Fitzer34/bor-systems/marketing/SALES_ONEPAGER.md

# HazardLink — Sales One-Pager

For warm intros, prospect handouts, and follow-up emails.

---

```
┌─────────────────────────────────────────────────────────────┐
│   HazardLink ⚠️                                              │
│   Smart wet-floor monitoring for commercial facilities       │
└─────────────────────────────────────────────────────────────┘
```

## The problem

Slip-and-fall is the **#1 cause of serious accidents** in commercial
premises — and a single incident can run to **tens of thousands** in
downtime, legal, and medical costs. Yet most facilities still rely on a
cleaner manually placing a yellow plastic sign and **hoping someone
moves it back**.

When the sign disappears, three things happen:

1. The cleaner has no idea
2. The supervisor has no proof of response time
3. There's no record it was ever dealt with

## The HazardLink fix

A sub-€1 magnetic sensor inside every wet-floor sign mount. The moment
a sign is lifted off the wall, the cloud knows. The cleaning team gets
a push notification within 3 seconds. Every event is timestamped and
photo-verified. The whole audit chain is cryptographically signed —
tamper-evident, so the record holds up.

## What the customer gets

| Feature | Outcome |
|---|---|
| Real-time push alerts | Average response time drops from 8 min → under 2 min |
| AirTag-style precision finding (UWB) | Cleaners locate the sign in any building in seconds |
| Auto-generated reports & records | A complete, exportable safety record — prove the job was done |
| Photo verification on close | Disputes resolved with evidence, not arguments |
| Multi-language alerts (6 languages) | Polish/Portuguese cleaners react faster |
| Anti-theft detection | Saves €300-600/yr in sign replacement |
| Heat-map analytics | Identifies repeat-offender zones (leaky vending machines, wet entrances) |
| Slack + Teams integration | Alerts post in the channel cleaning teams already use |

## How it installs

```
1. Wall-mount a hanger where each sign normally lives    (5 min each)
2. Plug a gateway box into power + Wi-Fi                 (10 min, once per building)
3. Hang your existing wet-floor signs on the hangers     (instant)
4. Cleaners install the iPhone / Android app             (5 min each)
5. Done — alerts start immediately
```

## Pricing

| Tier | Site size | Setup | Monthly |
|---|---|---|---|
| **Small** | Up to 10 hangers | €1,500 hardware | €30 / month |
| **Multi-site** | Up to 50 hangers | €6,500 hardware | €100 / month |
| **Enterprise** | 200+ hangers | €25,000+ hardware | €350 / month |

Hardware is a one-time purchase. Software subscription is month-to-month
— cancel any time with 30 days' notice.

## ROI for a 50-hanger site

The biggest return is preventing the incident in the first place — **one
avoided slip-and-fall pays for HazardLink for years.** On top of that, the
day-to-day savings:

| Item | Annual value |
|---|---|
| Anti-theft sign-replacement savings | €400 |
| Cleaner labour saved (faster response = less downstream cleanup) | €1,200 |
| Faster, evidenced incident handling | €3,000+ |
| **Ongoing savings** | **€4,600+ / year** |
| **Cost (hardware amortised over 5 years + €1,200 SaaS)** | **€2,500 / year** |

## Who's using it

(Pilot phase — willing to share names of design-partner sites once they
agree)

## Why us, why now

- **Built in Ireland**, hosted in EU — your data stays in your jurisdiction
- **No long contracts** — month-to-month, cancel any time
- **GDPR-native** — designed compliance-first, not bolted on
- **No replacement of your existing signs** — we make YOUR signs smart
- **Multi-language** — supports the actual labour pool in UK/IE cleaning

## Next step

15-minute demo on a live device — we show the alert flow on your own
phone within the first 90 seconds.

**Book**: hello@hazardlink.ie
**More**: https://hazardlink.ie
