Fitzer34/bor-systems/marketing/STORE_LISTINGS.md

# HazardLink — App Store + Play Store listings

Copy-paste-ready text for Apple App Store and Google Play Store
submissions. Both stores have character limits — these stay under them.

---

## App name
**HazardLink** (10 chars — well within Apple's 30 / Google's 50)

## Subtitle / Short description (Apple 30 / Google 80 chars)

**Apple**: `Smart wet-floor sign alerts`
**Google**: `Real-time alerts the moment a wet-floor sign is moved. Built-in safety records.`

---

## Promotional text (Apple, 170 chars, can be updated without re-review)

```
The moment a wet-floor sign is lifted, your cleaning team gets an alert — and every response is logged automatically. Built for facility safety teams.
```

---

## Full description (Apple 4000 chars / Google 4000 chars)

```
HazardLink turns ordinary wet-floor signs into connected safety sensors.
The moment one is lifted off its mount, your cleaning team gets a push
notification, the dashboard goes red, and the response is logged — every
step, with timestamps and photo evidence, so nothing slips through the cracks.

—— Why HazardLink ——

• REAL-TIME ALERTS — Phone, Apple Watch / Wear OS, Slack and Teams. You
  always know when a spill happens.

• AIRTAG-STYLE FIND — Ultra-Wideband precision finding (UWB) walks your
  cleaners straight to the lifted sign in any building. cm-level
  accuracy on iPhone 11+, Pixel 6 Pro+, Galaxy S21 Ultra+.

• REPORTS & RECORDS — Auto-generated reports document every spill,
  response time, and resolution. A complete, exportable safety record
  for your own health-and-safety reviews and accountability.

• PHOTO PROOF — Cleaners snap a quick photo of the cleaned area before
  closing each alert. Tamper-resistant audit trail.

• MULTI-LANGUAGE — Notifications in English, Polish, Portuguese,
  Spanish, Romanian and Lithuanian. Your cleaning team understands
  alerts in their native language.

• ANTI-THEFT — Signs that go missing for 24h auto-alert your admin
  team. Save €300–600 per year in replacement costs.

• HEAT-MAP ANALYTICS — Discover which zones are repeat offenders.
  Fix the root cause, not just the symptom.

• AFTER-HOURS MODE — Different escalation policy at night. Alerts
  route to your security guard rather than waking the cleaning team.

• SLACK + TEAMS — Post alerts straight into your existing channel.

—— How it works ——

1. We supply small hangers that mount on the wall (one per sign).
2. You hang your own existing wet-floor signs on them.
3. A magnet inside each sign keeps the hanger "armed".
4. The moment a cleaner lifts the sign, the magnetic field changes
   and a sub-€1 Hall sensor fires the alert.
5. The alert reaches phones, watches, and the web dashboard in
   under 5 seconds.

—— Who it's for ——

• Commercial cleaning companies managing multiple client sites
• Facility managers in offices, retail, hospitality, healthcare
• Health &amp; safety officers responsible for slip/trip prevention
• Any business where a sudden spill needs a cleaning response

—— Hardware ——

Hangers run on a single rechargeable 21700 lithium cell — one charge
per year. Sign tags use replaceable CR2032 cells (2-year life). Gateway
is a small Wi-Fi puck (one per building, USB-C powered).

—— Open standards ——

LoRa for sign-to-gateway communication. BLE for first-time Wi-Fi setup.
UWB for precision finding. Multi-tenant cloud with end-to-end HMAC.
Sentry monitoring. Public status page.

Questions? hello@hazardlink.ie
```

---

## Keywords (Apple, 100 chars comma-separated)

```
spill,floor,safety,sign,cleaning,alert,compliance,facility,janitor,hazard,IoT,monitoring,wet,slip
```

---

## Categories

**Apple**:
- Primary: **Business**
- Secondary: **Productivity**

**Google**:
- Category: **Business**
- Tags: business management, safety, IoT

---

## Content rating

**Apple**: 4+ (no objectionable content)
**Google**: Everyone

---

## Privacy nutrition (Apple — what your app collects)

Data linked to user identity:
- Contact Info: email address (for account)
- Identifiers: device ID (for push notifications)
- Diagnostics: crash data (Sentry, no PII)

Data NOT linked to user identity:
- Usage data: alert response times (aggregated for analytics)

Data NOT collected:
- Location, photos (other than user-uploaded resolution photos), audio,
  contacts, browsing history, advertising data.

---

## Data safety (Google Play — same info, different form)

Data collected: email, device push token, photos uploaded by user
Data shared: NO (we don't share data with third parties beyond service providers)
Encryption in transit: YES (TLS 1.2+)
Data deletion request: support@hazardlink.ie

---

## Screenshots needed (both stores)

Suggested 5 screenshots per device size:

1. **Live alerts feed** — Active alert with red pin on floor plan
2. **AirTag-style Find Sign view** — arrow + distance
3. **Reports preview** — page with summary + response times
4. **Multi-site dashboard** — grid of buildings sorted by open alerts
5. **Heat-map analytics** — zones colour-coded by spill frequency

Device sizes Apple requires:
- 6.7" iPhone (1290×2796)
- 6.5" iPhone (1242×2688)
- iPad Pro 13" (2064×2752) — only if you ship iPad-compatible (we don't)

Device sizes Google requires:
- Phone: 1080×1920 minimum
- 7" tablet: 1200×1920
- 10" tablet: 1920×2560

Use Figma or Sketch to mockup; or take real screenshots from your dev
device and add a phone frame in a tool like https://mockuphone.com.

---

## What's new (release notes) — first version

```
Welcome to HazardLink.

This is our first public release. Wet-floor sign monitoring with
real-time push alerts, multi-language notifications, Apple Watch
and Wear OS support, and built-in safety reports.

Pair your first hanger via Bluetooth in 60 seconds.
```

---

## Support URL
https://hazardlink.ie/support

## Marketing URL
https://hazardlink.ie

## Privacy policy URL (REQUIRED both stores)
https://hazardlink.ie/privacy

---

## Beta testing setup

**Apple TestFlight**: invite up to 100 testers via email or public link.
No review for internal builds; ~24h review for external builds.

**Google Play Internal Testing**: invite up to 100 testers via email.
No review. Closed Testing (12+ testers for 14 days) needed before
Production access for new Personal-tier developer accounts.
