Fitzer34/bor-systems/hardware/enclosures/v8/A/README.txt

HazardLink v8 enclosures, Designer A (robust and serviceable)
Generated by hazardlink_enclosures.py. Frame: X right, Z up, Y from the front face into the wall.

FILES
  <part>.step / .stl / .png / _drawing.dxf   printable parts: hanger_body, hanger_lid, hanger_hook, hanger_backplate, gateway_body, gateway_lid
  hanger_assembly.step, gateway_assembly.step  named and coloured assemblies including the reference solids
  hanger_section.dxf, gateway_section.dxf      assembly stack-up sections
  *_exploded.png, *_assembled*.png             previews
  ref/                                          reference solids (board, cell, holder, Hall carrier, magnet, antenna, plug), not printed
  autocad/                                      .sat + 3DSOLID .dxf for AutoCAD for Mac (from to_autocad.py)
  manifest.txt                                  bounding boxes and derived positions

HANGER SERVICE SEQUENCE (unit stays on the wall)
  1. Remove the two M3 pin-Torx button-head screws in the hook base (driver enters between the side gussets, under the arm).
     Lift the hook off its locating pocket, slide the Hall carrier out of the hook slot; it passes through the lid slot.
  2. Remove the four M3 pin-Torx countersunk lid screws. Lift the lid straight off (the lip is 4 mm deep).
  3. The 21700 cell sits in its holder facing you: push it against the spring end and lift it out. Fit the new cell, same polarity.
  4. To swap the board: unplug the JST 1.25 battery lead (under the board, plug enters from the right), unplug the U.FL antenna,
     unsolder or cut the three Hall wires at the board underside pads (J3 pin 1 GND, pin 2 3V3, pin 17 GPIO6), lift the board
     off its rails. No screws hold the board: it rests on the rails and is clamped by the two lid ribs.
  5. Refit in reverse. Insert the cell last, close the lid within the 60 s commissioning window, or press RST (2 mm pinhole) later.
  To take the unit off the wall: with the lid off, remove the internal M3 screw at (50, 62) through the back wall, then lift the body
  14 mm and pull it off the four backplate pegs.

GATEWAY SERVICE SEQUENCE
  1. Remove the six M3 countersunk lid screws, lift the lid.
  2. Unplug the USB-C plug (cable stays tied to the saddle), unplug the U.FL pigtail, lift the board off its rails.

MAGNET DATUM (publish to the sign tag)
  Magnet on the hook centreline (x=50), 8 mm out from the hook base front face (Y=-16), pole face parallel to the arm top surface,
  facing down, with 1.0 mm running clearance and a 1.2 mm tag wall (assumed). Air gap magnet face to Hall package top = 3.98 mm.
  The arm top slopes up 3 mm over its length so the handle slides to the root and rests there.

PRINTING (PETG, 0.4 nozzle, 3 perimeters, 0.2 layers)
  hanger_body: back face down, open front up. Peg pocket roofs bridge 11.5 mm; lead notch bridges 8 mm.
  hanger_lid: outer face down. PRG tab and LED window are thin skins on the bed. Fit the 36 x 19.5 x 1 mm clear insert from inside
  under the two cleats.
  hanger_hook: lying on a side (X) face so layers run along the arm. Counterbores print horizontal.
  hanger_backplate: back face down, pegs print vertical.
  gateway_body: back face down. gateway_lid: outer face down.
  Heat-set inserts: ruthex M3 x 5.7 (4.0 mm holes): 4 lid + 2 hook in the hanger body, 1 security in the backplate, 6 in the gateway body.
  Screws (assumed, not on SHOPPING.md): M3 x 8 countersunk pin-Torx x 4 (hanger lid), M3 x 12 button-head pin-Torx x 2 (hook),
  M3 x 8 countersunk x 6 (gateway lid), M3 x 8 pan head x 1 (internal security screw), 4 + 3 No.8 pan/csk wall screws with plugs.
  Use A2 stainless or brass for the two hook screws (they sit 16 mm from the Hall sensor).

MEASURE BEFORE FREEZING (assumed values in PARAMS)
  The TinyTronics 21700 holder outline (assumed 80 x 25 x 21 mm) and where its leads exit.
  The sign hand-hole and handle bar: hook width 26, arm 45, lip 22 are assumed; the magnet position in the handle must match the datum.
  How far the sign top rises above the handle bar: the OLED window bottom is 42 mm above the arm top at the root.
  The stub antenna diameter and length (clips are for a 6 mm rod, 60 mm long).
  The OLED active area offset (window is 30 x 16 to cover it with margin).
