Fitzer34/bor-systems/hardware/enclosures/ref/heltec-wifi-lora-32-v3/datasheet_p14_physical_dimensions.png

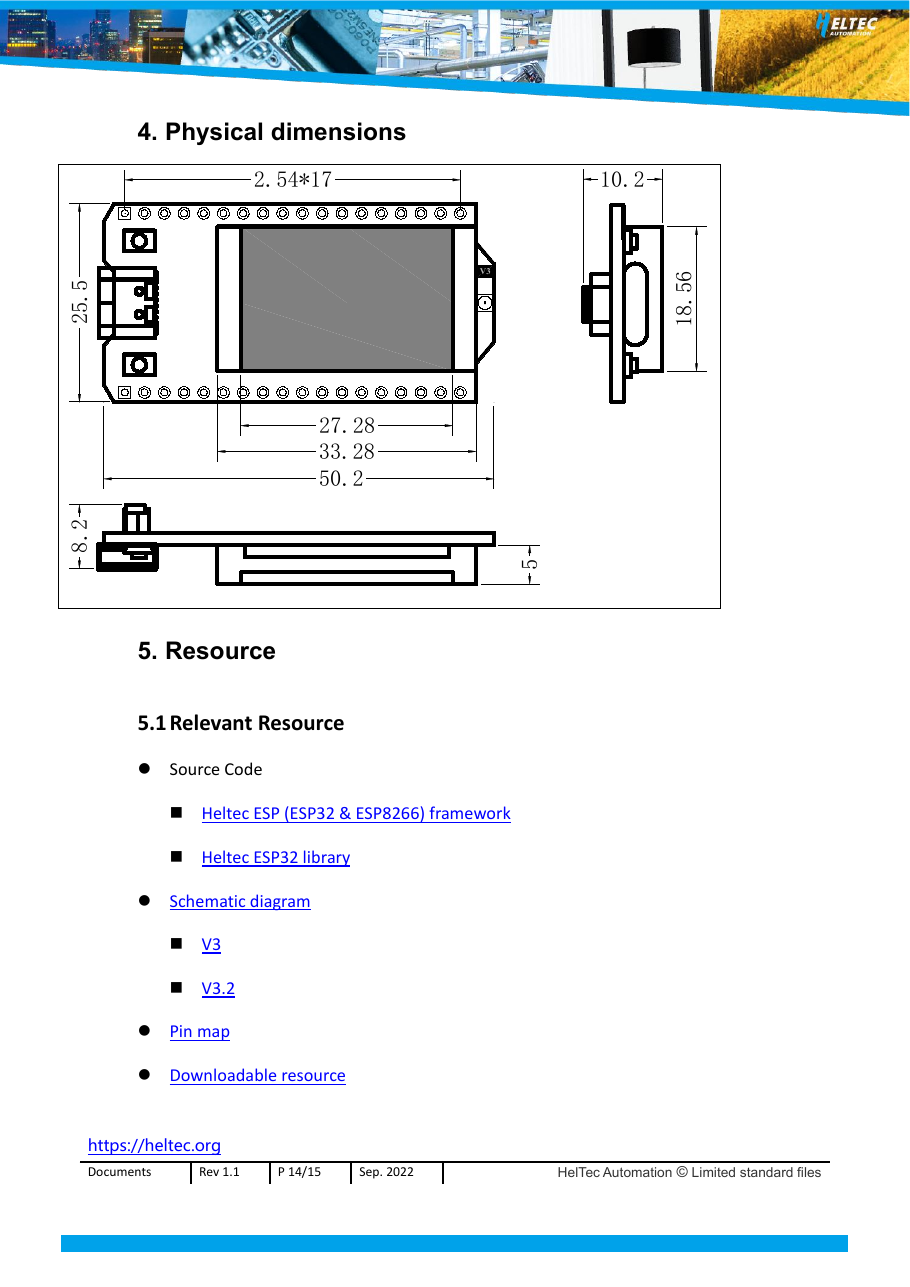
hardware/enclosures/ref/heltec-wifi-lora-32-v3/datasheet_p14_physical_dimensions.png
