Fitzer34/bor-systems/hardware/enclosures/ref/heltec-wifi-lora-32-v3/photo_underside_V3.png

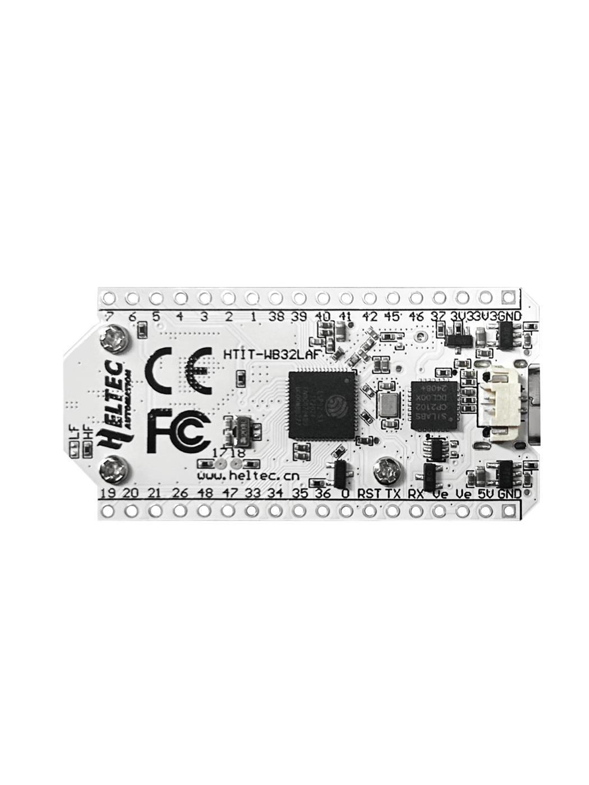
hardware/enclosures/ref/heltec-wifi-lora-32-v3/photo_underside_V3.png
