Fitzer34/bor-systems/hardware/enclosures/ref/heltec-wifi-lora-32-v3/pinmap_V3.2.png

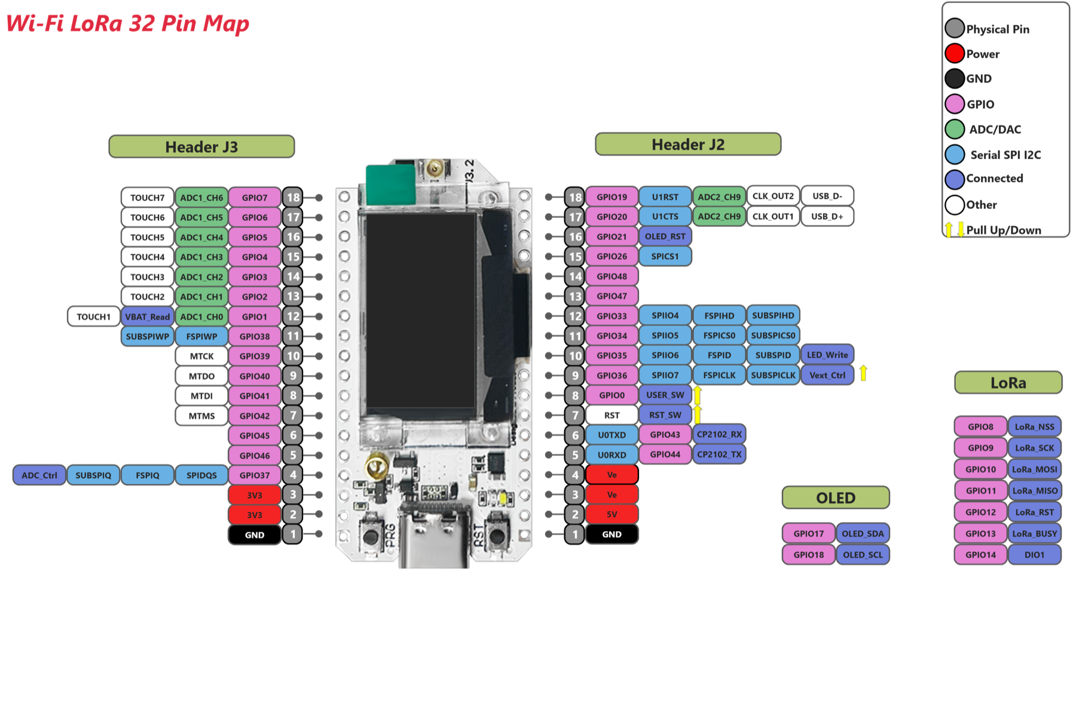
hardware/enclosures/ref/heltec-wifi-lora-32-v3/pinmap_V3.2.png
