Fitzer34/bor-systems/hardware/enclosures/v9/closeups/backplate_front.png

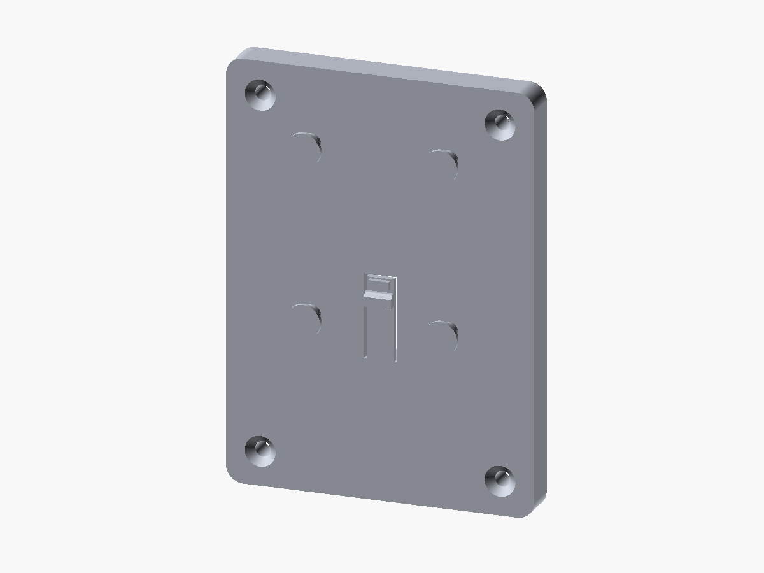
hardware/enclosures/v9/closeups/backplate_front.png
