Fitzer34/bor-systems/hardware/enclosures/v9/closeups/bar_plate.png

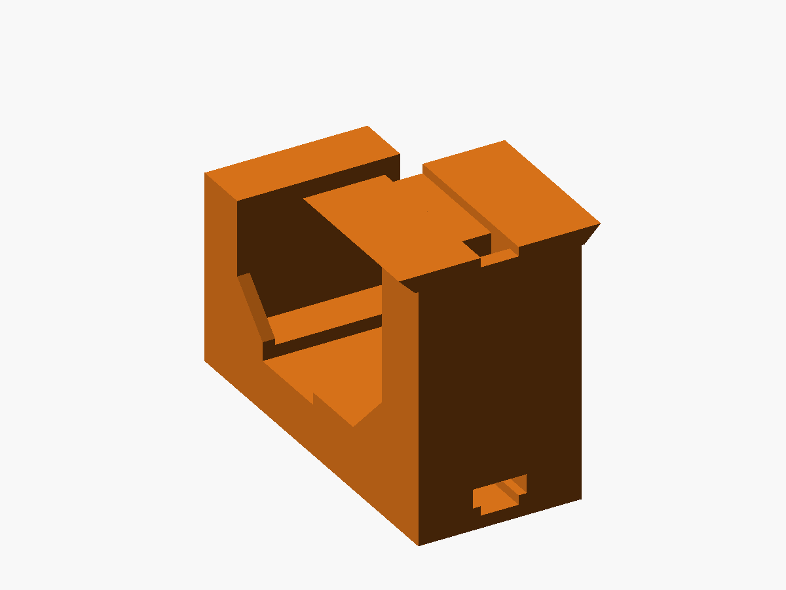
hardware/enclosures/v9/closeups/bar_plate.png
