Fitzer34/bor-systems/hardware/enclosures/v9/closeups/body_bottom.png

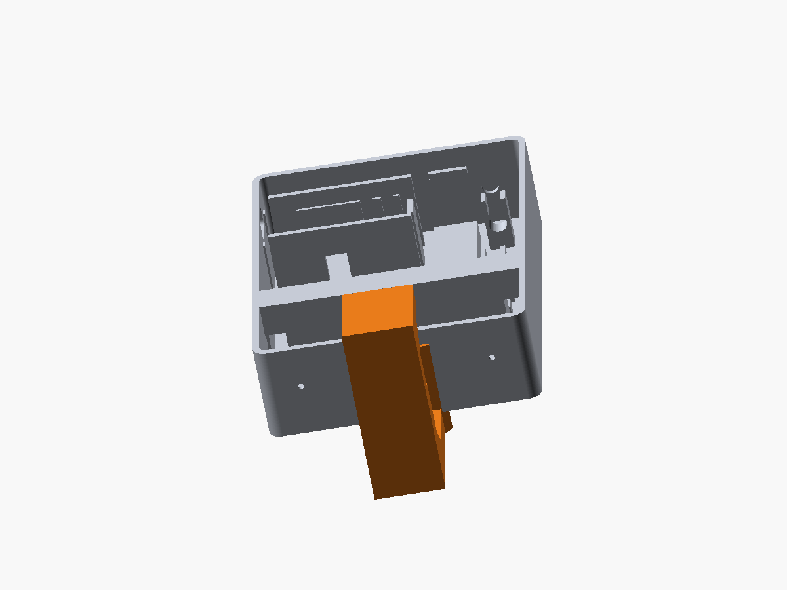
hardware/enclosures/v9/closeups/body_bottom.png
