Fitzer34/bor-systems/hardware/enclosures/v9/closeups/body_top.png

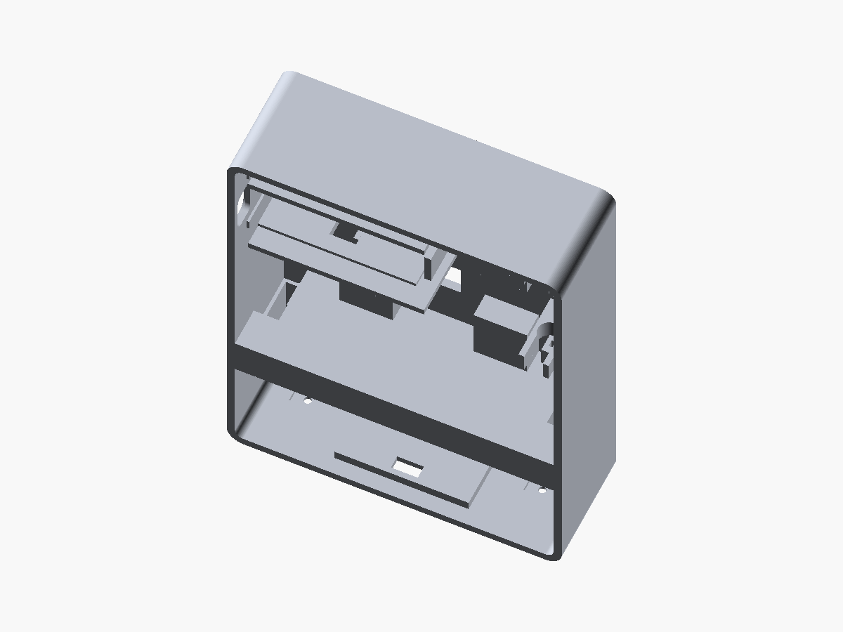
hardware/enclosures/v9/closeups/body_top.png
