Fitzer34/bor-systems/hardware/enclosures/v9/closeups/body_underside.png

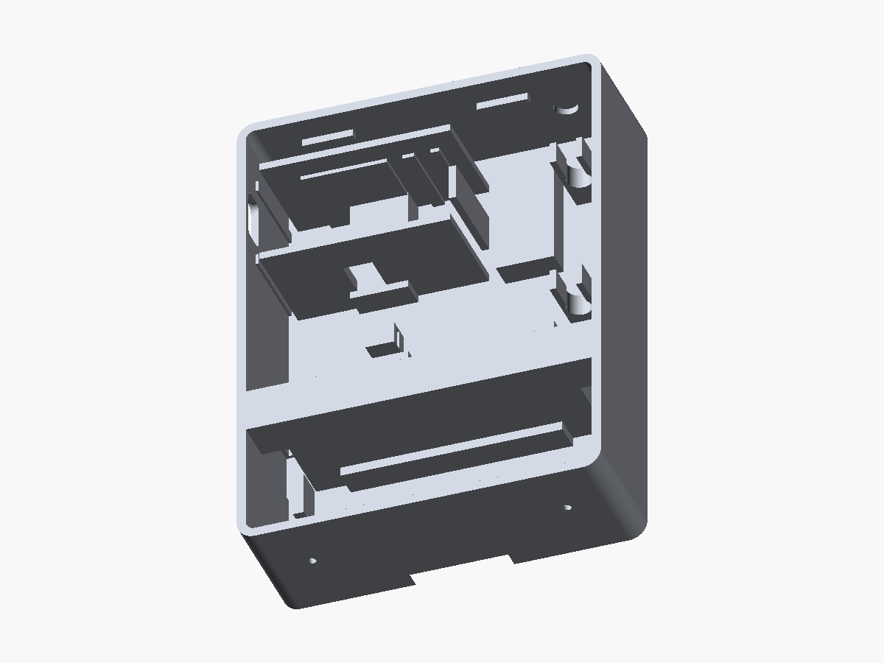
hardware/enclosures/v9/closeups/body_underside.png
