Fitzer34/bor-systems/hardware/enclosures/v9/closeups/coupon.png

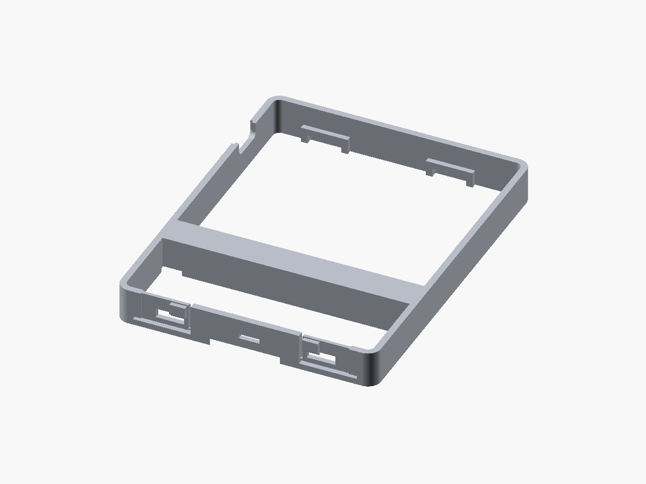
hardware/enclosures/v9/closeups/coupon.png
