Fitzer34/bor-systems/hardware/enclosures/v9/closeups/face_flush.png

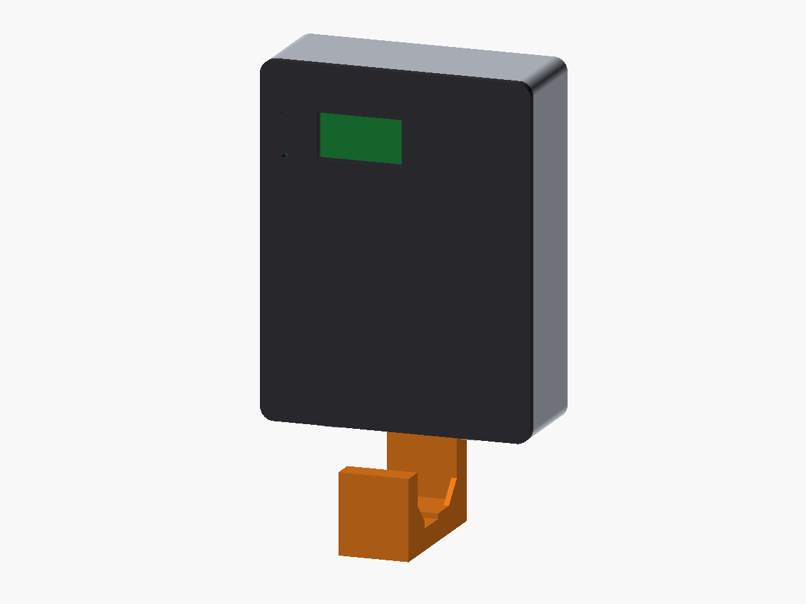
hardware/enclosures/v9/closeups/face_flush.png
