Fitzer34/bor-systems/hardware/enclosures/v9/closeups/finished_gateway.png

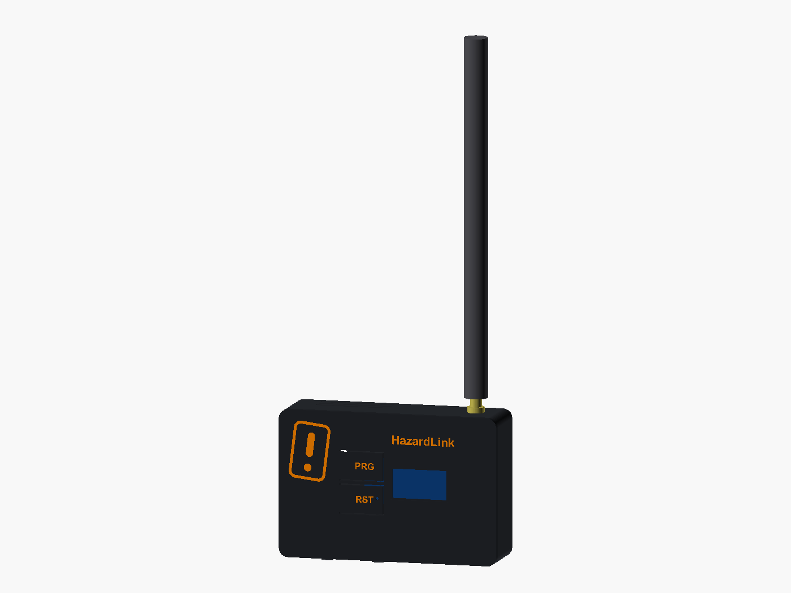
hardware/enclosures/v9/closeups/finished_gateway.png
