Fitzer34/bor-systems/hardware/enclosures/v9/closeups/finished_usb_side.png

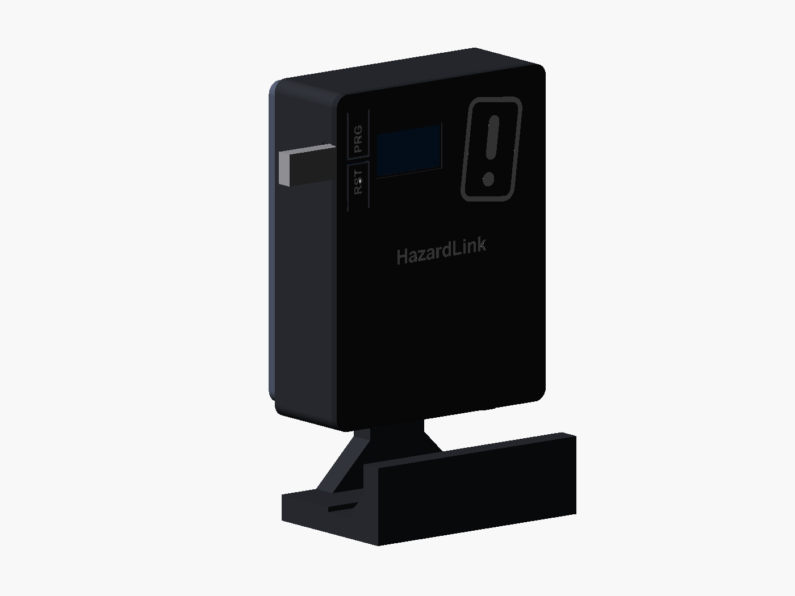
hardware/enclosures/v9/closeups/finished_usb_side.png
