Fitzer34/bor-systems/hardware/enclosures/v9/closeups/finished_with_sign.png

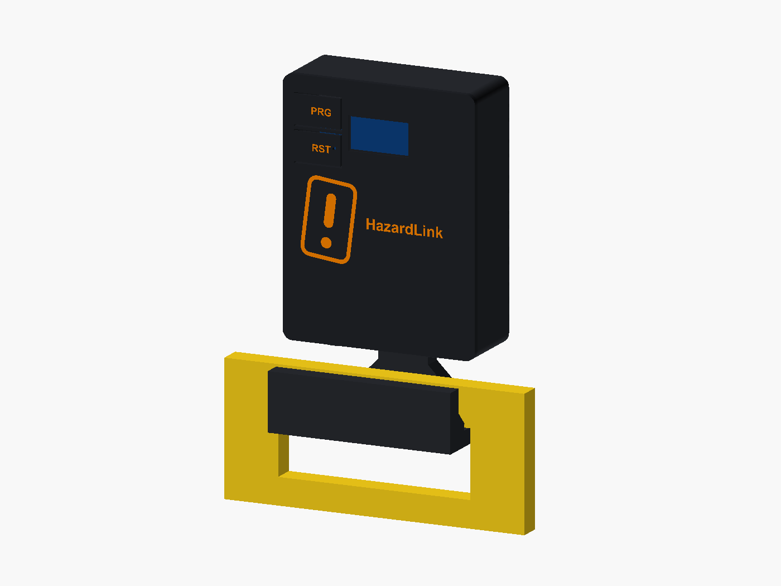
hardware/enclosures/v9/closeups/finished_with_sign.png
