Fitzer34/bor-systems/hardware/enclosures/v9/closeups/gateway_lid_inside.png

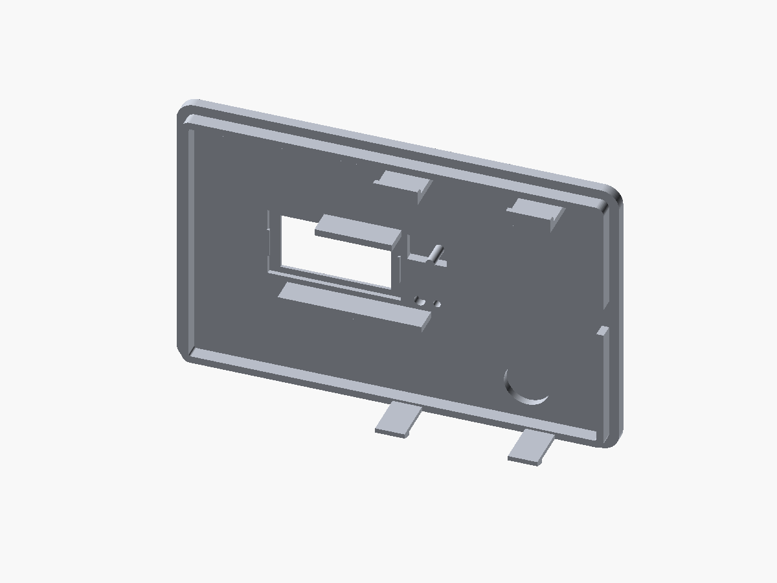
hardware/enclosures/v9/closeups/gateway_lid_inside.png
