Fitzer34/bor-systems/hardware/enclosures/v9/closeups/lid_edge.png

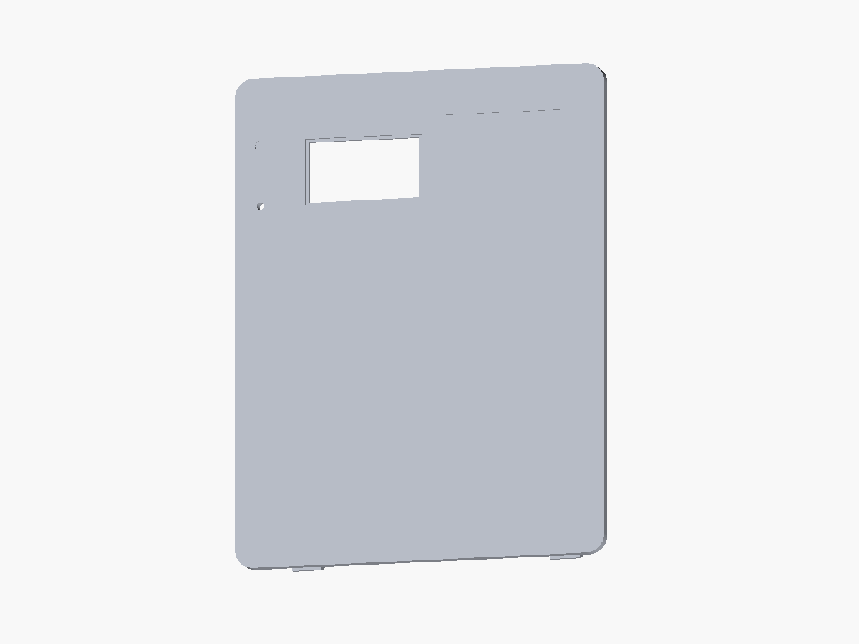
hardware/enclosures/v9/closeups/lid_edge.png
