Fitzer34/bor-systems/hardware/enclosures/v9/closeups/lid_off_clips.png

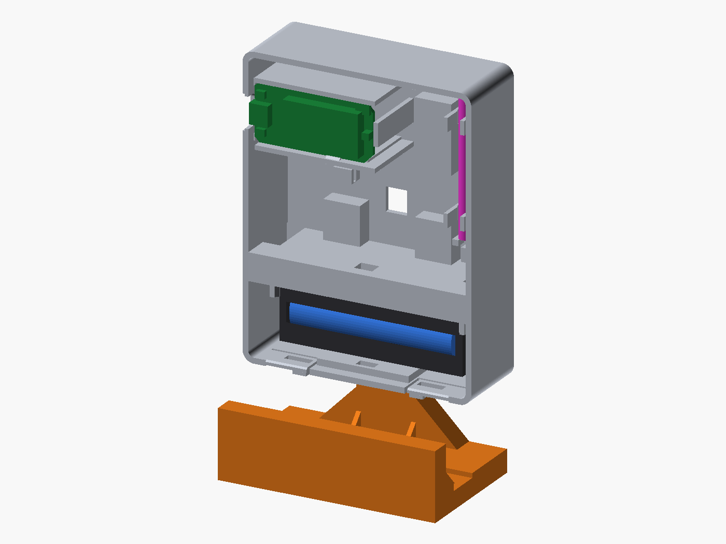
hardware/enclosures/v9/closeups/lid_off_clips.png
