Fitzer34/bor-systems/hardware/enclosures/v9/gateway_body.png

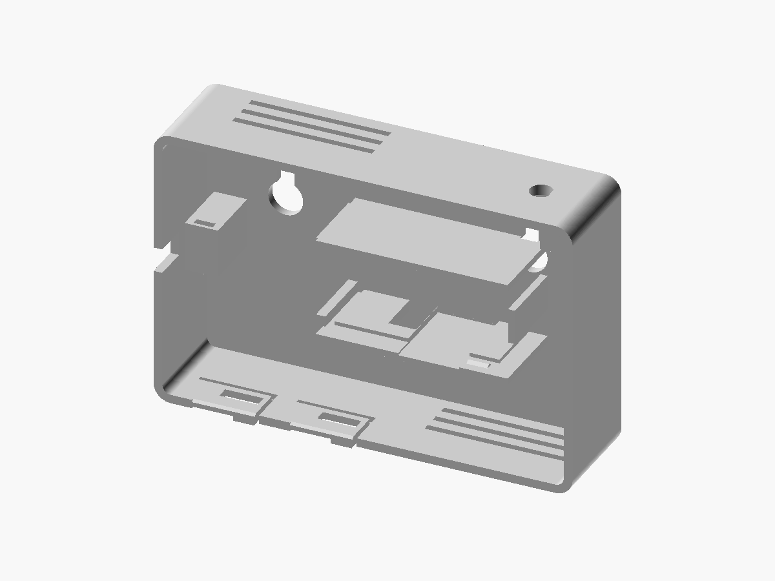
hardware/enclosures/v9/gateway_body.png
