Fitzer34/bor-systems/hardware/enclosures/v9/gateway_exploded.png

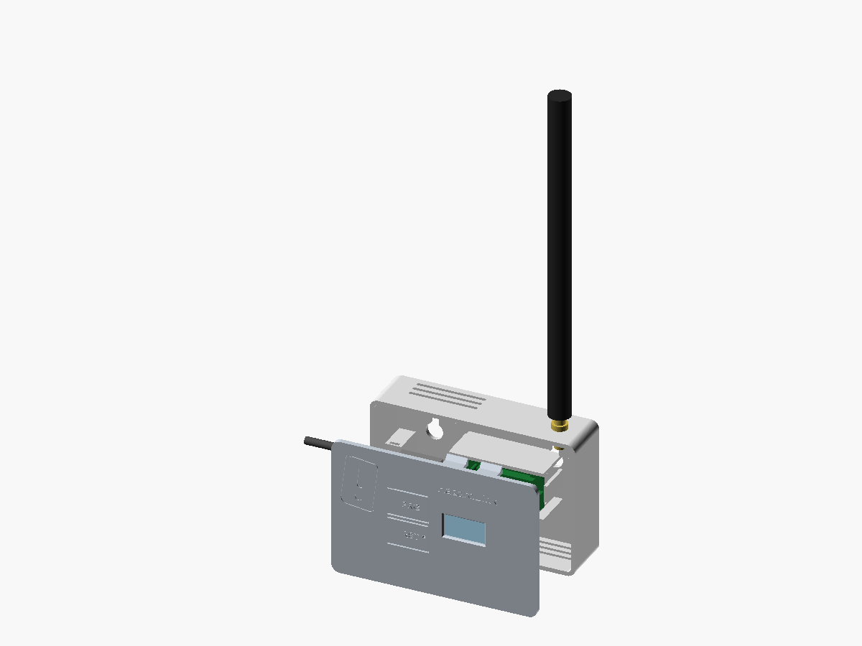
hardware/enclosures/v9/gateway_exploded.png
