Fitzer34/bor-systems/hardware/enclosures/v9/gateway_lid.png

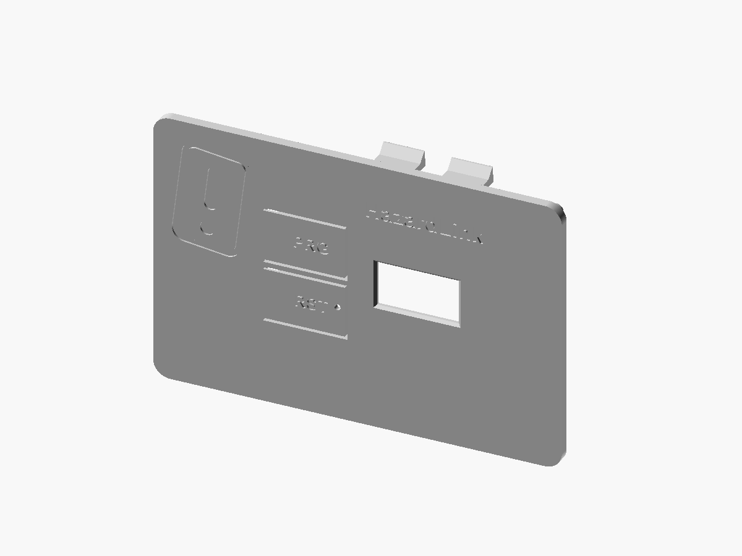
hardware/enclosures/v9/gateway_lid.png
