Fitzer34/bor-systems/hardware/enclosures/v9/hanger_backplate.png

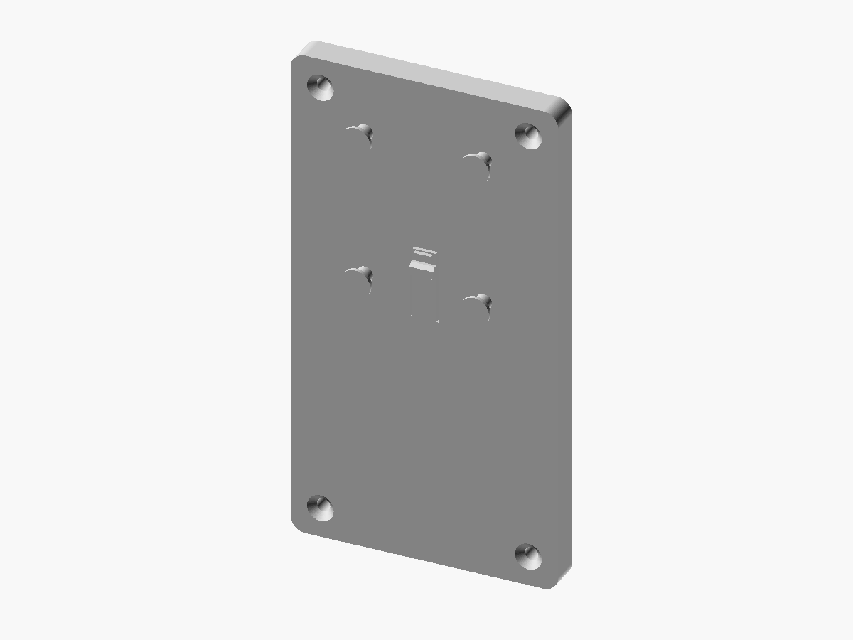
hardware/enclosures/v9/hanger_backplate.png
