Fitzer34/bor-systems/hardware/enclosures/v9/hanger_bar.png

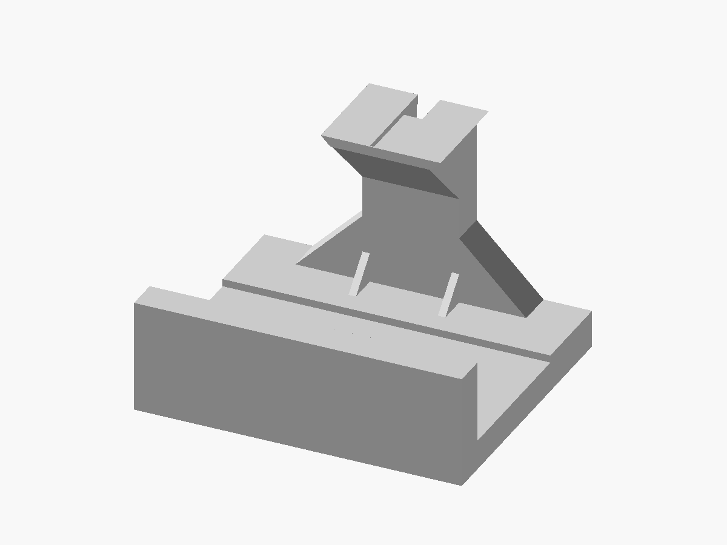
hardware/enclosures/v9/hanger_bar.png
