Fitzer34/bor-systems/hardware/enclosures/v9/hanger_bar_underside.png

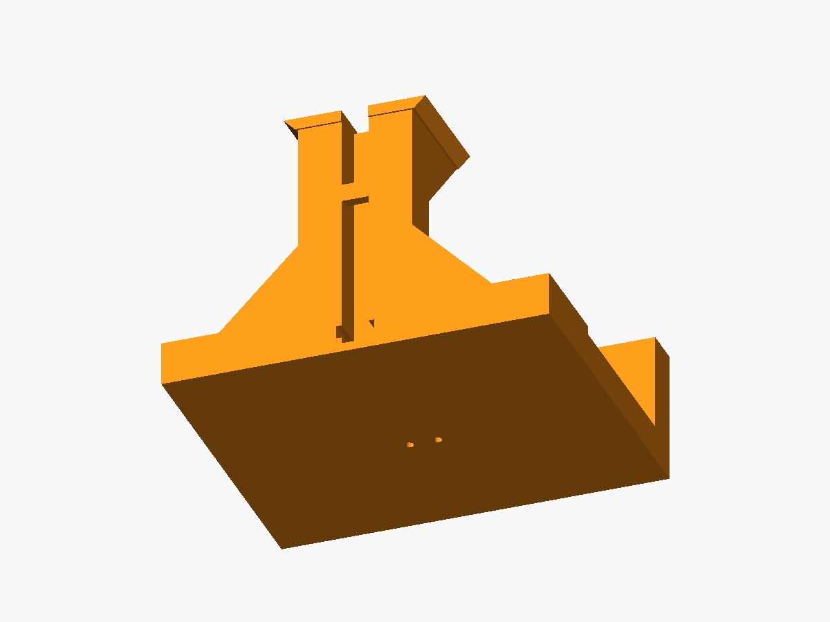
hardware/enclosures/v9/hanger_bar_underside.png
