Fitzer34/bor-systems/hardware/enclosures/v9/hanger_lid.png

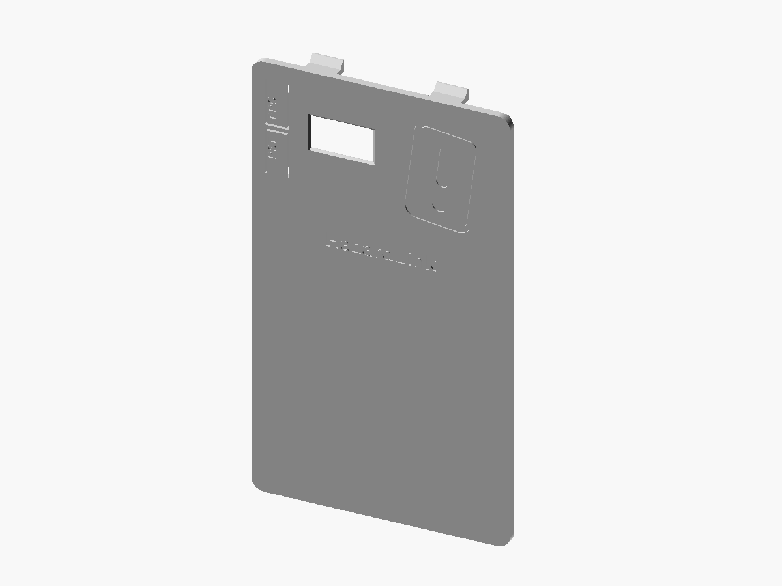
hardware/enclosures/v9/hanger_lid.png
