Fitzer34/bor-systems/hardware/enclosures/v9/hanger_lid_inside.png

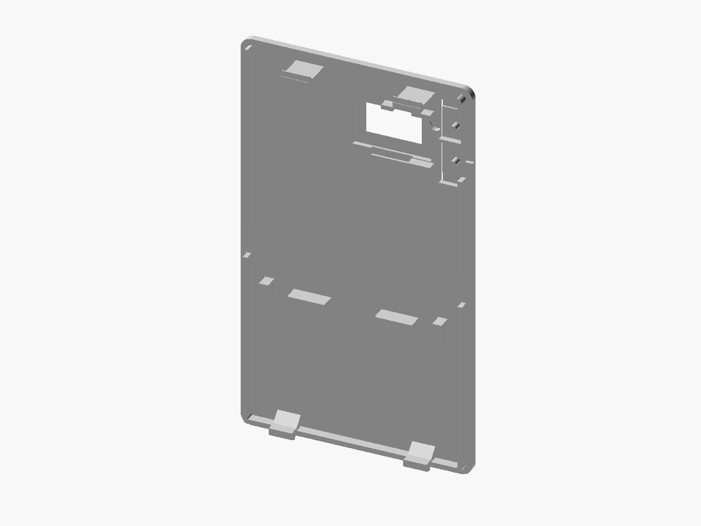
hardware/enclosures/v9/hanger_lid_inside.png
