Fitzer34/bor-systems/hardware/enclosures/v9/ref/hanger_stub_antenna.step

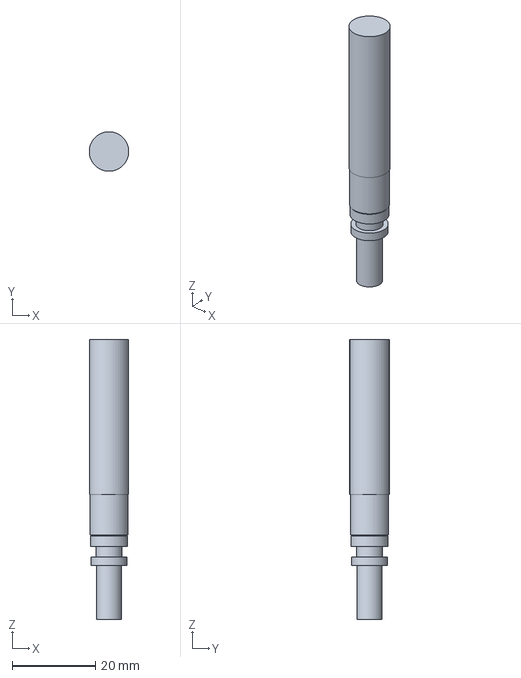
[picture p46: CAD file, 2026-09-26]
hardware/enclosures/v9/ref/hanger_stub_antenna.step
9.49 x 9.50 x 67.3 mm
