Fitzer34/bor-systems/hardware/enclosures/v9/stages/S5_bar.step

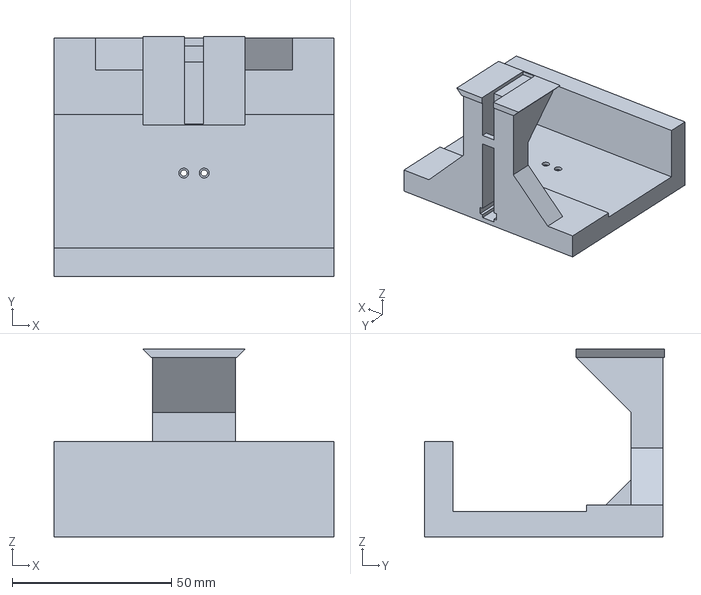
[picture p47: CAD file, 2026-09-20]
hardware/enclosures/v9/stages/S5_bar.step
88.0 x 75.5 x 59.0 mm
