Fitzer34/bor-systems/hardware/enclosures/v9/gateway_body.step

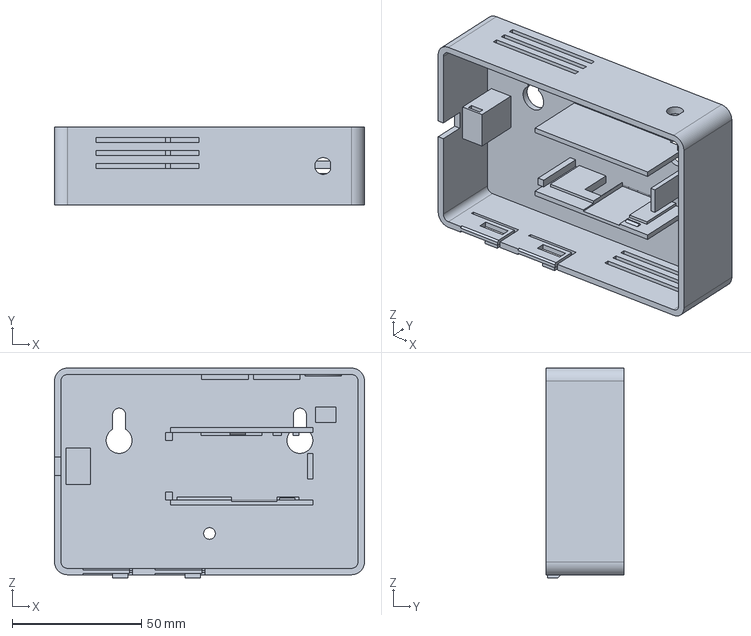
[picture p48: CAD file, 2026-09-26]
hardware/enclosures/v9/gateway_body.step
120.0 x 30.0 x 81.2 mm
