Fitzer34/bor-systems/hardware/enclosures/v9/hanger_section.dxf

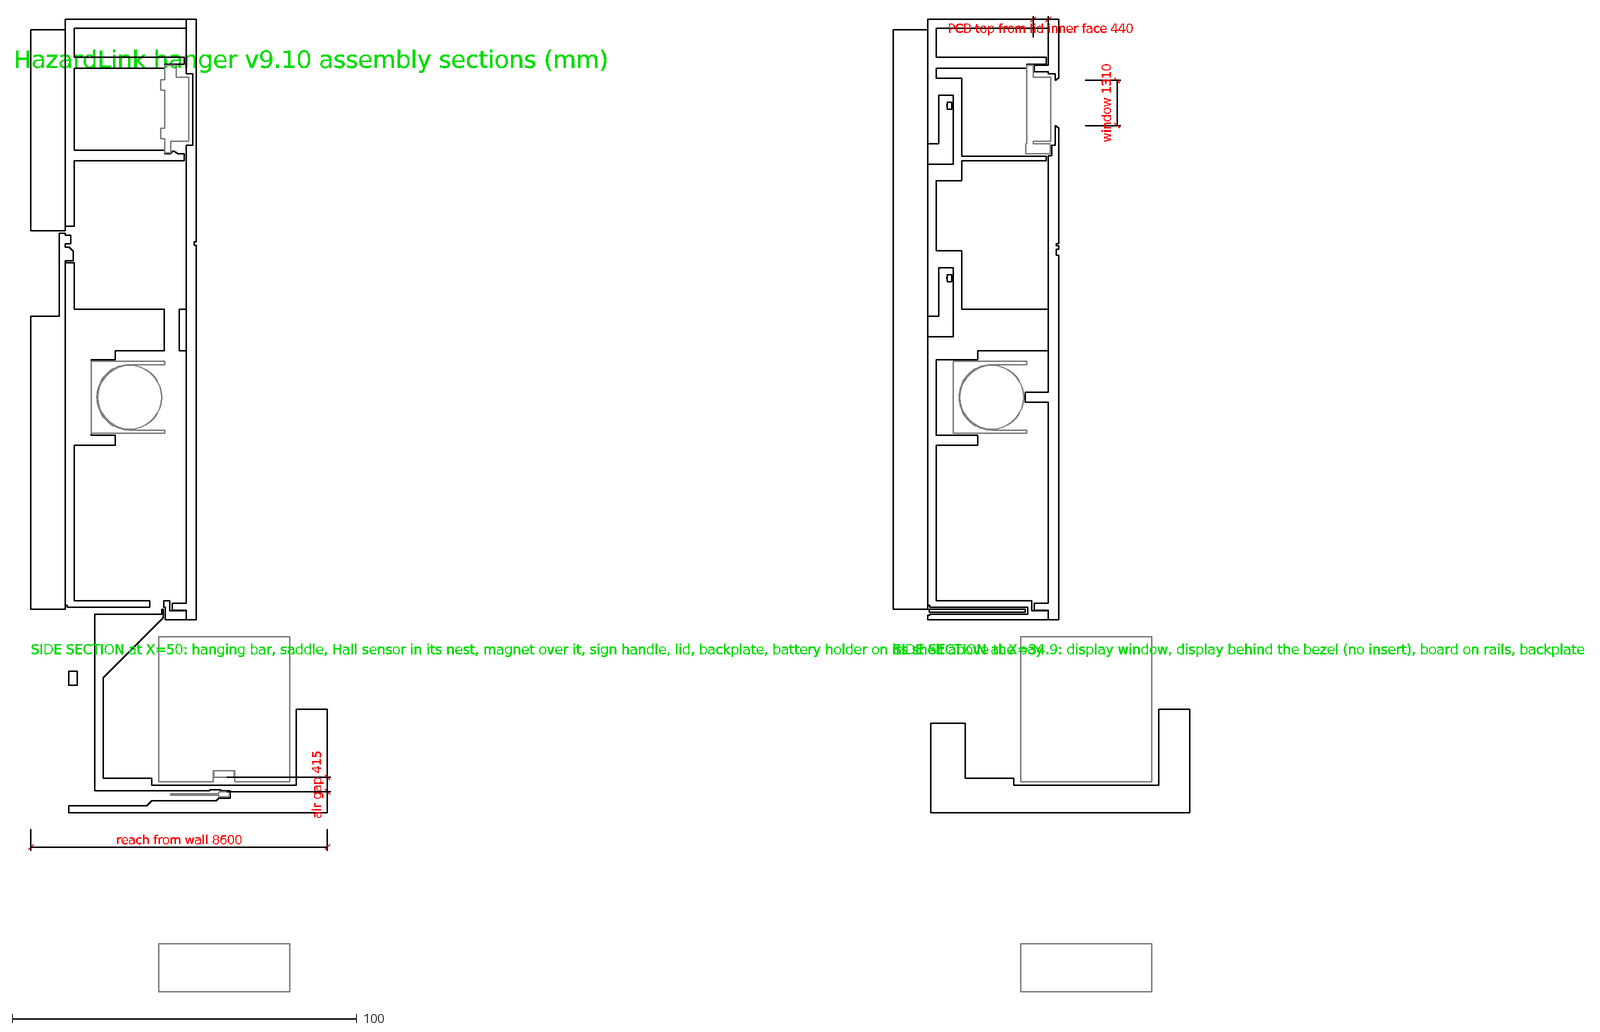
[picture p49: CAD file, 2026-09-26]
hardware/enclosures/v9/hanger_section.dxf
HazardLink hanger v9.10 assembly sections (mm)
SIDE SECTION at X=50: hanging bar, saddle, Hall sensor in its nest, magnet over it, sign handle, lid, backplate, battery holder on its shelf above the bay
SIDE SECTION at X=34.9: display window, display behind the bezel (no insert), board on rails, backplate
air gap 415
reach from wall 8600
window 1310
PCB top from lid inner face 440
