Fitzer34/bor-systems/hardware/enclosures/v9/ref/hanger_hall_pin.step

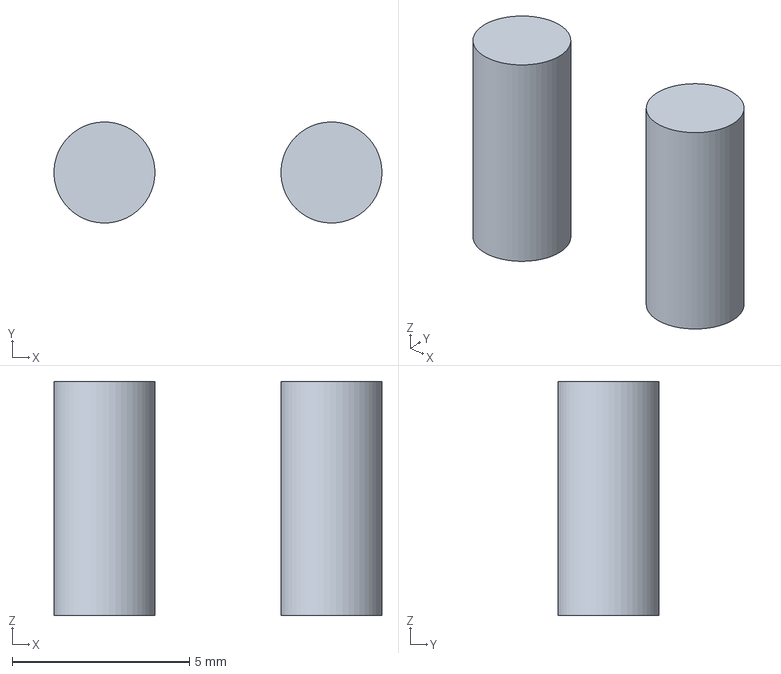
[picture p50: CAD file, 2026-09-26]
hardware/enclosures/v9/ref/hanger_hall_pin.step
9.25 x 2.85 x 6.60 mm
