Fitzer34/bor-systems/hardware/enclosures/v9/hanger_backplate_drawing.dxf

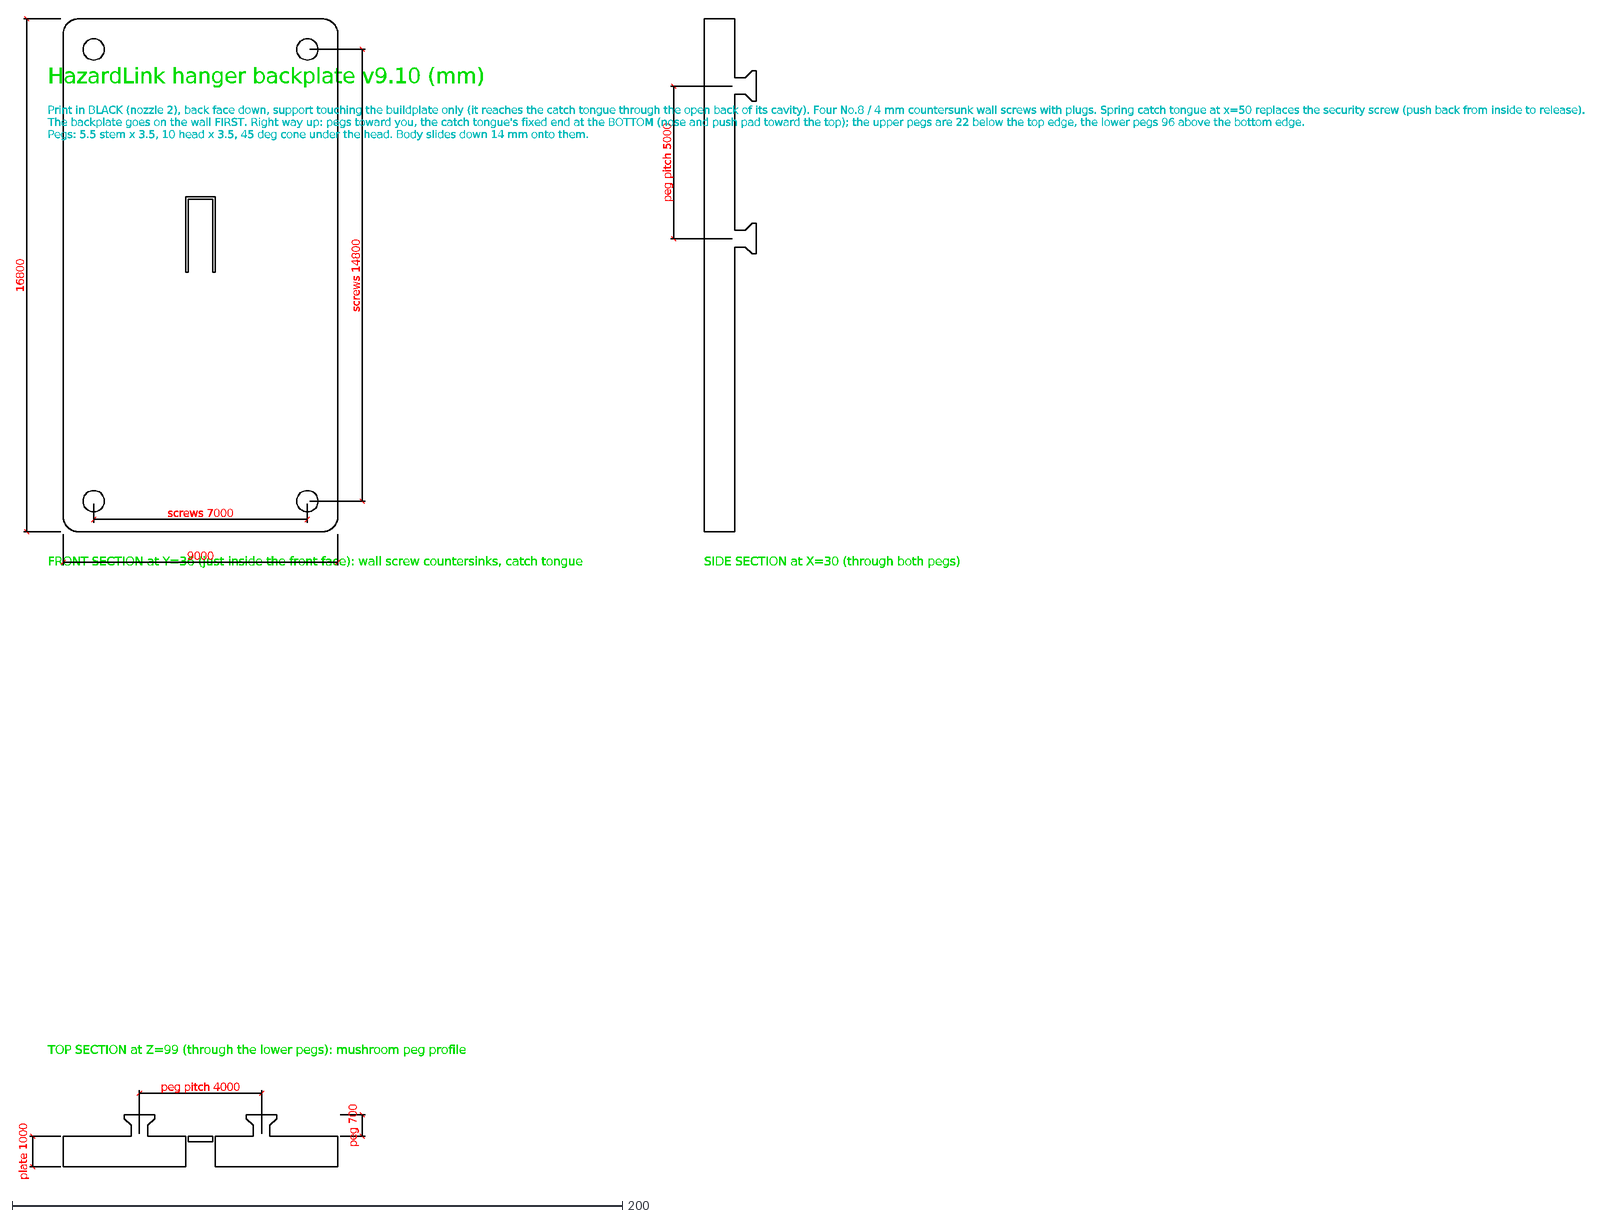
[picture p51: CAD file, 2026-09-26]
hardware/enclosures/v9/hanger_backplate_drawing.dxf
HazardLink hanger backplate v9.10 (mm)
FRONT SECTION at Y=36 (just inside the front face): wall screw countersinks, catch tongue
9000
16800
screws 7000
screws 14800
TOP SECTION at Z=99 (through the lower pegs): mushroom peg profile
plate 1000
peg 700
peg pitch 4000
SIDE SECTION at X=30 (through both pegs)
peg pitch 5000
Print in BLACK (nozzle 2), back face down, support touching the buildplate only (it reaches the catch tongue through the open back of its cavity). Four No.8 / 4
The backplate goes on the wall FIRST. Right way up: pegs toward you, the catch tongue's fixed end at the BOTTOM (nose and push pad toward the top); the upper pe
Pegs: 5.5 stem x 3.5, 10 head x 3.5, 45 deg cone under the head. Body slides down 14 mm onto them.
