Fitzer34/bor-systems/hardware/enclosures/v9/ref/hanger_sign_handle.step

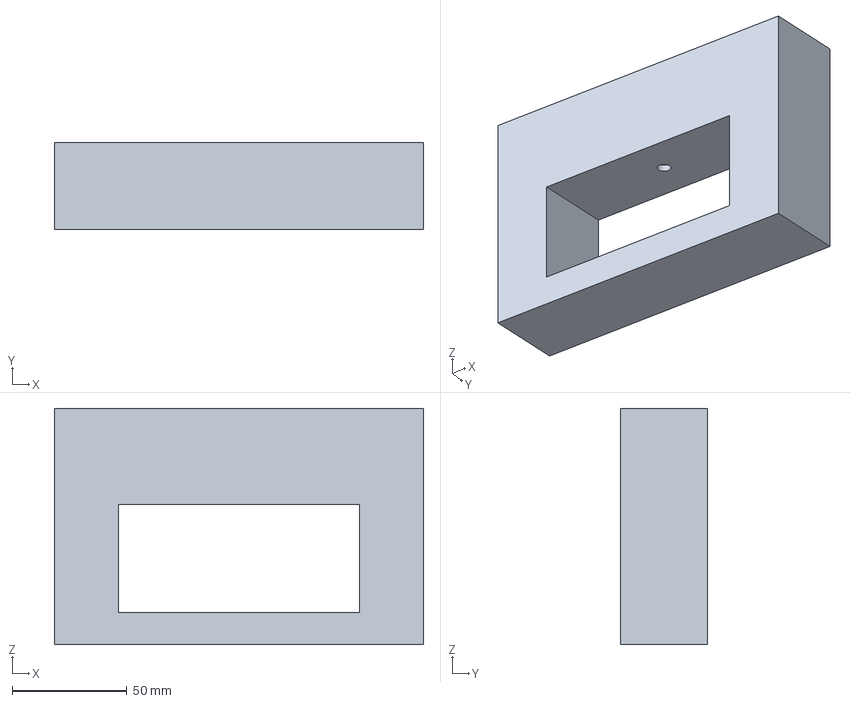
[picture p52: CAD file, 2026-09-26]
hardware/enclosures/v9/ref/hanger_sign_handle.step
161.0 x 38.0 x 103.0 mm
