Fitzer34/bor-systems/hardware/enclosures/v9/gateway_body_drawing.dxf

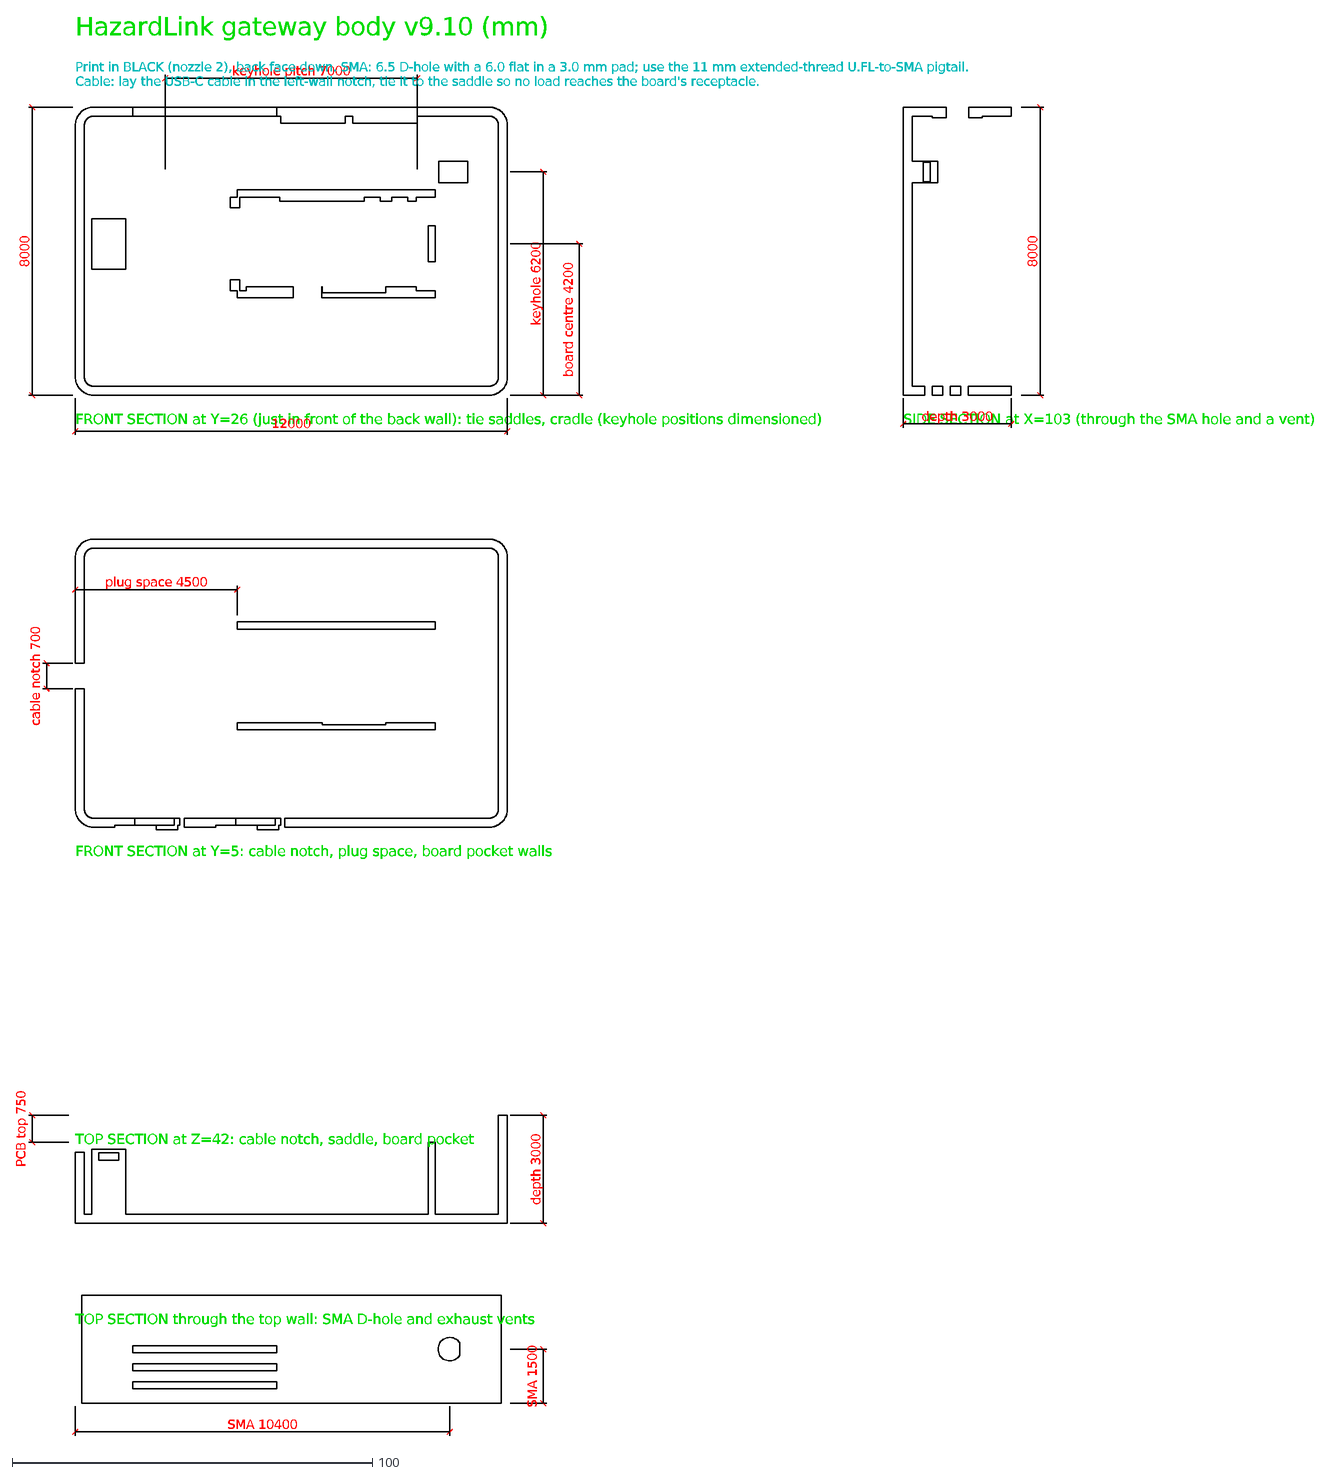
[picture p53: CAD file, 2026-09-26]
hardware/enclosures/v9/gateway_body_drawing.dxf
HazardLink gateway body v9.10 (mm)
FRONT SECTION at Y=26 (just in front of the back wall): tie saddles, cradle (keyhole positions dimensioned)
12000
8000
keyhole pitch 7000
keyhole 6200
board centre 4200
FRONT SECTION at Y=5: cable notch, plug space, board pocket walls
cable notch 700
plug space 4500
TOP SECTION at Z=42: cable notch, saddle, board pocket
depth 3000
PCB top 750
TOP SECTION through the top wall: SMA D-hole and exhaust vents
SMA 10400
SMA 1500
SIDE SECTION at X=103 (through the SMA hole and a vent)
Print in BLACK (nozzle 2), back face down. SMA: 6.5 D-hole with a 6.0 flat in a 3.0 mm pad; use the 11 mm extended-thread U.FL-to-SMA pigtail.
Cable: lay the USB-C cable in the left-wall notch, tie it to the saddle so no load reaches the board's receptacle.
