Fitzer34/bor-systems/hardware/enclosures/v9/ref/hanger_clean_button.step

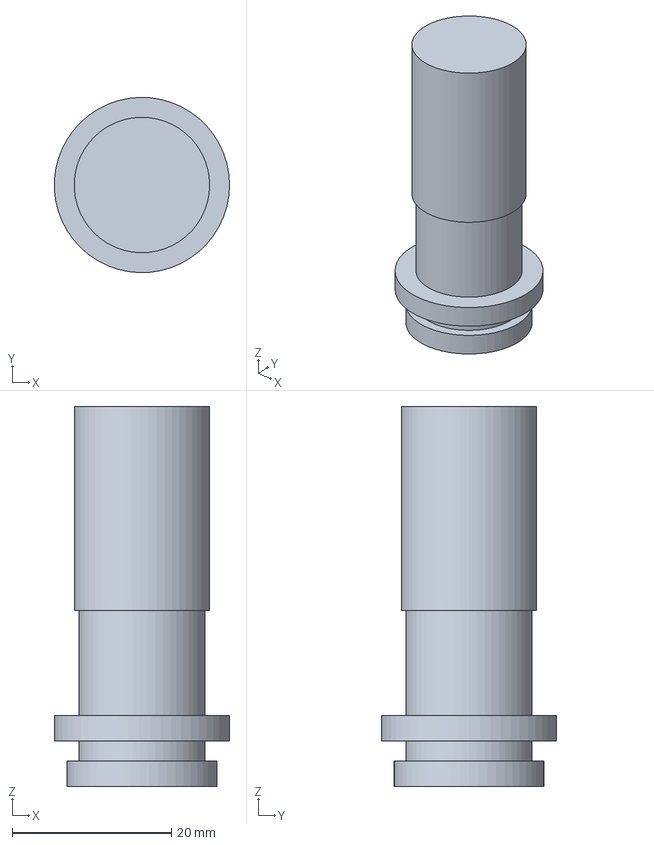
[picture p54: CAD file, 2026-09-26]
hardware/enclosures/v9/ref/hanger_clean_button.step
22.0 x 22.0 x 47.7 mm
