Fitzer34/bor-systems/hardware/enclosures/v9/stages/S1_body.step

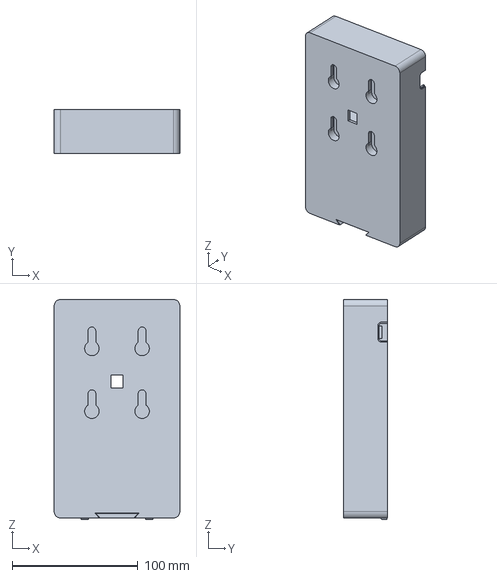
[picture p55: CAD file, 2026-09-20]
hardware/enclosures/v9/stages/S1_body.step
100.0 x 35.0 x 175.2 mm
