Fitzer34/bor-systems/hardware/enclosures/v9/ref/gateway_sma_jack.step

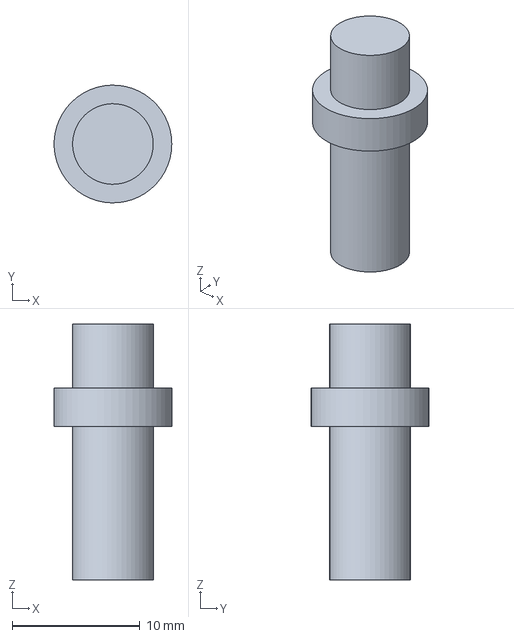
[picture p56: CAD file, 2026-09-26]
hardware/enclosures/v9/ref/gateway_sma_jack.step
9.19 x 9.20 x 20.0 mm
