Fitzer34/bor-systems/hardware/enclosures/v9/hanger_lid_drawing.dxf

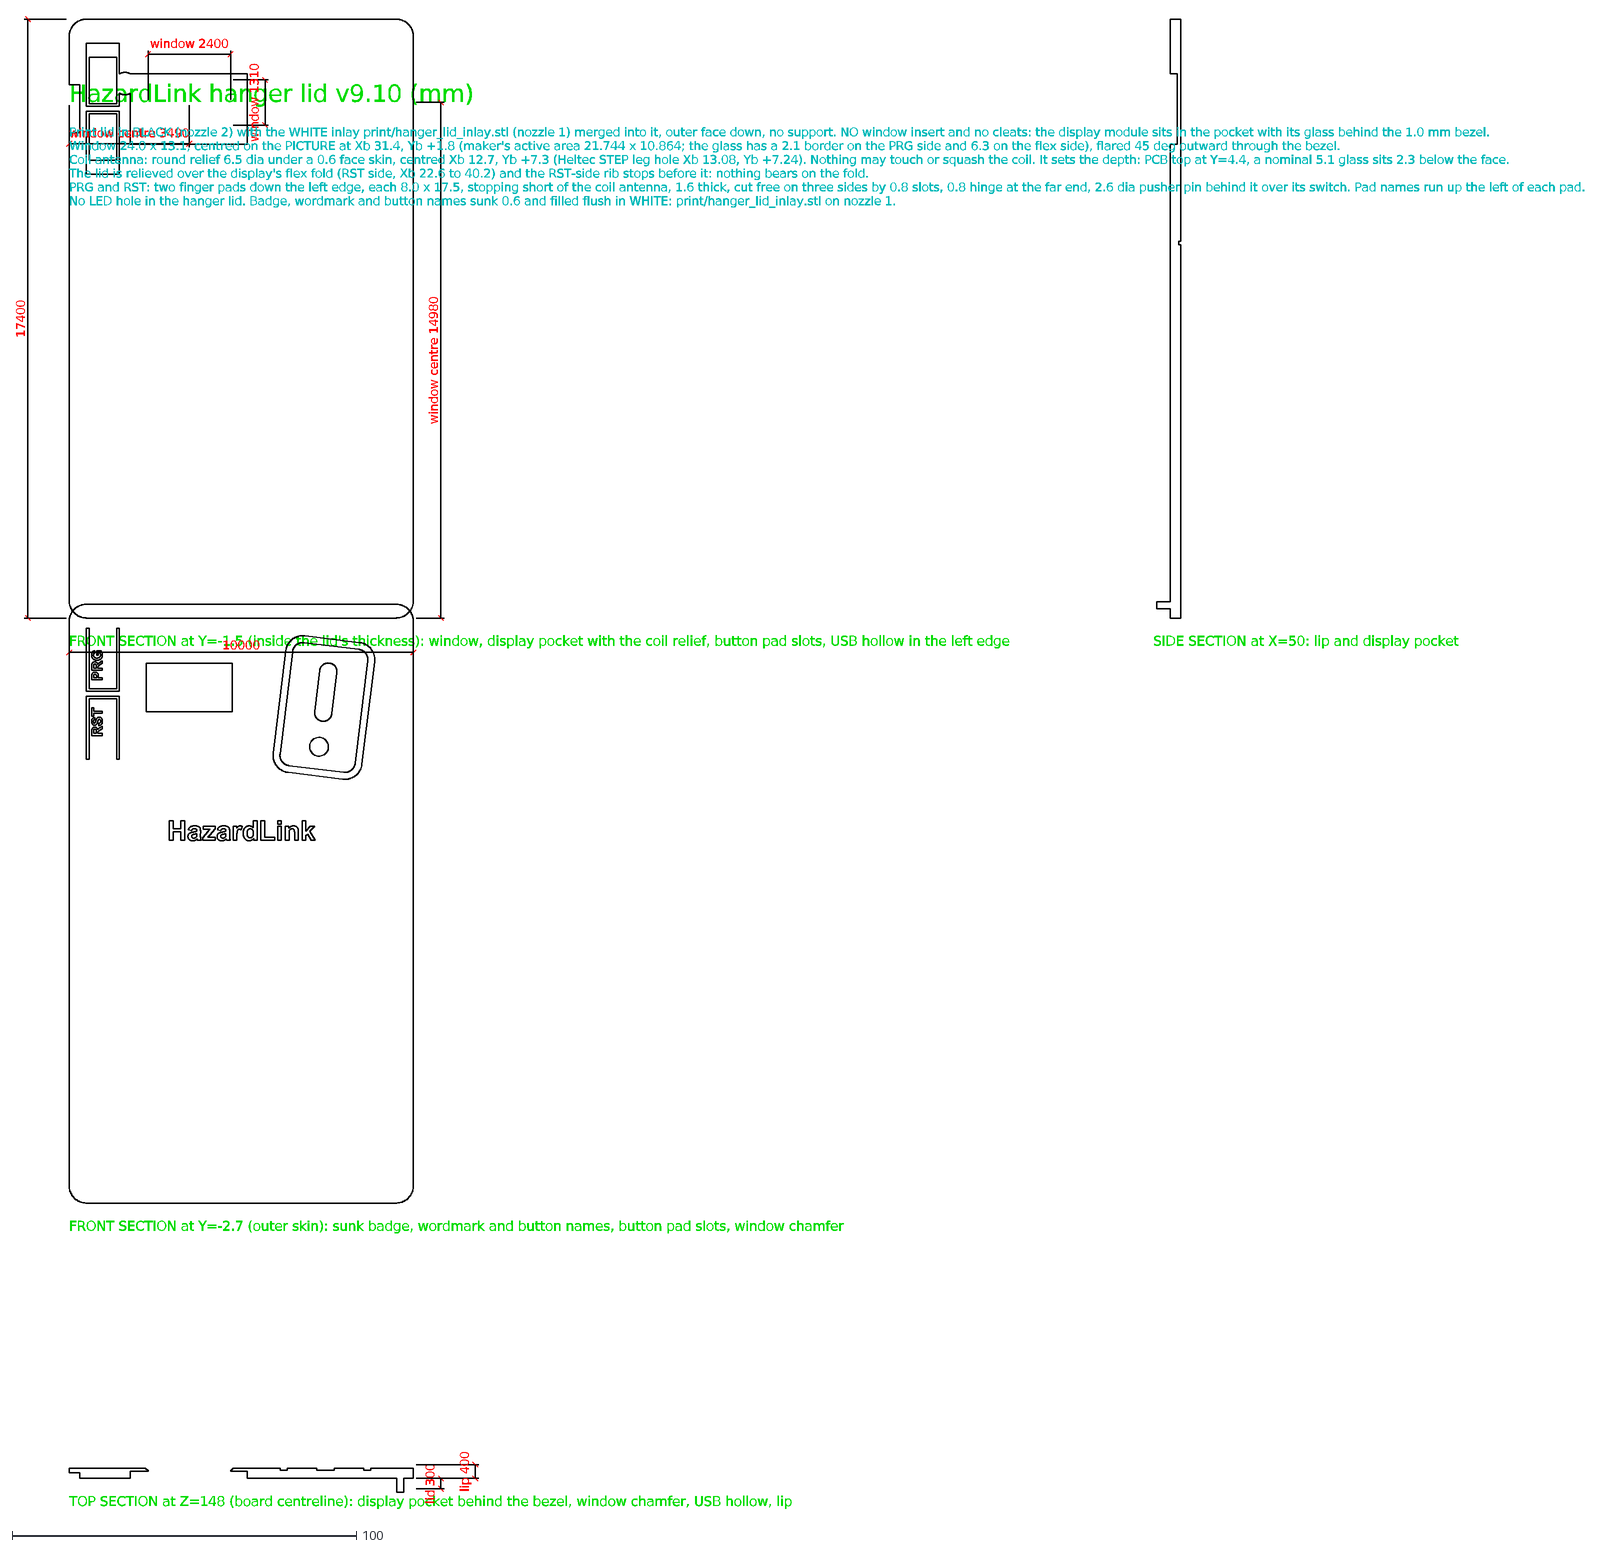
[picture p57: CAD file, 2026-09-26]
hardware/enclosures/v9/hanger_lid_drawing.dxf
HazardLink hanger lid v9.10 (mm)
FRONT SECTION at Y=-1.5 (inside the lid's thickness): window, display pocket with the coil relief, button pad slots, USB hollow in the left edge
10000
17400
window 2400
window 1310
window centre 3490
window centre 14980
FRONT SECTION at Y=-2.7 (outer skin): sunk badge, wordmark and button names, button pad slots, window chamfer
TOP SECTION at Z=148 (board centreline): display pocket behind the bezel, window chamfer, USB hollow, lip
lid 300
lip 400
SIDE SECTION at X=50: lip and display pocket
Print lid in BLACK (nozzle 2) with the WHITE inlay print/hanger_lid_inlay.stl (nozzle 1) merged into it, outer face down, no support. NO window insert and no cl
Window 24.0 x 13.1, centred on the PICTURE at Xb 31.4, Yb +1.8 (maker's active area 21.744 x 10.864; the glass has a 2.1 border on the PRG side and 6.3 on the f
Coil antenna: round relief 6.5 dia under a 0.6 face skin, centred Xb 12.7, Yb +7.3 (Heltec STEP leg hole Xb 13.08, Yb +7.24). Nothing may touch or squash the co
The lid is relieved over the display's flex fold (RST side, Xb 22.6 to 40.2) and the RST-side rib stops before it: nothing bears on the fold.
PRG and RST: two finger pads down the left edge, each 8.0 x 17.5, stopping short of the coil antenna, 1.6 thick, cut free on three sides by 0.8 slots, 0.8 hinge
No LED hole in the hanger lid. Badge, wordmark and button names sunk 0.6 and filled flush in WHITE: print/hanger_lid_inlay.stl on nozzle 1.
