Fitzer34/bor-systems/hardware/enclosures/v9/stages/S5_magnet.step

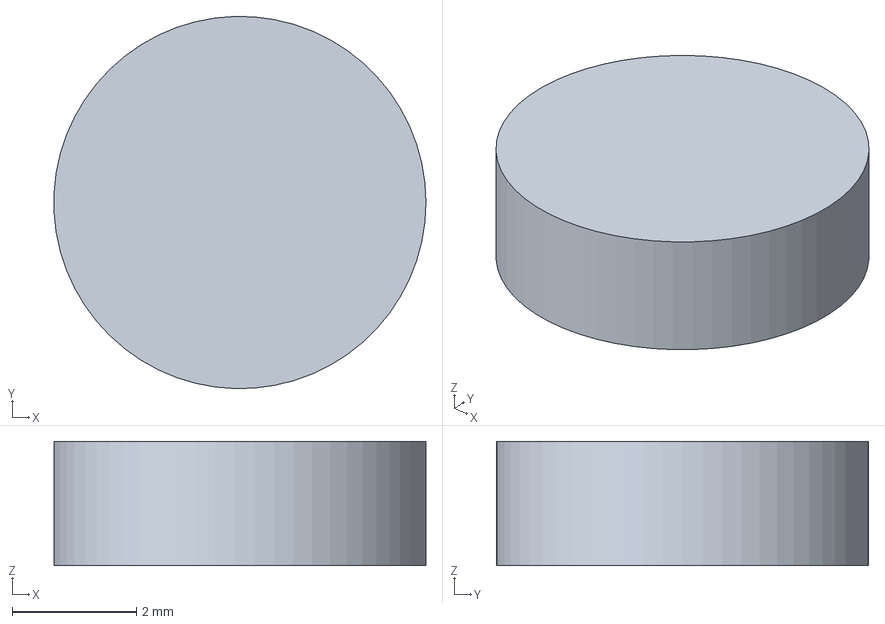
[picture p58: CAD file, 2026-09-20]
hardware/enclosures/v9/stages/S5_magnet.step
6.00 x 6.00 x 2.00 mm
