Fitzer34/bor-systems/hardware/enclosures/v9/ref/hanger_usb_plug.step

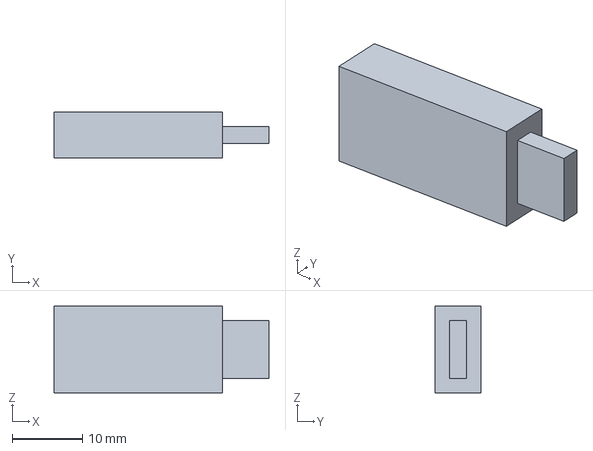
[picture p59: CAD file, 2026-09-26]
hardware/enclosures/v9/ref/hanger_usb_plug.step
30.7 x 6.50 x 12.4 mm
