Fitzer34/bor-systems/hardware/enclosures/v9/stages/S7_body.step

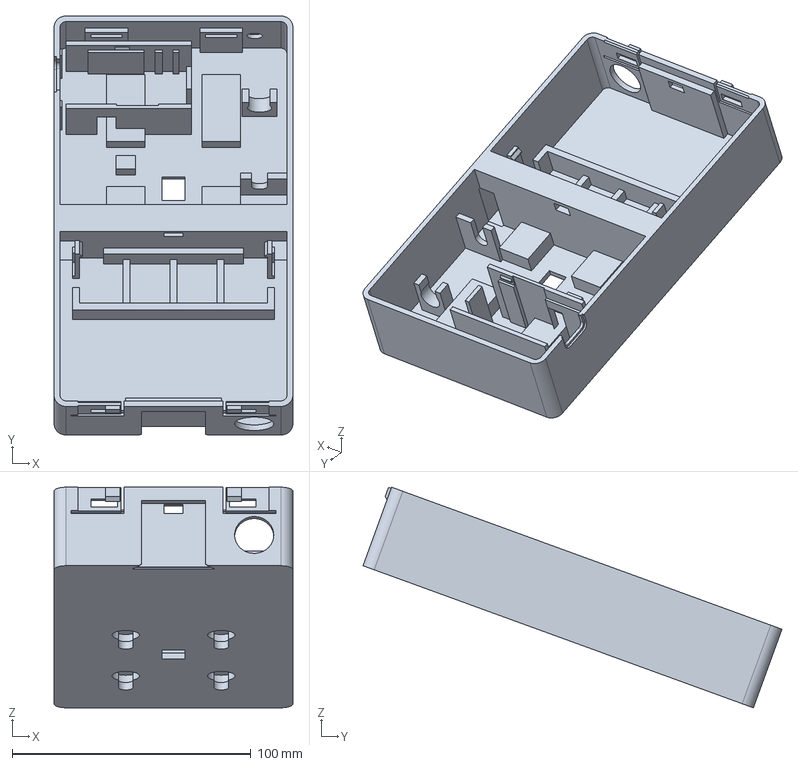
[picture p60: CAD file, 2026-09-20]
hardware/enclosures/v9/stages/S7_body.step
100.0 x 175.5 x 92.4 mm
