Fitzer34/bor-systems/hardware/enclosures/v9/ref/hanger_hall_carrier.step

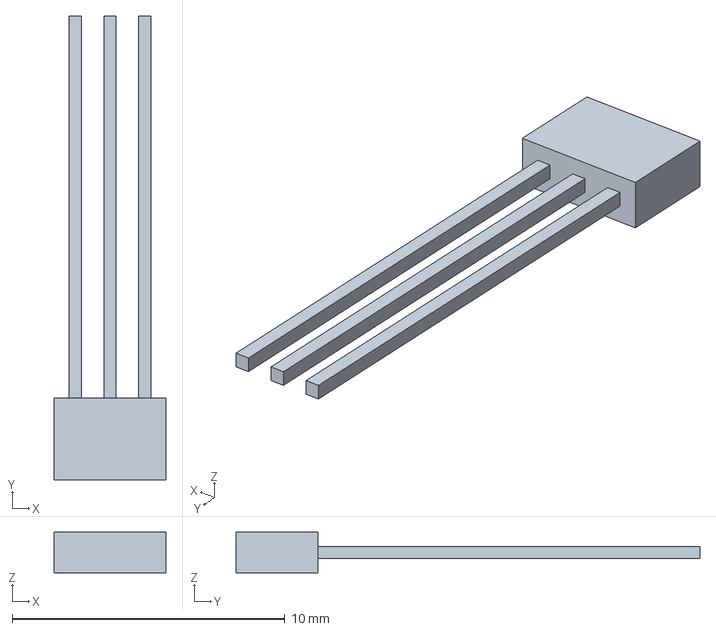
[picture p61: CAD file, 2026-09-26]
hardware/enclosures/v9/ref/hanger_hall_carrier.step
4.10 x 17.0 x 1.50 mm
