Fitzer34/bor-systems/hardware/enclosures/v9/gateway_section.dxf

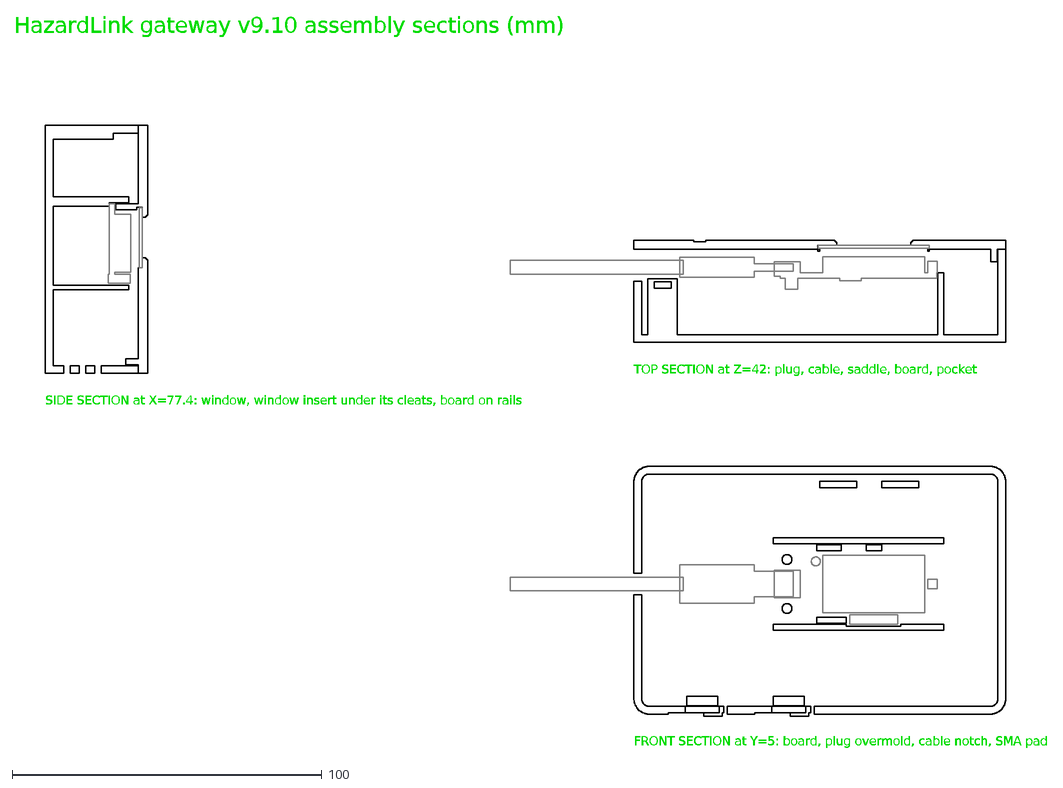
[picture p62: CAD file, 2026-09-26]
hardware/enclosures/v9/gateway_section.dxf
HazardLink gateway v9.10 assembly sections (mm)
SIDE SECTION at X=77.4: window, window insert under its cleats, board on rails
TOP SECTION at Z=42: plug, cable, saddle, board, pocket
FRONT SECTION at Y=5: board, plug overmold, cable notch, SMA pad
