Fitzer34/bor-systems/hardware/enclosures/v9/ref/gateway_window_insert.step

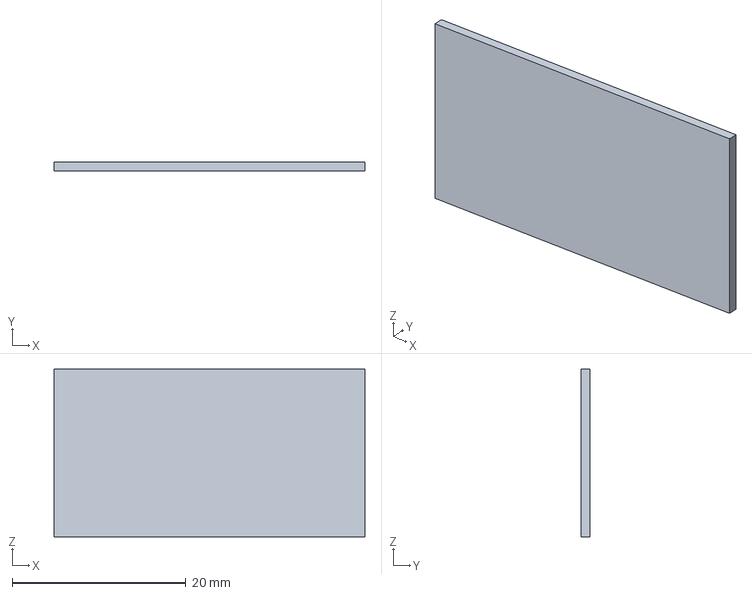
[picture p63: CAD file, 2026-09-26]
hardware/enclosures/v9/ref/gateway_window_insert.step
35.8 x 1.00 x 19.3 mm
