Fitzer34/bor-systems/hardware/enclosures/v9/stages/S7_logo.step

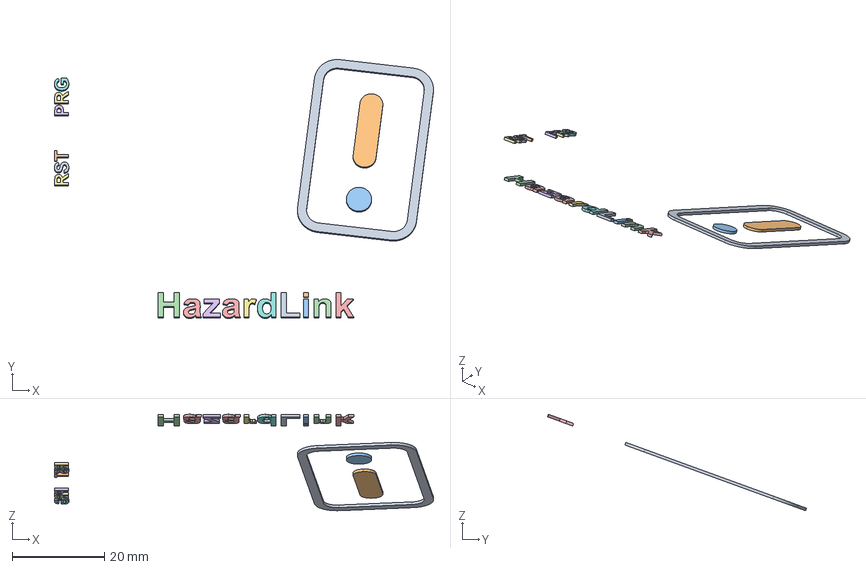
[picture p64: CAD file, 2026-09-20]
hardware/enclosures/v9/stages/S7_logo.step
82.2 x 56.2 x 20.9 mm
