Fitzer34/bor-systems/hardware/enclosures/v9/stages/S6_logo.step

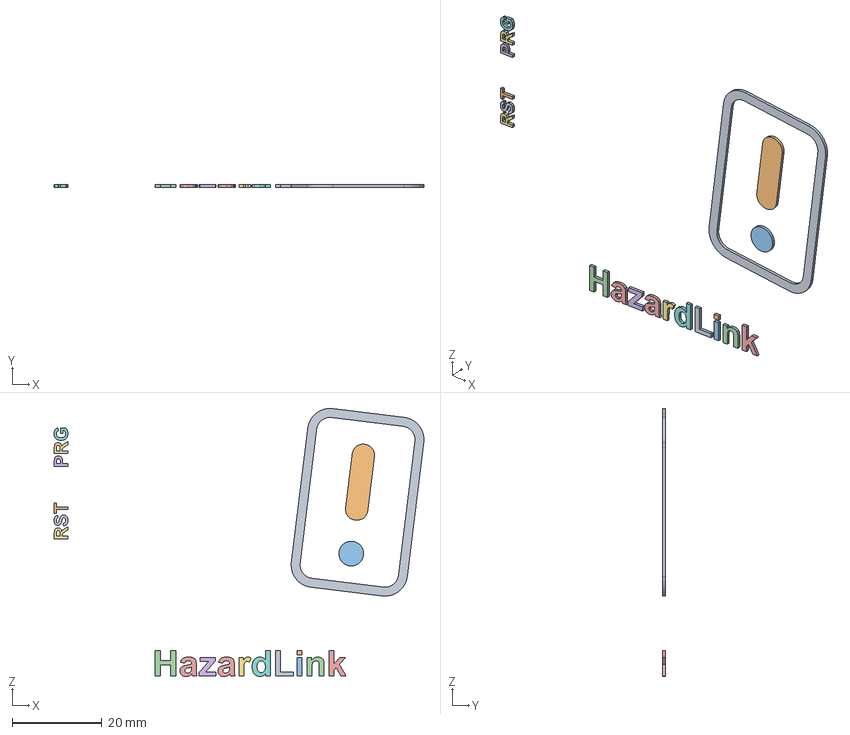
[picture p65: CAD file, 2026-09-20]
hardware/enclosures/v9/stages/S6_logo.step
82.2 x 0.6 x 59.6 mm
