Fitzer34/bor-systems/hardware/enclosures/v9/stages/S7_lid.step

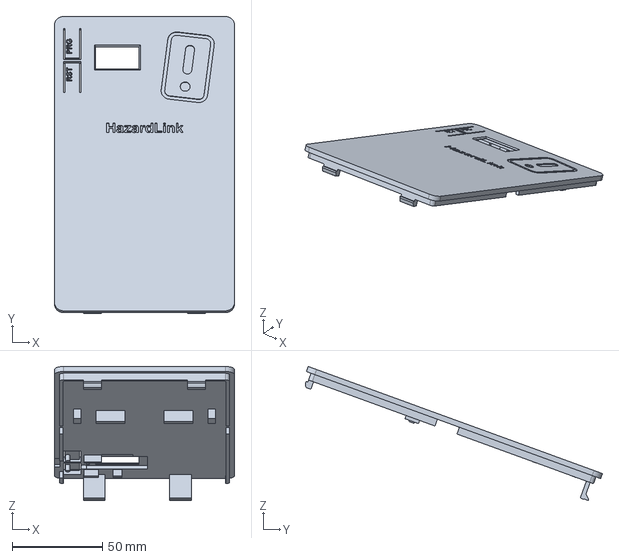
[picture p66: CAD file, 2026-09-20]
hardware/enclosures/v9/stages/S7_lid.step
100.0 x 165.0 x 74.5 mm
