Fitzer34/bor-systems/hardware/enclosures/v9/stages/S7_button.step

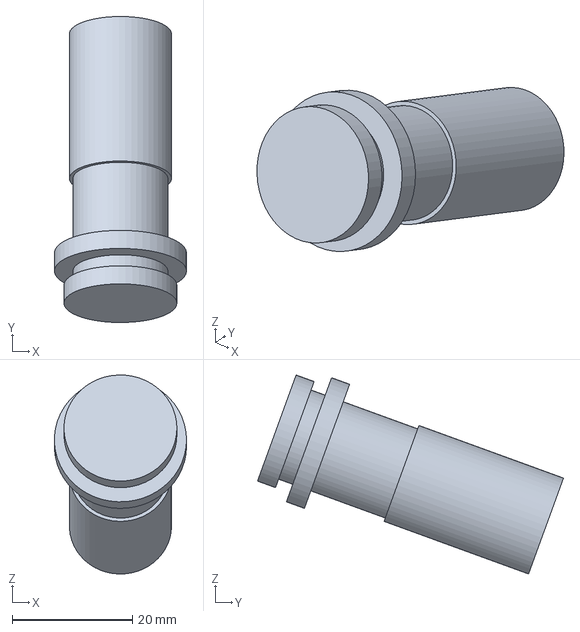
[picture p67: CAD file, 2026-09-20]
hardware/enclosures/v9/stages/S7_button.step
22.0 x 50.9 x 33.1 mm
