Fitzer34/bor-systems/hardware/enclosures/v9/stages/S0_sensor.step

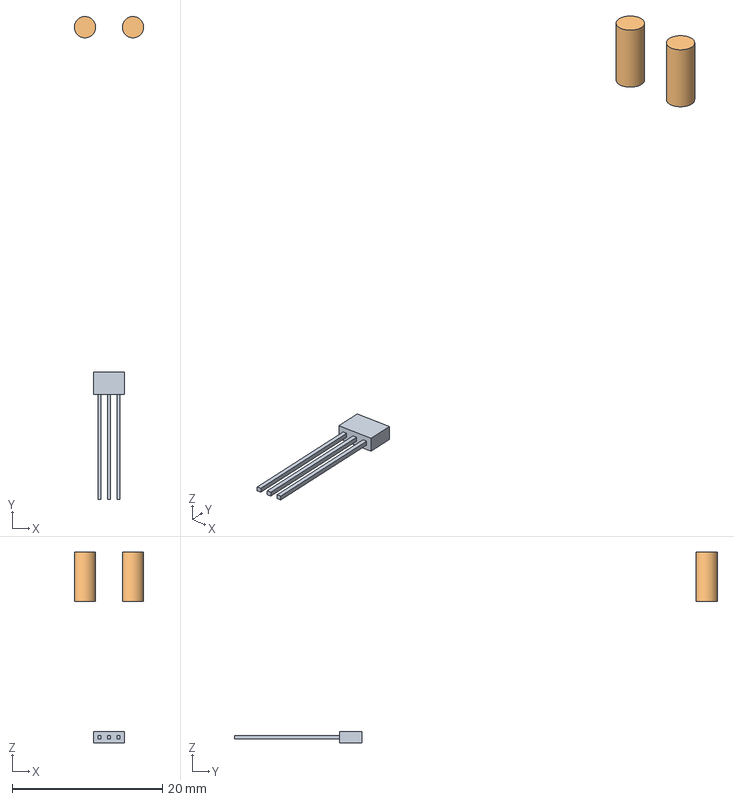
[picture p68: CAD file, 2026-09-20]
hardware/enclosures/v9/stages/S0_sensor.step
9.25 x 64.4 x 25.5 mm
