Fitzer34/bor-systems/hardware/enclosures/v9/closeups/print_layout.png

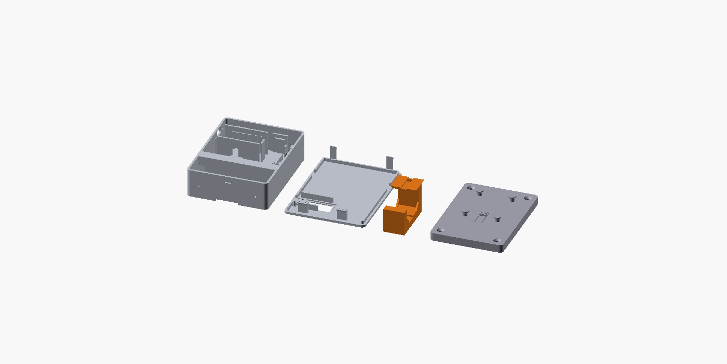
hardware/enclosures/v9/closeups/print_layout.png
