Fitzer34/bor-systems/hardware/enclosures/v9/gateway_assembled_front.png

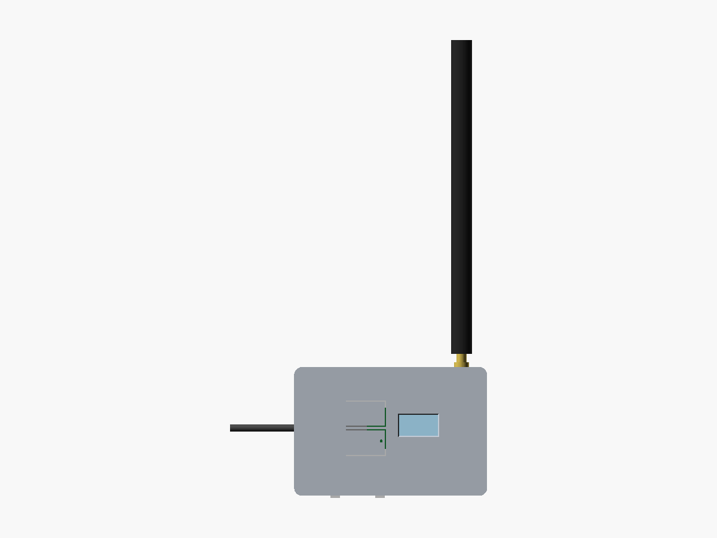
hardware/enclosures/v9/gateway_assembled_front.png
