Fitzer34/bor-systems/hardware/enclosures/v9/hanger_assembled_side.png

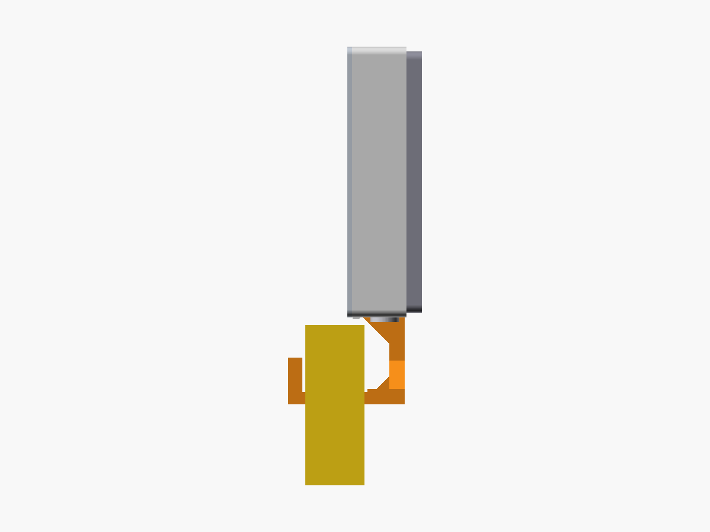
hardware/enclosures/v9/hanger_assembled_side.png
