Fitzer34/bor-systems/hardware/enclosures/v9/hazardlink_enclosures.py

#!/usr/bin/env python
"""HazardLink v9.10 enclosures, FINAL (Designer A base, hanger reworked to Owen's bottom-hung concept).

Two printed enclosures built around the Heltec WiFi LoRa 32 V3:
  HANGER  : battery wall hanger = body + lid + backplate + slide-in hanging BAR under the bottom edge
            (the sign hangs below the unit; the bar carries a saddle, and a bare Hall sensor sits in a nest under it,
            held by two filament pins). No screws between the parts; wall screws are the only screws.
            A cleaning-mode push button (Owen's Gebildet 16 mm) is FITTED through the bottom wall, pointing down, above
            the hook and out of sight from the front. The box grew DOWNWARD by H_BASEMENT (44 mm, so 174 tall; v9.9 was 171
            and the box with no button is 130) to give the button an empty bay under the battery; every feature keeps its
            place counted from the TOP of the box. PARAMS BTN16_ON=False builds the old 130 mm box with no button. The hanger
            firmware reserves the button's pin (TEST_BUTTON_PIN = 3) but does not act on a press yet, so the README proves
            the wiring with a meter.
            v9.10: every size that matters now comes from the MAKER'S OWN drawing, STEP file or listing, and nobody is asked
            to measure anything. The screen window is centred on the PICTURE (Xb 31.4, Yb +1.8) and is 24.0 x 13.1, flared
            45 degrees; the coil antenna has its own round relief and sets how far back the board sits (PCB top Y 4.4); the
            PRG and RST pads are 8.0 x 17.5 and stop short of the coil; nothing bears on the display's flex fold; the hook
            bar is 88 wide with a 42 mm seat, 46 below the body, reach 86; the battery holder's pins follow the MPD drawing.
            The README section WHERE THE SIZES COME FROM lists the source of each size, the few that no maker publishes
            (coil height, sign hand-hole sizes), how those were derived and what margin was added. The proof on the real
            parts is a small test print, print/hanger_window_gauge.stl.
            Colours (Owen's choice): nozzle 1 = white PLA, nozzle 2 = black PLA. Body, lid, backplate and test pieces are
            black; the hook bar is white; the lid lettering is the white inlay print/hanger_lid_inlay.stl.
  GATEWAY : mains wall box      = body + lid (SMA bulkhead on top, USB-C entry with strain relief). Same box as v9.9; its
            window follows the same picture centre and size as the hanger's.

Run with the CadQuery venv:
  cadenv/bin/python hazardlink_enclosures.py [out_dir] [--quick] [--no-autocad] [--check]
  --quick skips the PNG previews, --no-autocad skips the SAT/DXF conversion, --check prints
  part-to-part and part-to-reference intersection volumes instead of exporting.

Per part: <part>.step, <part>.stl (fine), <part>.png, <part>_drawing.dxf (section views with dimensions).
Per unit: <unit>_assembly.step (named, coloured, with reference solids), <unit>_exploded.png,
<unit>_assembled.png, <unit>_section.dxf (assembly stack-up section through the board).
print/ holds the same parts already turned into their print orientation (PRINT_ORIENT), the two lid inlays for the
white lettering, the body coupon, the window gauge and ORIENTATION.txt. The slicer settings live in PRINT.md.
Reference solids (board, cell, holder, Hall sensor and its two pins, magnet, sign handle, antenna, plug) go to ref/.
The design rule checks run BEFORE anything is exported, so a bad parameter cannot overwrite good files.
AutoCAD for Mac deliverables (.sat + 3DSOLID .dxf) come from to_autocad.py, which this script tries to run at
the end into <out_dir>/autocad unless --no-autocad is given. The AutoCAD and Fusion views refresh with no clicking:
see ../autoload/README.md.

FRAME (both units): X to the viewer's right when facing the unit, Z up, Y is depth measured from
the body's front face INTO the wall (right-handed). Body occupies Y 0..D, lid sits at Y -LID_T..0,
backplate at Y D..D+BP_T, the bar's lip at Y < -LID_T. The body rim is Y=0 and the lid's outer face is Y=-LID_T.

Board frame -> world: Xb (along the board from the USB-end corner points) -> +X,
Zb (up from the PCB top, toward the OLED) -> -Y (toward the lid), Yb (+ toward PRG/J3) -> +Z.
So the OLED faces the lid, the USB-C is at the left wall, PRG is above the board centreline and
RST below it.

Every dimension lives in PARAMS with a tag:
  maker     : from the maker's own drawing, STEP file or listing (v9.10: display panel, coil position, flex fold, button,
              battery holder). Where no maker publishes a figure the comment says so, and says how it was derived
  datasheet : from a vendor drawing or STEP (Heltec, Murata, TI, USB-IF, TE)
  research  : worked out in the research pass (field tables, community practice)
  v7        : kept from the v7 OpenSCAD sketch (design intent)
  assumed   : a design choice made here (a clearance, a wall, a position), proved by the design rule checks and the test prints
  Owen's caliper / ruler / side photo, packing slip : an EARLIER reading off the delivered parts. It is kept only as a
              cross-check beside the maker's figure, or where no maker figure exists. Nothing is waiting to be measured
  review    : changed after the independent review of v9.7
No em-dashes anywhere in this file, on purpose.
"""
import os, sys, math, subprocess, glob, time
import cadquery as cq

# --------------------------------------------------------------------------------------
# PARAMS
# --------------------------------------------------------------------------------------
P = dict(
    # ---- Heltec WiFi LoRa 32 V3 -------------------------------------------------------
    BRD_L=51.7,             # datasheet (STEP outline, USB corners to antenna tip)
    BRD_W=25.4,             # datasheet
    BRD_T=1.8,              # datasheet 1.6 + 0.2 allowance
    BRD_CLR=0.3,            # assumed: pocket clearance per side (slip fit)
    USB_NOSE=0.65,          # datasheet: USB-C nose proud of the corner points
    USB_SETBACK=1.0,        # assumed: corner points to the wall inner face (nose 0.35 inside); gateway
    H_USB_SETBACK=3.2,      # not read by the model (the hanger cradle uses USB_SETBACK); kept for reference
    H_BRD_X0=3.5,           # v9.4: board back against the left wall (USB nose 0.35 inside it) so a cable plugs in with the LID ON.
                            # On this board the USB-C port sits between the two buttons at the very end, so port-at-the-edge,
                            # wide pads and a centred display cannot all be had: the display sits left of centre instead.
    H_PAD_V=(5.8, 17.5, 2.6, 0.5),   # assumed: hanger pads run vertically above and below the port: pad left edge x, pad height, pin diameter, pin x offset
    USB_LID_SKIN=1.4,       # review: seven layers left over the plug's overmold where the opening runs into the lid edge (the plug sits 1 mm deeper since v9.7, so 0.75 was needlessly fragile)
    # v9.3 buttons: each is a flap cut into the lid (U-slot through, thin hinge at the root) with a pin over the switch
    BTN_PAD=(24.0, 15.0, 1.6, 0.8, 4.0, 0.8),   # assumed: pad length (X), height (Z), pad thickness, hinge thickness, hinge length, slot width
    BTN_PAD_X1=10.3,        # pad edge nearest the display, from the board's USB-end edge: it stops short of the coil antenna's worst-case edge (Xb 10.55, see design_checks), so a pad is never over the coil
    BTN_PAD_GAP=1.5,        # assumed: each pad starts this far from the board centreline
    BTN_PIN_D=3.2, BTN_PIN_GAP=0.3, BTN_TRAVEL=0.3,   # assumed: pin diameter, rest gap over the switch, switch travel
    BTN_LABEL=(4.2, 2.4),   # pad names are 4.2 tall and run up the LEFT side of each pad (centre 2.4 from the pad's left edge), clear of where the status lights sit under the RST pad
    LED_HOLE_D=1.8,         # assumed: light hole over the two status LEDs (it falls inside the RST pad)
    H_LED_HOLE=False,       # Owen: no hole in the hanger's face (it is cleaned around wet floors and he does not want it). The board's two status
                            # lights are hidden with the lid on; the display shows what the unit is doing. The gateway keeps its light hole.
    G_LED_HOLE=True,
    # v9.3 face marks: sunk MARK_DEPTH (0.6 = three layers, so white stays white over black) into the face as narrow strokes (prints cleanly on the bed), and filled flush in
    # WHITE from nozzle 1 (the lid itself is BLACK from nozzle 2) using print/<lid>_inlay.stl. Printed in one colour they are simply sunk lines
    MARK_DEPTH=0.6, LOGO_BADGE=(26.0, 40.0, 5.0, 2.0, -7.0),   # assumed: badge width, height, corner radius, stroke, tilt in degrees
    LOGO_BANG=(5.0, 17.0, 4.5, 5.5, -11.5),   # assumed: exclamation bar width, height, bar centre z, dot diameter, dot centre z (from the badge centre)
    H_LOGO=(74.0, 100.0, 1.0), H_WORDMARK=(50.0, 64.0, 8.0, "center"),   # assumed: badge to the right of the display, wordmark centred below the row
    G_LOGO=(17.0, 58.0, 0.78), G_WORDMARK=(62.0, 66.0, 6.5, "left"),     # assumed: gateway
    OLED_H_MAX=5.4,         # maker: Heltec's drawing and STEP put the display top 5.0 above the PCB; the panel maker's worst-case glass top is 5.25. 5.4 + OLED_GAP keeps all lid material 5.6 clear of it.
                            # The COIL is taller than the display, so in practice the coil sets how far back the board sits (see hanger_geom).
    COIL=(12.7, 7.3, 2.9, 6.0),   # WiFi coil (spring) antenna standing on the board: its leg hole is at Xb 13.08, Yb +7.24 in Heltec's detailed STEP (exact); body axis Xb 12.6 +/-0.6, Yb +7.3 +/-0.4 and
                            # dia 2.9 scaled from Heltec's photo; height 6.0 +/-0.5 (Heltec's 5.0 display top + about 1 mm, agrees with Owen's side photo). Heltec publishes no coil height.
    COIL_TOL=(0.6, 0.5), COIL_SKIN=0.6, COIL_AIR=0.3, COIL_KEEPOUT_D=6.5,   # position and height tolerance; lid skin left over the coil (3 layers); air left over a worst-case coil; clear diameter round it (Heltec: a squashed or touched spring antenna causes resets)
    BEZEL_T=1.0, OLED_GAP=0.2,   # front skin left around the window; clearance over the tallest display
    OLED_POCKET=(14.3, 48.2, -10.4, 10.2),   # maker: lid pocket over the display carrier in board coordinates (Xb0, Xb1, Yb0, Yb1): carrier Xb 14.88..47.88, Yb +/-9.3, and the glass ledge overhangs to Yb -10.0 on the RST (flex) side
    OLED_X0=14.9, OLED_X1=47.9, OLED_HALF_W=9.3, OLED_H=5.1,    # maker: Heltec STEP carrier 33.0 x 18.6 at Xb 14.88..47.88, centred on the board; glass top nominal 5.1
    OLED_ACT_CX=31.4, OLED_ACT_CY=1.8,       # maker: centre of the PICTURE (active area). The glass has a 2.1 mm border on the PRG side and 6.3 on the RST (flex) side, so the picture sits 1.8 toward PRG
    OLED_AA=(21.744, 10.864),                # maker: active area (Heltec QG-2864KSWEG01 / Univision UG-2864HSWEG01 drawing)
    WIN_W=24.0, WIN_H=13.1,                  # maker: the panel's view area is 23.744 x 12.864 (1 mm round the picture); drawn 24.0 x 13.1 because printed holes close up a little. Flared 45 deg outward through the bezel.
    INSERT_W=36.0, INSERT_H=19.5, INSERT_T=1.0, INSERT_POCKET=1.3,   # assumed 1 mm acrylic or PETG pane (GATEWAY lid only; the hanger lid is flush and takes no insert)
    INSERT_CLEAT=0.6,                        # assumed: retaining cleat overhang into the pocket (gateway lid only)
    PRG=(3.4, 7.9), RST=(3.4, -7.9), BTN_H=2.0,   # datasheet (STEP)
    LED=(8.1, -8.0),                              # datasheet (STEP, two 0603 LEDs)
    IPEX=(50.4, 0.0), IPEX_H=1.26, UFL_PLUG_H=2.5,   # datasheet socket / assumed plug height
    USB_SHELL_W=8.94, USB_SHELL_H=3.5, USB_OPEN_CY=1.7,   # datasheet
    USB_SLOT_W=14.0, USB_SLOT_H=8.0,   # USB-IF allows a plug overmold up to 12.35 x 6.5 (the usb_plug reference solid); Owen's own white braided lead read about 12.2 to 12.6 wide earlier (metal tip 8.3); 14.0 leaves 0.7 a side
    BAT_SOCK=(2.8, 6.9, 2.3, 3.6),     # datasheet: Xb0, Xb1, half width, height below the PCB
    BAT_CHAN=(7.0, 20.0, 4.0, 5.0),    # research: plug + cable channel Xb0, Xb1, half W, depth
    HDR_ROW_Y=11.43, HDR_PITCH=2.54, HDR_X1=3.43,   # datasheet: pin 1 X, row Y, pitch
    WIRE_PINS_J3=(1, 2, 3, 14, 17),    # datasheet pinmap: GND, 3V3, 3V3, GPIO3, GPIO6 (wire pads)
    RAIL_W=1.1,                        # assumed: ledge under each long edge (board rests on it)
    RAIL_LIP_ABOVE=4.5,                # assumed: pocket side wall height above the PCB top
    POCKET_WALL_T=2.0,                 # assumed
    LID_RIB_W=1.9, LID_RIB_CLR=0.3,    # assumed: lid rib on the header pad strip
    LEAD_NOTCH=(14.5, 22.5),           # Xb span of the lead notch in the J2 pocket wall, moved toward the USB end so the wires stay off the display's flex fold
    FLEX_FOLD=(22.6, 40.2),            # maker: the display's flex tail folds over the RST-side (J2) board edge between Xb 23.6 and 39.2 (Heltec STEP and photos); 1 mm added each end. No rib, ledge or catch may bear there.
    WIFI_KEEPOUT=15.0,                 # research: last 10 mm of board + 5 beyond, no metal

    # ---- FDM rules --------------------------------------------------------------------
    WALL=2.5,                # research: 2.4 min for an electronics box
    LID_T=3.0,               # research: 3.0 for a handled face
    CORNER_R=5.0,            # v7
    TONGUE_T=2.0, TONGUE_H=4.0, TONGUE_CLR=0.25,   # research: lip 2 x 4, 0.25 per side
    # ---- snap-fit lids (v9: no screws anywhere in the assembly) ------------------------
    # two rigid hinge tabs on the lid's top edge hook into pockets in a rib along the top wall; two rigid hooks on the
    # lid's bottom edge drop into windows in two spring arms cut into the body's bottom wall; a pull lip under each arm
    # tip releases it by hand (no release pins or pinholes since v9.2)
    # v9.2 latches: the SPRING is an arm cut into the body's bottom wall (it prints along its length, so bending runs
    # along the layers); the lid carries only a rigid hook. First PLA print: thin fingers standing on the lid snapped.
    ARM_L=21.0, ARM_W=10.5, ARM_T=2.0, ARM_SLOT=1.2,      # assumed: arm length (X), width from the rim (Y), thickness (outer face relieved), slot width
    ARM_TAB=(0.6, 0.8),      # assumed: breakaway tab (Y, Z) across the end slot so the arm's first layers bridge; snaps on first use
    ARM_WIN=(11.0, 5.0, 8.6),   # assumed: window through the arm near its free end (X width, Y front edge, Y back edge)
    ARM_WIN_FROM_TIP=7.0,    # assumed: window centre to the arm tip
    ARM_LIP=(6.0, 1.2),      # assumed: pull lip under the arm tip (X length, proud of the bottom face)
    HOOK_W=10.0, HOOK_T=3.0, HOOK_L=8.4, HOOK_BARB=1.0, HOOK_CATCH_Y=5.2, HOOK_FLAT=1.0, HOOK_GUSSET=4.0,   # assumed: rigid lid hook (barb catches the window's front edge)
    TAB_W=12.0, TAB_L=14.0, TAB_NOSE=2.5, TAB_NOSE_L=3.0, TAB_CLR=0.25, TAB_POCKET_UP=0.6,   # assumed: hinge tab (contiguous with the tongue, 2.25 thick) with a 45 deg hook face; nose pocket reaches 0.6 into the top wall
    TAB_RIB_Y0=8.0, TAB_RIB_H=2.0, TAB_RIB_SIDE=3.0,   # assumed: stiffening rib along the top wall from Y=8 to the back wall; the nose pocket is cut through it (bridge on 2.5 mm cheeks)
    H_ARMS=((7.0, 1), (93.0, -1)), H_TAB_XS=(22.0, 70.0),   # assumed: (root x, direction) of each wall arm, clear of the bar channel strip (x 30..70)
    G_ARMS=((8.0, 1), (36.0, 1)), G_TAB_XS=(66.0, 86.0),    # assumed: gateway arms, left of the intake vents
    SNAP_STRAIN_MAX=1.5,     # research: repeated-use design strain, percent; 1.5 covers PLA (the first spool) as well as PETG (2.0)
    # the next four belong to the v9.2 face (RST pinhole, sealed LED window, PRG living-hinge tab). Nothing reads them since
    # v9.3: both buttons are pads (BTN_PAD, H_PAD_V) and the LED shows through an open hole (LED_HOLE_D)
    PINHOLE_D=2.0,           # unused since v9.3
    LED_WIN_D=3.0, LED_SKIN=0.5,      # unused since v9.3
    PRG_TAB=(6.0, 10.0, 1.0, 0.8, 0.4),   # unused since v9.3
    PUSHER_D=2.5,            # unused since v9.3
    PEG_STEM_D=5.5, PEG_STEM_L=3.5, PEG_HEAD_D=10.0, PEG_HEAD_L=3.5, PEG_CHAMFER=1.0,  # assumed (PEG_CHAMFER is not read: the head has a 45 deg cone under it instead)
    PEG_DROP=14.0,           # v7: engagement slide
    PEG_SLOT_CLR=0.35, PEG_HEAD_CLR=0.75, PEG_POCKET_BACK=2.5,   # assumed clearances / roof
    KEY_HEAD_D=10.0, KEY_SLOT_W=5.0, KEY_SLOT_L=10.0,   # research: No.8 pan head keyhole (slot 10 here)
    KNOCKOUT_SKIN=0.8,       # assumed: membrane left in knock-outs

    # ---- Hanger -----------------------------------------------------------------------
    H_W=100.0, H_H=130.0, H_D=35.0,   # v7. These are the values BEFORE the basement: with the button fitted _apply_basement() adds H_BASEMENT (44) to H_H
                                      # and to every hanger height below (board centre, holder, bulkhead, pegs, catch, antenna, backplate, marks), so the box is 174 tall
    H_BRD_ZC=104.0,          # assumed: board centreline height (window as high as the bosses allow)
    H_PCB_TOP_Y=None,        # not read: hanger_geom derives the PCB top (Y 4.4). The display sits in a pocket in the lid behind a 1 mm bezel, and the taller coil antenna beside it sets the depth
    HOLDER_L=77.7, HOLDER_W=20.9, HOLDER_H=21.31, HOLDER_CLR=0.5,   # maker: BeiLaMoo BH18650-PC2 listing, identical to the MPD BH-18650-PC drawing it is a copy of (maker tolerance +/-0.5, so keep 0.5 clearance a side)
    HOLDER_STANDOFF=5.0,     # kept at 5.0: the maker's pin is 3.30 long (HOLDER_PIN) and the allowance is 4.8 (HOLDER_PIN_ENV), so 5.0 leaves room for the pin and the wire soldered to its side
    HOLDER_PIN=(2.40, 3.30, 1.52),   # maker (MPD BH-18650-PC drawing): flat tab on the centreline 2.40 in from each end, 3.30 below the base, 1.52 wide x 0.38 thick
    HOLDER_PIN_ENV=4.8,      # clearance the standoff must give: BeiLaMoo publish no pin drawing of their own and an earlier photo of Owen's holder read about 4.3, so allow 4.3 + 0.5 (this also covers MPD's 3.30 + 0.5)
    HOLDER_X0=11.15, HOLDER_Z0=10.0,    # centred; 10.0 leaves a 4.1 mm passage under the holder for the sensor lead in the old box (BTN16_ON=False).
                                        # With the button fitted the holder sits H_BASEMENT higher and the whole bay under it (48 mm from the floor to the shelf) is open
    HOLDER_RIB_T=3.0, HOLDER_RIB_H=12.0, HOLDER_LEAD_GAP=8.0,   # assumed
    CELL_D=18.5, CELL_L=65.2,         # packing slip: Murata US18650VTC6 (18650), datasheet maximum size
    BULK_Z=(34.0, 46.0),              # assumed: stiffening bulkhead between bay and board
    # ---- hanging bar (Owen: sign hangs from the bottom edge, nothing on the face) -------
    BAR_W=88.0,              # no maker publishes a hand-hole size. Scaled from the makers' own product photos the narrowest common one is Rubbermaid FG6112xx at about 105 mm (low bound 92),
                             # Carlisle about 111, the generic UK/IE 620 x 300 moulding about 120. 88 enters every one of them. A wider bar (108) for the generic moulding alone is a parameter change.
    WEB_W=26.0,              # design choice: the web and dovetail stay narrow, so the part is a T
    BAR_SPREAD=18.0,         # assumed: triangular spreaders each side of the web that carry the wide bar
    SIGN_HOLE_CLR=17.0, SIGN_HOLE_H=47.0, SIGN_T=38.0,   # reference sign = Rubbermaid FG6112xx: hole about 105 x 47 (photo scaled); 38.0 closed depth is Rubbermaid's published packaging depth (1.50 in), the thickest of the common signs
    BAR_T=10.0,              # assumed: bar thickness
    BAR_DROP=46.0,           # the sign stands 36 to 42 mm above the top of its hand hole (photo scaled across the common makes), so the bar hangs 46 below the body and the sign's top clears the box
    BAR_WEB_Y=(24.0, 34.0),  # assumed: the web that carries the bar down from the body, under the back of the body (nothing behind the back face, so the body can lift 14 mm past the backplate)
    # v9: the bar's plate is a dovetail that slides into a channel in the body's bottom wall FROM THE WALL SIDE;
    # the channel is closed at the front and the backplate covers its mouth, so with the body hung the bar cannot come out
    DT_MOUTH=27.0, DT_TOP=34.0, DT_H=3.5, DT_CLR=0.45, DT_ROOF=1.9, DT_STRIP_W=40.0, DT_Y0=6.0, DT_LEADIN=0.6,   # assumed: mouth width, top width (45 deg flanks: top - mouth = 2 x height), height, plate clearance per side (flanks print as 45 deg overhangs), roof, strip width, closed front end, mouth chamfer
    PLATE_Y=(6.6, 34.5),     # assumed: bar plate span along Y (flush with the web's back face, 1 mm inside the body's back face)
    HANDLE_H=42.0,           # sign height above the top of its hand hole (see BAR_DROP)
    BAR_REACH=86.0,          # wall face to the lip front: far enough out that a 38 mm thick folded sign hangs wholly in front of the hook's gusset and the button under the base
    BAR_LIP_T=9.0,           # v7 lip thickness
    BAR_LIP_H=20.0,          # assumed: lip rises this much above the bar top (forward of the lid, so no clash)
    BAR_SADDLE_Y=-11.0,      # saddle centre: the 42 mm seat runs from the lip back to Y=+10, in front of the gusset (which starts to drop at Y=6.6) and of the cleaning button (Y >= 11.9)
    BAR_SADDLE_W=42.0, BAR_SADDLE_D=2.0,  # seat width along Y = thickest folded sign (38) + 4; depth
    BAR_WIRE_Y=(6.5, 10.5),  # assumed: lead slot through the channel roof. It opens UNDER the battery holder (holder front face Y=6.2 at HOLDER_STANDOFF 5):
                             # the leads come up under the holder (into the bay under the battery since v9.9), bend forward, then rise in front of it.
                             # So they are fed up and folded forward BEFORE the holder is pressed in: a lead left standing is trapped behind the holder.
    BAR_WIRE_W=8.0,          # assumed
    WEB_BAND=(-19.0, -15.0), # assumed: the lead groove in the back of the web is open (wires lay in) except this band, which keeps them in.
                             # The band is closed, so the wire ends have to be THREADED under it (opening BAR_WIRE_W - 2 wide): no plug on them yet
    BULK_LEAD_SLOT=(46.0, 54.0, 2.0, 6.4),   # assumed: slot through the bulkhead right above the channel roof slot (x0, x1, y0, y1)
    BAR_GUSSET=8.0, BAR_GUSSET_W=2.0,    # short gussets where the web meets the bar. There are none at the lip root since v9.10: a folded sign fills the seat right up to the lip
    HALL_PKG=(4.1, 3.0, 1.5),         # read off the delivered part earlier (caliper photo): the lift sensor is a BARE flat 3-leg Hall sensor, TI DRV5032FA in the TO-92 style (LPG) package
                                      # (DigiKey DRV5032FALPG), body about 4.1 wide x 3.0 x 1.5 thick, no carrier board. OMNIPOLAR: either magnet pole works.
                                      # TI datasheet SLVSDC7H (Table 5-1, Figure 5-5): pin 1 VCC (1.65 to 5.5 V), pin 2 GND = the MIDDLE leg, pin 3 OUT (push-pull).
                                      # LEG ORDER CONFIRMED: Owen's sensors are marked 32FA, which that datasheet lists as the marking of DRV5032FALPG. Its
                                      # Figure 7-1 shows that the "top" of the TO-92 package is the marked, bevelled front face, and Figure 5-5 is the top view.
                                      # So with the MARKED face toward you and the legs pointing DOWN: LEFT = VCC (to 3V3), MIDDLE = GND, RIGHT = OUT (to GPIO6).
                                      # Never find a leg by putting 3V3 on it: 3V3 on the OUT leg is outside TI's absolute maximum ratings.
    HALL_LEG=(0.45, 1.27, 14.0),      # datasheet (TO-92 style): leg width, pitch, length. The wires are soldered to the legs and each joint sleeved, but the
                                      # first 3 mm of the legs behind the body stays bare, straight and unsleeved: the two retaining pins stand there
    HALL_NEST_CLR=(0.25, 0.3, 0.35),  # review: nest clearance each side, in front, above and below the package (0.35 so a sagging bridge cannot jam it, and every level of the cavity lands on a 0.2 mm layer)
    HALL_TUNNEL_W=8.6,                # v9: tunnel behind the nest for the legs and the three sleeved solder joints
    HALL_SLOT_H=3.0, HALL_SKIN=1.6, HALL_WIRE_H=4.4,   # review: values that put the roof, floors and trench on 0.2 mm layer boundaries with the bar printed upright
    HALL_PIN_PUSH_D=2.0,              # review: small hole under each pin through the bar's underside, to push a pin out and to drain
    HALL_FUNNEL_Y=4.5,                # review: the tunnel narrows to the nest over this length, so the package is steered in
    MAGNET_D=6.0, MAGNET_T=2.0,       # packing slip: XMP neodymium 6 x 2 mm N52
    TAG_WALL=1.2, TAG_CLR=1.0,        # research: tag wall and running clearance (assumed values)
    BP_W=90.0, BP_H=124.0, BP_T=10.0,   # v7 90 wide; 124 tall (z 3..127) so the plate covers the bar channel mouth; thickness 10 is a design choice.
                                        # With the button fitted H_BASEMENT is added: 168 tall (z 3..171)
    BP_SCREW_D=4.5, BP_SCREW_CSK_D=9.0, BP_SCREW_INSET=10.0,   # v7 / research No.8 csk
    PEG_XS=(30.0, 70.0), PEG_ZS=(55.0, 105.0),   # assumed peg positions (engaged); the head chamber BELOW each peg clears the holder's top rib
    # v9: spring catch on the backplate replaces the internal security screw; released from inside with the lid off
    CATCH_X=50.0, CATCH_Z0=44.0, CATCH_W=8.0, CATCH_T=1.8, CATCH_L=24.0, CATCH_GAP=3.0, CATCH_SLOT=0.8,   # assumed: tongue in the plate's front skin, root at the bottom; cavity open to the back face so the slicer can support it
    CATCH_NOSE=2.3, CATCH_NOSE_H=4.0, CATCH_NOSE_Z=16.0, CATCH_PAD=(1.5, 2.5, 5.0), CATCH_WIN=(9.5, 10.5), CATCH_WIN_CLR=0.5,   # assumed: nose z = root + 16; push pad (proud, height, above nose top); window through the back wall (w, h)
    # antenna: SMA bulkhead pigtail + stubby SMA antenna, black body about 9.5 dia, antenna about 47 long including its brass
    # connector (read off a ruler photo of the delivered part earlier; no maker's drawing of it is on file). Mounted INSIDE: the jack's neck slides into a slotted shelf FROM THE FRONT with its
    # flange under the shelf (nut and washer taken off first, then refitted on top: the nut clamps it), the body snaps into a
    # clip. The knock-out in the top wall above it takes the same jack if an outside antenna is ever wanted.
    ANT_X=86.0, ANT_Y=22.0, ANT_D=9.5, ANT_L=47.0, ANT_SHELF_Z=62.0, ANT_SHELF_T=2.5, ANT_SLOT_W=6.6, ANT_CLIP_Z=100.0,
    SMA_KO=(84.0, 17.5),     # assumed optional SMA knock-out on the top wall
    # label recess removed: it was on the face that sits on the print bed, so it printed over nothing. Use a sticker.
    SADDLES=((30.0, 74.0),),   # assumed: one cable tie saddle on the back wall for the lead bundle (x, z)
    # retention added after the six-direction audit (audit_retention.py): nothing may move more than about 0.5 mm
    # v9.5: parts stay put with the lid OFF. Clips flex across the print layers here (the body prints back-face down), so
    # their strain is held under SNAP_STRAIN_XLAYER, well below the limit used for flexures that print flat.
    SNAP_STRAIN_XLAYER=0.7,
    BRD_BARB=(0.5, 6.0, 22.0, 41.0),   # board catch engagement over the PCB edge, catch length, J3-side start Xb, J2-side start Xb (the J2 catch sits beyond the flex fold)
    HOLDER_ARM_ROOT=3.0,             # review: the arm is slotted free of the end rib except for this much at the back wall
    HOLDER_ARM=(2.0, 6.0, 24.9, 0.8),  # assumed: battery holder snap arm thickness (X), width (Z), lower edge z, engagement over the holder's front face
    HOLD_POST=(4.0, 8.0, 0.3),      # assumed: lid posts on the holder's end blocks (X thickness, Z width, clearance)
    CELL_RIB=(16.0, 3.0, 0.5),       # assumed: lid ribs in front of the cell (X length, Z width, clearance)
    HALL_PIN_D=3.1, HALL_PIN_X=3.2,  # assumed: TWO holes for 2.85 mm filament offcuts (6.0 to 6.5 long), one each side of the sensor's legs right behind its body: the legs pass between them, the 4.1 mm body cannot

    # ---- cleaning-mode button UNDER THE BASE (Owen: out of sight of the public, above the hook) ----------
    BTN16=(16.4, 18.8, 3.2, 16.0, 22.0, 3.2),   # maker (Gebildet listing drawing, APIELE AP16B datasheet for the same family): M16 x 1 thread in a 16 mm hole (16.4 printed), head dia 18.8 max,
                             # 3.2 allowed under the base for the head on its uncompressed O-ring, body dia 16, nut 22 across corners x 3.2
    BTN16_METAL_L=18.9,      # with BTN16_SOCKET_L this makes 44.5 behind the head = Gebildet's printed 46 mm overall minus the 1.6 mm head (Owen's own part reads 42.5 to 43.0, so 44.5 already carries margin)
    BTN16_SOCKET_L=25.6,     # the blue plug-in wire socket that pushes onto the button's pins (five wires leave its end): Gebildet's listing says 2.5 cm, and 25.6 was read off Owen's photo earlier.
                             # What matters is the SUM with BTN16_METAL_L (44.5): the split between the two is only how the reference solid is drawn
    BTN16_PINS_L=7.5,        # bare pins if the socket is left off and the wires are soldered on. Maker: five blade pins 6.5 to 7.1 long. Only read when BTN16_USE_SOCKET is False
    BTN16_USE_SOCKET=True,   # True keeps the plug-in socket (no soldering at the button, swap a button by unplugging). KEEP IT TRUE. False is NOT ready to use:
                             # the model would then allow BTN16_METAL_L + BTN16_PINS_L = 26.4 mm behind the head, but Gebildet's drawing gives 32.8 without the socket
                             # (16.7 head and metal + 10.7 plastic body + 7 pins, less the 1.6 head), so the bay would come out too short for the button
    BTN16_XY=(83.8, 21.3),   # assumed: through the bottom wall behind the right latch arm, clear of the hook channel strip (x 30..70) and of the rounded inside corner at the side wall
    BTN16_WIRE=6.0,          # assumed: room above the socket for the five wires to turn
    BTN16_ON=True,           # False builds the box without the button or the basement (the old 130 mm tall box)
                             # Fitting: bare button up through the hole from below, nut on from inside, then the blue socket onto its pins from inside
                             # (the socket will not pass through the hole). Of the socket's five wires only the two switch wires go to the board.
                             # Firmware: TEST_BUTTON_PIN = 3 in firmware/include/pinout.h is RESERVED as the cleaning-mode trigger, and
                             # firmware/src/hanger/hanger.cpp sets the pin as an input with pull-up, but the hanger loop does not act on a press
                             # yet, so no document may tell the builder to check for "cleaning mode". The wiring check is a meter continuity test.
                             # The button's LED ring is a 12 to 24 V type (Gebildet's listing), so it will not light from the board's 3.3 V: its wires stay unconnected.

    # ---- Gateway ----------------------------------------------------------------------
    G_W=120.0, G_H=80.0, G_D=30.0,    # assumed
    G_BRD_X0=46.0, G_BRD_ZC=42.0, G_PCB_TOP_Y=7.5,   # assumed
    G_SMA=(104.0, 15.0), SMA_HOLE_D=6.5, SMA_FLAT=6.0, SMA_PAD_D=14.0, SMA_WALL=3.0,   # datasheet D-hole
    G_CABLE_ZC=42.0, G_CABLE_D=4.5, G_CABLE_NOTCH_W=7.0,   # assumed cable
    G_SADDLE=(4.5, 14.0, 9.5),        # assumed tie saddle x0, x1, front face Y (behind the plug overmold)
    G_KEYHOLES=((25.0, 62.0), (95.0, 62.0)), G_LOWER_SCREW=(60.0, 16.0),   # assumed (screw positions)
    G_VENT=dict(len=8.0, w=2.0, pitch=8.0, n=5, bot_x0=72.0, top_x0=16.0, ys=(13.0, 18.0, 23.0)),
    G_BTN_KO=(25.0, 15.0, 12.5),      # assumed knock-out for a 12 mm panel button on GPIO3
    WHIP_D=13.0, WHIP_L=195.0,        # research: 868 MHz 5 dBi whip
)
EPS = 0.01
EX = 45.0    # exploded view offset

# --------------------------------------------------------------------------------------
# helpers
# --------------------------------------------------------------------------------------
def box(x0, x1, y0, y1, z0, z1):
    return cq.Workplane("XY").box(x1 - x0, y1 - y0, z1 - z0, centered=False).translate((x0, y0, z0))

def rbox_y(x0, x1, y0, y1, z0, z1, r):
    """Box with the four edges parallel to Y rounded (front-view corners)."""
    return box(x0, x1, y0, y1, z0, z1).edges("|Y").fillet(r)

def cyl_y(cx, cz, d, y0, y1):
    """Cylinder along Y from y0 to y1 (y1 > y0)."""
    return cq.Workplane("XY").add(cq.Solid.makeCylinder(d / 2, y1 - y0, cq.Vector(cx, y0, cz), cq.Vector(0, 1, 0)))

def cyl_z(cx, cy, d, z0, z1):
    return cq.Workplane("XY").add(cq.Solid.makeCylinder(d / 2, z1 - z0, cq.Vector(cx, cy, z0), cq.Vector(0, 0, 1)))

def cyl_x(cy, cz, d, x0, x1):
    return cq.Workplane("XY").add(cq.Solid.makeCylinder(d / 2, x1 - x0, cq.Vector(x0, cy, cz), cq.Vector(1, 0, 0)))

def cone_y(cx, cz, d0, d1, y0, y1):
    """Cone along +Y: diameter d0 at y0, d1 at y1."""
    return cq.Workplane("XY").add(cq.Solid.makeCone(d0 / 2, d1 / 2, y1 - y0, cq.Vector(cx, y0, cz), cq.Vector(0, 1, 0)))

def slot_y(cx, cz, length, width, y0, y1, angle=90):
    """Stadium slot in the XZ plane (length along Z when angle=90), extruded along Y."""
    return cq.Workplane("XZ", origin=(0, y1, 0)).center(cx, cz).slot2D(length, width, angle).extrude(y1 - y0)

def keyhole_y(cx, cz_head, head_d, slot_w, slot_len, y0, y1):
    """Keyhole along Y for a wall-hung part: head circle at cz_head (BELOW the engaged screw or peg), slot running UP
    by slot_len to the engaged position. Hang: offer the part up so the head passes the circle, then let it drop."""
    k = cyl_y(cx, cz_head, head_d, y0, y1)
    k = k.union(box(cx - slot_w / 2, cx + slot_w / 2, y0, y1, cz_head, cz_head + slot_len))
    return k.union(cyl_y(cx, cz_head + slot_len, slot_w, y0, y1))   # rounded slot end centred on the engaged peg

def prism_yz(pts, x0, x1):
    """Polygon in the YZ plane (list of (y, z)) extruded from x0 to x1."""
    return cq.Workplane("YZ", origin=(x0, 0, 0)).polyline(pts).close().extrude(x1 - x0)

def prism_xz(pts, y0, y1):
    """Polygon in the XZ plane (list of (x, z)) extruded from y0 to y1 (the XZ workplane normal is -Y)."""
    return cq.Workplane("XZ", origin=(0, y1, 0)).polyline(pts).close().extrude(y1 - y0)

def csk_hole_y(cx, cz, y_face, y_end, d, csk_d, csk_depth):
    """Countersunk through hole, head opening on the face at y_face (which faces -Y), hole to y_end."""
    h = cyl_y(cx, cz, d, y_face - 1, y_end + 1)
    c = cone_y(cx, cz, csk_d, d, y_face, y_face + csk_depth)
    c2 = cyl_y(cx, cz, csk_d, y_face - 1, y_face + EPS)
    return h.union(c).union(c2)

def cb_hole_y(cx, cz, y_face, y_end, d, cb_d, cb_depth):
    """Counterbored through hole, head opening on the face at y_face (which faces -Y)."""
    return cyl_y(cx, cz, d, y_face - 1, y_end + 1).union(cyl_y(cx, cz, cb_d, y_face - 1, y_face + cb_depth))

def bbox(wp):
    return wp.val().BoundingBox()

def bbox_str(wp):
    bb = bbox(wp)
    return "X %.1f..%.1f  Y %.1f..%.1f  Z %.1f..%.1f  (%.1f x %.1f x %.1f mm)" % (
        bb.xmin, bb.xmax, bb.ymin, bb.ymax, bb.zmin, bb.zmax, bb.xlen, bb.ylen, bb.zlen)

def union_all(shapes):
    out = None
    for s in shapes:
        out = s if out is None else out.union(s)
    return out

def hdr_x(pin):
    """Xb of header pin n (1..18)."""
    return P["HDR_X1"] + (pin - 1) * P["HDR_PITCH"]

# --------------------------------------------------------------------------------------
# Heltec WiFi LoRa 32 V3: reference model and the shared board cradle
# --------------------------------------------------------------------------------------
def btn16_len():
    """Length behind the button's head: metal body plus the plug-in socket (or the bare pins)."""
    return P["BTN16_METAL_L"] + (P["BTN16_SOCKET_L"] if P["BTN16_USE_SOCKET"] else P["BTN16_PINS_L"])

def _apply_basement():
    """The battery holder sits 7 mm above the bottom wall across nearly the full width, and the button is far longer than
    that. So the box grows DOWNWARD by H_BASEMENT: every hanger feature keeps its place relative to the top, and the button
    gets an empty bay under the battery. One number (the button's length) sets it."""
    if not P.get("BTN16_ON"):
        P["H_BASEMENT"] = 0.0
        return
    blen = btn16_len()
    need = (blen - P["WALL"]) + P["BTN16_WIRE"]                       # clear height wanted above the bottom wall's inner face
    have = (P["HOLDER_Z0"] - P["HOLDER_CLR"] - P["HOLDER_RIB_T"]) - P["WALL"]   # what is there now, under the holder's locating rib
    b = float(max(0, math.ceil(need - have)))
    P["H_BASEMENT"] = b
    for k in ("H_H", "H_BRD_ZC", "HOLDER_Z0", "BP_H", "CATCH_Z0", "ANT_SHELF_Z", "ANT_CLIP_Z"):
        P[k] += b
    P["BULK_Z"] = tuple(z + b for z in P["BULK_Z"])
    P["PEG_ZS"] = tuple(z + b for z in P["PEG_ZS"])
    P["SADDLES"] = tuple((x, z + b) for (x, z) in P["SADDLES"])
    a = P["HOLDER_ARM"]; P["HOLDER_ARM"] = (a[0], a[1], a[2] + b, a[3])
    l = P["H_LOGO"]; P["H_LOGO"] = (l[0], l[1] + b, l[2])
    w = P["H_WORDMARK"]; P["H_WORDMARK"] = (w[0], w[1] + b, w[2], w[3])
_apply_basement()

def b2w(shape, x0, zc, pcb_top_y):
    """Board frame (Xb, Yb, Zb) -> world (x0 + Xb, pcb_top_y - Zb, zc + Yb)."""
    return shape.rotate((0, 0, 0), (1, 0, 0), 90).translate((x0, pcb_top_y, zc))

def heltec_ref(x0, zc, pcb_top_y):
    """Simplified Heltec V3 envelope (PCB outline, OLED, USB-C, buttons, IPEX socket + U.FL plug,
    battery socket, ESP32 module, V3.2 block antenna) as one reference solid in world coordinates."""
    t = P["BRD_T"]
    outline = [(0, 5.27), (1.27, 4.0), (1.27, -4.0), (0, -5.27), (0, -10.54), (2.16, -12.7),
               (47.88, -12.7), (51.69, -8.89), (51.69, 8.89), (47.88, 12.7), (2.16, 12.7), (0, 10.54)]
    parts = [cq.Workplane("XY").polyline(outline).close().extrude(-t)]     # Zb -t..0
    parts.append(box(P["OLED_X0"], P["OLED_X1"], -P["OLED_HALF_W"], P["OLED_HALF_W"], 0, P["OLED_H"]))
    parts.append(box(-P["USB_NOSE"], 7.7, -P["USB_SHELL_W"] / 2, P["USB_SHELL_W"] / 2, -1.08, P["USB_SHELL_H"]))
    for (bx, by) in (P["PRG"], P["RST"]):
        parts.append(box(bx - 2.0, bx + 2.0, by - 1.5, by + 1.5, 0, P["BTN_H"]))
    ix, iy = P["IPEX"]
    parts.append(box(ix - 1.55, ix + 1.55, iy - 1.5, iy + 1.5, 0, P["IPEX_H"] + P["UFL_PLUG_H"]))
    sx0, sx1, shw, sh = P["BAT_SOCK"]
    parts.append(box(sx0, sx1, -shw, shw, -t - sh, -t))
    parts.append(box(20.4, 27.4, -3.5, 3.5, -t - 0.8, -t))
    parts.append(box(45.0, 51.0, 8.0, 12.7, 0, 1.6))    # V3.2 block antenna (approx)
    # maker (Heltec STEP + photos): the display's flex tail folds over the RST-side board edge and tucks underneath; and the
    # display carrier is held by three screws whose heads stand proud of the underside
    parts.append(box(23.6, 39.2, -13.0, -10.0, -t - 0.3, 5.0))
    for (sx_, sy_) in ((16.78, -7.0), (45.98, -7.0), (45.98, 7.0)):
        parts.append(cq.Workplane("XY").circle(1.6).extrude(-1.2).translate((sx_, sy_, -t)))
    if P.get("COIL"):                                   # V3.x boards: WiFi coil (spring) antenna standing beside the display, position from Heltec's detailed STEP
        kx, ky, kd, kh = P["COIL"]
        parts.append(cq.Workplane("XY").circle(kd / 2).extrude(kh).translate((kx, ky, 0)))
    return b2w(union_all(parts), x0, zc, pcb_top_y)

def board_cradle(x0, zc, pcb_top_y, y_back, x_wall_inner, setback=None):
    """Screwless cradle for the Heltec V3: a ledge under each long edge (the board rests on it),
    pocket side walls, an end stop at the antenna tip, corner stops at the USB end. The J3 (+Z, PRG)
    ledge has gaps at the wire pads (GND, 3V3, GPIO3, GPIO6). A notch in the J2 (-Z) wall lets the
    battery lead and the Hall wires out from under the board. The display's flex tail folds over the J2
    (RST side) board edge (FLEX_FOLD): the J2 ledge stops either side of it, the J2 wall is relieved
    there, and the J2 catch and the lead notch both stand clear of it. The three carrier screw heads
    under the board are inboard of both ledges, so nothing touches them."""
    L, clr = P["BRD_L"], P["BRD_CLR"]
    hw = P["BRD_W"] / 2 + clr                     # pocket half height (Z)
    pcb_bot = pcb_top_y + P["BRD_T"]
    y_lip = max(pcb_top_y - P["RAIL_LIP_ABOVE"], 0.5)      # pocket walls rise above the PCB top but stop 0.5 under the lid
    wt = P["POCKET_WALL_T"]
    x_start = max(x0 - (setback if setback is not None else P["USB_SETBACK"]), x_wall_inner + P["TONGUE_T"] + P["TONGUE_CLR"] + 0.3)
    x_end = x0 + L + clr + 2.0
    parts = []
    # J2 side (-Z): continuous ledge and wall
    fx0, fx1 = P["FLEX_FOLD"]
    for (la, lb) in ((1.5, fx0), (fx1, L - 3.0)):                      # the ledge stops either side of the display's flex fold
        parts.append(box(x0 + la, x0 + lb, pcb_bot, y_back + EPS, zc - hw, zc - hw + P["RAIL_W"]))
    parts.append(box(x_start, x_end, y_lip, y_back + EPS, zc - hw - wt, zc - hw))
    # J3 side (+Z): ledge segments avoiding the wire pads
    gaps = [(hdr_x(p) - 2.2, hdr_x(p) + 2.2) for p in P["WIRE_PINS_J3"]]
    xs = 1.5
    segs = []
    for (g0, g1) in sorted(gaps):
        if g0 > xs + 1.0:
            segs.append((xs, g0))
        xs = max(xs, g1)
    if xs < L - 3.0:
        segs.append((xs, L - 3.0))
    for (s0, s1) in segs:
        parts.append(box(x0 + s0, x0 + s1, pcb_bot, y_back + EPS, zc + hw - P["RAIL_W"], zc + hw))
    parts.append(box(x_start, x_end, y_lip, y_back + EPS, zc + hw, zc + hw + wt))
    # end stop at the antenna tip, below the PCB top so the U.FL plug and cable pass over it
    parts.append(box(x0 + L + clr, x_end, pcb_top_y, y_back + EPS, zc - 5.0, zc + 5.0))
    # USB-end corner stops (outside the button footprint, below the PCB top plane)
    xs0 = max(x_wall_inner - EPS, x0 - 3.0)
    for s in (-1, 1):
        z0, z1 = sorted((zc + s * 10.0, zc + s * hw))
        parts.append(box(xs0, x0 - clr, max(pcb_top_y, P["TONGUE_H"] + 0.4), y_back + EPS, z0, z1))   # starts below the lid's lip
    # catches: a 45 deg barb on each pocket wall's inner face hooks over the PCB's long edge, so the board stays in
    # with the lid off. Push the board straight in to fit it; lever one edge out with a fingernail to remove it.
    e, bl, xb3, xb2 = P["BRD_BARB"]
    b = e + clr
    yc = pcb_top_y - 0.05 - e
    for (zf, sgn, xb) in ((zc + hw, -1, xb3), (zc - hw, 1, xb2)):
        parts.append(prism_yz([(yc + b, zf - sgn * EPS), (yc, zf + sgn * b), (yc - 0.4, zf + sgn * b), (yc - 0.4 - 1.25 * b, zf - sgn * EPS)], x0 + xb, x0 + xb + bl))
    cradle = union_all(parts)
    # the flex adds about 0.3 mm outside the board edge where it folds over: relieve the J2 wall's inner face there
    cradle = cradle.cut(box(x0 + fx0, x0 + fx1, -1, y_back - 0.01, zc - hw - 0.6, zc - hw + EPS))
    # lead notch through the J2 wall + ledge, leaving the front part of the wall as a bridge
    n0, n1 = P["LEAD_NOTCH"]
    cradle = cradle.cut(box(x0 + n0, x0 + n1, pcb_bot + 5.0, y_back + 1, zc - hw - wt - 1, zc - hw + P["RAIL_W"] + 1))
    return cradle

def lid_header_ribs(x0, zc, pcb_top_y):
    """Ribs on the lid inner face bearing on the header pad strips (no headers fitted). Both start at Xb 13, clear of
    the button pads. The J3 rib stops at Xb 34 so it clears the wire solder joints. The J2 (RST side) rib stops at the
    start of the display's flex fold (FLEX_FOLD), so nothing bears on the fold. Each rib has a gap wherever a board
    catch on the pocket wall stands inside its length."""
    hw = P["BRD_W"] / 2 + P["BRD_CLR"]
    z_out = hw - P["POCKET_WALL_T"] * 0 - 0.3      # rib outer edge, 0.3 inside the pocket wall
    y1 = pcb_top_y - P["LID_RIB_CLR"]
    w = P["LID_RIB_W"]
    e, bl, xb3, xb2 = P["BRD_BARB"]
    def rib(xa, xb, z0, z1, gap0):
        r = box(x0 + xa, x0 + xb, -EPS, y1, z0, z1)
        return r.cut(box(x0 + gap0 - 1.0, x0 + gap0 + bl + 1.0, -1, y1 + 1, z0 - 1, z1 + 1))     # clear of the board catch
    fx0, fx1 = P["FLEX_FOLD"]
    j2 = rib(13.0, fx0, zc - z_out, zc - z_out + w, xb2)      # RST side: stops before the display's flex fold; beyond the fold the board catch stands, so there is no rib there
    j3 = rib(13.0, 34.0, zc + z_out - w, zc + z_out, xb3)
    return j2.union(j3)

def lid_board_features(lid, x0, zc, pcb_top_y, lid_t, flush=False, vertical=None):
    """Common lid features over the board. Both lids: the display window, centred on the PICTURE (the panel maker's active
    area, OLED_ACT_CX / OLED_ACT_CY) and flared 45 deg outward through the bezel, and the two button pads (lid_buttons). The
    gateway lid also has an open LED light hole; the hanger lid has none (H_LED_HOLE). flush=True (hanger): the display module
    itself sits in a pocket behind a BEZEL_T skin; the lid is relieved over the display's flex fold, and a round relief
    (COIL_KEEPOUT_D under a COIL_SKIN face skin) leaves air all round the coil antenna, which nothing may touch; reliefs for
    the USB-C shell and the mated U.FL plug are cut only if they would reach the lid. No insert, no cleats. flush=False
    (gateway): a pocket inside the lid with two cleats that hold a clear window insert."""
    cx = x0 + P["OLED_ACT_CX"]
    cz = zc + P["OLED_ACT_CY"]
    ww, wh = P["WIN_W"], P["WIN_H"]
    lid = lid.cut(box(cx - ww / 2, cx + ww / 2, -lid_t - 1, 1, cz - wh / 2, cz + wh / 2))
    # true 45 deg flare round the outside of the window, BEZEL_T - 0.2 deep (self-supporting face down; the old square rebate
    # left a one-layer flash ring round the display)
    c = P["BEZEL_T"] - 0.2          # flared almost through the bezel (0.2 mm land at the glass side), so the edge rows are not hidden when you look from an angle
    cha = prism_yz([(-lid_t - 1, cz - wh / 2 - c - 1), (-lid_t - 1, cz + wh / 2 + c + 1), (-lid_t + c, cz + wh / 2), (-lid_t + c, cz - wh / 2)], cx - ww / 2 - c - 2, cx + ww / 2 + c + 2)
    chb = cq.Workplane("XY").polyline([(cx - ww / 2 - c - 1, -lid_t - 1), (cx + ww / 2 + c + 1, -lid_t - 1), (cx + ww / 2, -lid_t + c), (cx - ww / 2, -lid_t + c)]).close() \
        .extrude(wh + 2 * c + 4).translate((0, 0, cz - wh / 2 - c - 2))
    lid = lid.cut(cha.intersect(chb))
    if flush:
        # the display module itself sits in this pocket, its glass OLED_GAP behind a BEZEL_T front skin; no insert, no cleats
        pxa, pxb, pya, pyb = P["OLED_POCKET"]
        lid = lid.cut(box(x0 + pxa, x0 + pxb, -lid_t + P["BEZEL_T"], 0.5, zc + pya, zc + pyb))
        # the display's flex tail folds over the RST-side board edge as high as the display itself: relieve the lid over it
        ffa, ffb = P["FLEX_FOLD"]
        flex_top = pcb_top_y - 5.0 - 0.4
        if flex_top < 0:
            lid = lid.cut(box(x0 + ffa, x0 + ffb, flex_top, 0.5, zc - P["BRD_W"] / 2 - 0.8, zc + pya + EPS))
        if P.get("COIL"):
            # the coil antenna's position is known from Heltec's STEP: a round relief of COIL_KEEPOUT_D leaves air all round
            # it under a COIL_SKIN face skin. It stops at the pads' end slot, so the pad itself is never thinned.
            kx, ky, kd, kh = P["COIL"]
            relief = cyl_y(x0 + kx, zc + ky, P["COIL_KEEPOUT_D"], -lid_t + P["COIL_SKIN"], 0.5)
            relief = relief.intersect(box(x0 + P["BTN_PAD_X1"] + P["BTN_PAD"][5], x0 + pxb, -lid_t, 1.0, zc - 20, zc + 20))
            lid = lid.cut(relief)
        # relief over the USB-C shell (3.25 above the PCB top) where it would touch the lid
        usb_top = pcb_top_y - 3.25 - 0.4
        if usb_top < 0:
            lid = lid.cut(box(x0 - 0.9, x0 + 8.2, usb_top, 0.5, zc - 5.2, zc + 5.2))
        # relief over the mated U.FL plug (socket + plug can reach 3.8 above the PCB top)
        ufl_top = pcb_top_y - (P["IPEX_H"] + P["UFL_PLUG_H"]) - 0.4
        if ufl_top < 0:
            ix, iz = x0 + P["IPEX"][0], zc + P["IPEX"][1]
            lid = lid.cut(box(ix - 4.0, ix + 4.0, ufl_top, 0.5, iz - 4.0, iz + 4.0))
    else:
        iw, ih, pd = P["INSERT_W"], P["INSERT_H"], P["INSERT_POCKET"]
        lid = lid.cut(box(cx - iw / 2, cx + iw / 2, -pd, 0.5, cz - ih / 2, cz + ih / 2))
        # cleats on the short pocket edges: insert flexes in under them
        c = P["INSERT_CLEAT"]
        for s in (-1, 1):
            xa, xb = sorted((cx + s * iw / 2, cx + s * (iw / 2 - c)))
            lid = lid.union(box(xa, xb, -pd + P["INSERT_T"] + 0.2, -pd + P["INSERT_T"] + 0.9, cz - 4.0, cz + 4.0))
    lid = lid_buttons(lid, x0, zc, pcb_top_y, lid_t, vertical, led_hole=P["H_LED_HOLE"] if flush else P["G_LED_HOLE"])
    return lid

def button_pads(x0, zc, vertical=None):
    """(name, pad x0, x1, z0, z1, pin x, pin z, hinge) for the two board buttons. hinge is 'x0' (hinge at the pad's left
    end, pad runs along X) or 'z0' / 'z1' (pad runs along Z, hinge at its far end from the board centreline)."""
    fw, fh = P["BTN_PAD"][0], P["BTN_PAD"][1]
    fx1 = x0 + P["BTN_PAD_X1"]
    out = []
    for name, (bx, bz) in (("PRG", P["PRG"]), ("RST", P["RST"])):
        sgn = 1 if bz > 0 else -1
        if vertical:
            vx0, vh, pd, pdx = vertical
            za, zb = sorted((zc + sgn * P["BTN_PAD_GAP"], zc + sgn * (P["BTN_PAD_GAP"] + vh)))
            out.append((name, vx0, fx1, za, zb, x0 + bx + pdx, zc + bz, "z1" if sgn > 0 else "z0"))
        else:
            za, zb = sorted((zc + sgn * P["BTN_PAD_GAP"], zc + sgn * (P["BTN_PAD_GAP"] + fh)))
            out.append((name, fx1 - fw, fx1, za, zb, x0 + bx, zc + bz, "x0"))
    return out

def lid_buttons(lid, x0, zc, pcb_top_y, lid_t, vertical=None, led_hole=True):
    """Two pads in the face. Each is a flap: a slot cut right through on three sides, a thin hinge on the fourth (it
    prints flat on the bed, so it bends along the layers), and a pin on the back that sits just over the small switch
    on the board. Pressing anywhere on the pad clicks the switch."""
    fw, fh, ft, ht, hl, sl = P["BTN_PAD"]
    pin_d = vertical[2] if vertical else P["BTN_PIN_D"]
    for (name, fx0, fx1, z0, z1, px, pz, hinge) in button_pads(x0, zc, vertical):
        lid = lid.cut(box(fx0 - (0 if hinge == "x0" else sl), fx1 + sl, -lid_t + ft, 1, z0 - (0 if hinge == "z0" else sl), z1 + (0 if hinge == "z1" else sl)))
        if hinge == "x0":
            lid = lid.cut(box(fx0, fx0 + hl, -lid_t + ht, 1, z0 - sl, z1 + sl))
            slots = [(fx1, fx1 + sl, z0 - sl, z1 + sl), (fx0, fx1 + sl, z0 - sl, z0), (fx0, fx1 + sl, z1, z1 + sl)]
        else:
            ha, hb = (z1 - hl, z1) if hinge == "z1" else (z0, z0 + hl)
            lid = lid.cut(box(fx0 - sl, fx1 + sl, -lid_t + ht, 1, ha, hb))
            fe = (z0 - sl, z0) if hinge == "z1" else (z1, z1 + sl)            # free end is the side nearer the board centreline
            za, zb = (z0 - sl, z1) if hinge == "z1" else (z0, z1 + sl)
            slots = [(fx0 - sl, fx1 + sl, fe[0], fe[1]), (fx0 - sl, fx0, za, zb), (fx1, fx1 + sl, za, zb)]
        for (xa, xb, zca, zcb) in slots:
            lid = lid.cut(box(xa, xb, -lid_t - 1, 1, zca, zcb))
        lid = lid.union(cyl_y(px, pz, pin_d, -lid_t + ft - EPS, pcb_top_y - P["BTN_H"] - P["BTN_PIN_GAP"]))
    # light hole over the status LEDs (the hanger has none: H_LED_HOLE)
    if led_hole:
        lid = lid.cut(cyl_y(x0 + P["LED"][0], zc + P["LED"][1], P["LED_HOLE_D"], -lid_t - 1, 1))
    return lid

def face_marks(W, lid_t, logo, wordmark, x0, zc, vertical=None):
    """Everything sunk into the face: the badge outline with its exclamation mark, the HazardLink wordmark and the two
    button names. Narrow strokes only, so they print cleanly on the bed; the same solids are the second-colour inlay."""
    y1 = -lid_t + P["MARK_DEPTH"]; y0 = -lid_t - 1.0
    bw, bh, br, bs, tilt = P["LOGO_BADGE"]
    ew, eh, ez, dd, dz = P["LOGO_BANG"]
    lx, lz, k = logo
    def rr(w, h, r):
        return box(-w / 2, w / 2, y0, y1, -h / 2, h / 2).edges("|Y").fillet(r)
    badge = rr(bw * k, bh * k, br * k).cut(rr((bw - 2 * bs) * k, (bh - 2 * bs) * k, max((br - bs) * k, 0.6)))
    bang = rr(ew * k, eh * k, ew * k / 2 - 0.05).translate((0, 0, ez * k))
    dot = cyl_y(0, dz * k, dd * k, y0, y1)
    mark = badge.union(bang).union(dot).rotate((0, 0, 0), (0, 1, 0), -tilt).translate((lx, 0, lz))
    def txt(s, x, z, h, halign="left", turn=0):
        t = cq.Workplane("XZ", origin=(0, y1, 0)).text(s, h, y1 - y0, halign=halign, valign="center", kind="bold")
        if turn:
            t = t.rotate((0, 0, 0), (0, 1, 0), -turn)
        return t.translate((x, 0, z))
    tx, tz, th, ta = wordmark
    mark = mark.union(txt("HazardLink", tx, tz, th, halign=ta))
    for (name, fx0, fx1, z0, z1, px, pz, hinge) in button_pads(x0, zc, vertical):
        if hinge == "x0":
            mark = mark.union(txt(name, (fx0 + P["BTN_PAD"][4] + fx1) / 2, (z0 + z1) / 2, 5.0, halign="center"))
        else:       # tall narrow pad: the name reads upward, placed toward the free end away from the hinge
            zm = (z0 + z1) / 2 + (-2.0 if hinge == "z1" else 2.0)
            lh, lx = P["BTN_LABEL"]
            mark = mark.union(txt(name, fx0 + lx, zm, lh, halign="center", turn=90))
    return mark

def lid_tongue(W, H, wall, bosses, cutouts=()):
    """Inner lip ring (2 x 4) sitting just inside the body walls, relieved around the bosses and
    at any listed cut-outs (x0, x1, z0, z1)."""
    t, h, c = P["TONGUE_T"], P["TONGUE_H"], P["TONGUE_CLR"]
    o = wall + c
    ring = rbox_y(o, W - o, 0, h, o, H - o, P["CORNER_R"] - o)
    ring = ring.cut(rbox_y(o + t, W - o - t, -1, h + 1, o + t, H - o - t, 0.6))
    for (bx, bz) in bosses:
        ring = ring.cut(cyl_y(bx, bz, P["BOSS_D"] + 0.6, -1, h + 1))
    for (x0, x1, z0, z1) in cutouts:
        ring = ring.cut(box(x0, x1, -1, h + 1, z0, z1))
    return ring

def arm_geom(root_x, direction):
    """X stations of one wall arm. direction +1: free end toward +X."""
    tip = root_x + direction * P["ARM_L"]
    slot_far = tip + direction * P["ARM_SLOT"]
    win_cx = tip - direction * P["ARM_WIN_FROM_TIP"]
    return dict(root=root_x, tip=tip, slot_far=slot_far, win_cx=win_cx, d=direction)

def lid_snap_features(lid, W, H, wall, arms, tab_xs):
    """Rigid hooks on the bottom edge (they drop into the windows of the body's wall arms) and two rigid hinge tabs on the
    top edge. Nothing on the lid flexes."""
    o = wall + P["TONGUE_CLR"]                      # tongue outer face (bottom edge at z=o, top edge at z=H-o)
    hw, ht, hl = P["HOOK_W"] / 2, P["HOOK_T"], P["HOOK_L"]
    cy, fl, bb = P["HOOK_CATCH_Y"], P["HOOK_FLAT"], P["HOOK_BARB"]
    for (rx, d) in arms:
        g = arm_geom(rx, d)
        x = g["win_cx"]
        post = box(x - hw, x + hw, -EPS, hl, o, o + ht)
        # barb under the post: flat catch face toward the lid (it bears on the window's front edge), ramp toward the box
        barb = prism_yz([(cy, o + EPS), (cy, o - bb), (cy + fl, o - bb), (hl, o + EPS)], x - hw, x + hw)
        gus = prism_yz([(-EPS, o + ht - EPS), (-EPS, o + ht + P["HOOK_GUSSET"]), (P["HOOK_GUSSET"], o + ht - EPS)], x - hw, x + hw)
        lid = lid.union(post).union(barb).union(gus)
    tab_top = H - wall - P["TONGUE_CLR"] - P["TONGUE_T"]        # contiguous with the tongue's inner face
    tab_bot = tab_top - P["TONGUE_T"] - 0.25
    nose_y0 = P["TAB_RIB_Y0"] + 2.5 + P["TAB_CLR"]              # behind the 2.5 mm cheek of the rib pocket
    nose_y1 = nose_y0 + P["TAB_NOSE_L"]
    nose_top = tab_top + P["TAB_NOSE"]
    for x in tab_xs:
        tab = box(x - P["TAB_W"] / 2, x + P["TAB_W"] / 2, -EPS, P["TAB_L"], tab_bot, tab_top)
        nose = prism_yz([(nose_y0, tab_top - EPS), (nose_y1, tab_top - EPS), (nose_y1, nose_top), (nose_y0 + P["TAB_NOSE"], nose_top)],
                        x - P["TAB_W"] / 2, x + P["TAB_W"] / 2)
        lid = lid.union(tab).union(nose)
    return lid

def body_snap_features(body, W, H, wall, y_back, arms, tab_xs):
    """Spring arms cut into the bottom wall (one slot along X behind the arm, one end slot; the arm runs out to the rim),
    each with a window for the lid's hook and a pull lip underneath; hinge ribs on the top wall."""
    aw, at, sl = P["ARM_W"], P["ARM_T"], P["ARM_SLOT"]
    ww, wy0, wy1 = P["ARM_WIN"]
    ty, tz = P["ARM_TAB"]
    ll, lp = P["ARM_LIP"]
    for (rx, d) in arms:
        g = arm_geom(rx, d)
        xa, xb = sorted((g["root"], g["slot_far"]))
        body = body.cut(box(xa, xb, aw, aw + sl, -1.0, wall + EPS))                       # slot behind the arm
        ea, eb = sorted((g["tip"], g["slot_far"]))
        body = body.cut(box(ea, eb, -1.0, aw + sl, -1.0, wall + EPS))                     # end slot out to the rim
        ta, tb = sorted((g["root"] + d * 3.0, g["tip"]))
        body = body.cut(box(ta, tb, -1.0, aw, -1.0, wall - at))                           # thin the arm from outside
        body = body.cut(box(g["win_cx"] - ww / 2, g["win_cx"] + ww / 2, wy0, wy1, -1.0, wall + EPS))   # window for the hook
        # lead-in chamfer on the rim's inner edge so the hook's ramp rides up the arm
        body = body.cut(prism_yz([(-0.1, wall + 0.1), (-0.1, wall - 0.8), (0.8, wall + 0.1)], ta, tb))
        # breakaway tab across the end slot at the arm's back edge: the arm's first layers bridge root to tab
        body = body.union(box(ea - EPS, eb + EPS, aw - ty, aw, wall - at + 0.3, wall - at + 0.3 + tz))
        # pull lip under the tip, 45 deg on the side that prints first
        la, lb = sorted((g["tip"] - d * 0.5, g["tip"] - d * (0.5 + ll)))
        z_out = wall - at
        body = body.union(prism_yz([(0.5, z_out + EPS), (0.5, -lp), (4.5, -lp), (4.5 + z_out + lp, z_out + EPS)], la, lb))
    # hinge: a rib along the top wall from Y=TAB_RIB_Y0 to the back wall (grows from the bed, stiffens the wall) with the
    # nose pocket cut through its full height (a bridge on 2.5 mm cheeks); the pocket reaches TAB_POCKET_UP into the wall
    y0 = P["TAB_RIB_Y0"]
    pw = P["TAB_W"] + 1.0
    for x in tab_xs:
        body = body.union(box(x - P["TAB_W"] / 2 - P["TAB_RIB_SIDE"], x + P["TAB_W"] / 2 + P["TAB_RIB_SIDE"], y0, y_back + EPS, H - wall - P["TAB_RIB_H"], H - wall + EPS))
        body = body.cut(box(x - pw / 2, x + pw / 2, y0 + 2.5, y0 + 2.5 + P["TAB_NOSE_L"] + 2 * P["TAB_CLR"], H - wall - P["TAB_RIB_H"] - 1.0, H - wall + P["TAB_POCKET_UP"]))
    return body

def tie_saddle(cx, cz, y_back, along="Z"):
    """Cable tie saddle: 8 x 6 block on the back wall with a 5.5 x 2 tie tunnel through it."""
    blk = box(cx - 4, cx + 4, y_back - 7.0, y_back + EPS, cz - 3, cz + 3)
    if along == "Z":
        return blk.cut(box(cx - 2.75, cx + 2.75, y_back - 5.0, y_back - 3.0, cz - 4, cz + 4))
    return blk.cut(box(cx - 5, cx + 5, y_back - 5.0, y_back - 3.0, cz - 2.75, cz + 2.75))

def knockout_z(body, cx, cy, d, z_wall_outer, z_wall_inner):
    """Round knock-out in a wall parallel to XY: full hole from the inside, thin skin left outside."""
    lo, hi = sorted((z_wall_outer, z_wall_inner))
    skin = P["KNOCKOUT_SKIN"]
    if z_wall_inner > z_wall_outer:      # bottom wall: outer face below
        return body.cut(cyl_z(cx, cy, d, lo + skin, hi + 1))
    return body.cut(cyl_z(cx, cy, d, lo - 1, hi - skin))

# --------------------------------------------------------------------------------------
# HANGER
# --------------------------------------------------------------------------------------
def hanger_geom():
    """Derived hanger positions shared by body, lid, bar, backplate and references."""
    W, H, D, wall, lt = P["H_W"], P["H_H"], P["H_D"], P["WALL"], P["LID_T"]
    g = dict(W=W, H=H, D=D, wall=wall, y_back=D - wall, lid_t=lt,
             x0=P["H_BRD_X0"], zc=P["H_BRD_ZC"],
             pcb_top=max(-lt + P["BEZEL_T"] + P["OLED_GAP"] + P["OLED_H_MAX"],                          # glass (at most OLED_H_MAX above the PCB) just behind the bezel
                         -lt + P["COIL_SKIN"] + P["COIL_AIR"] + P["COIL"][3] + P["COIL_TOL"][1]))     # and a worst-case coil antenna still has air under a 3-layer skin
    g["bulk"] = P["BULK_Z"]
    g["holder_back"] = g["y_back"] - P["HOLDER_STANDOFF"]            # the holder's pin side rests here, on standoff ribs
    g["holder_front"] = g["holder_back"] - P["HOLDER_H"]
    g["cell_y"] = g["holder_back"] - P["HOLDER_H"] / 2 - 0.5        # cell axis
    # the wall face is at Y = D + BP_T; the bar runs from there forward to the lip
    g["wall_y"] = D + P["BP_T"]
    g["bar_x0"] = W / 2 - P["BAR_W"] / 2
    g["bar_x1"] = W / 2 + P["BAR_W"] / 2
    g["web_x0"] = W / 2 - P["WEB_W"] / 2
    g["web_x1"] = W / 2 + P["WEB_W"] / 2
    g["bar_top"] = -P["BAR_DROP"]
    g["bar_bot"] = g["bar_top"] - P["BAR_T"]
    g["web_y0"], g["web_y1"] = P["BAR_WEB_Y"]
    g["bar_back"] = g["web_y1"]
    # dovetail plate inside the bottom-wall channel: z from DT_CLR to DT_H - DT_CLR, widths follow the channel flanks
    g["plate_y0"], g["plate_y1"] = P["PLATE_Y"]
    g["plate_z0"], g["plate_z1"] = P["DT_CLR"], P["DT_H"] - P["DT_CLR"]
    slope = (P["DT_TOP"] - P["DT_MOUTH"]) / P["DT_H"]
    g["plate_w0"] = P["DT_MOUTH"] + slope * g["plate_z0"] - 2 * P["DT_CLR"]
    g["plate_w1"] = P["DT_MOUTH"] + slope * g["plate_z1"] - 2 * P["DT_CLR"]
    g["plate_bot"] = g["plate_z0"]
    g["strip_top"] = P["DT_H"] + P["DT_ROOF"]
    g["lip_front"] = g["wall_y"] - P["BAR_REACH"]
    g["lip_back"] = g["lip_front"] + P["BAR_LIP_T"]
    g["lip_top"] = g["bar_top"] + P["BAR_LIP_H"]
    g["saddle_y"] = P["BAR_SADDLE_Y"]
    g["saddle_floor"] = g["bar_top"] - P["BAR_SADDLE_D"]
    # Hall sensor under the saddle floor, entered from the bar's back end (under the body): a tunnel for the legs and the
    # soldered joints, and at its front a snug nest that holds the flat package right up under the saddle (nearest the magnet)
    pw, pl, pt = P["HALL_PKG"]
    ncs, ncf, ncz = P["HALL_NEST_CLR"]
    g["slot_ceil"] = g["saddle_floor"] - P["HALL_SKIN"]
    g["slot_floor"] = g["slot_ceil"] - P["HALL_SLOT_H"]
    g["slot_hw"] = P["HALL_TUNNEL_W"] / 2
    g["sensor_y"] = g["saddle_y"]
    g["nest_hw"] = pw / 2 + ncs
    g["nest_floor"] = g["slot_ceil"] - pt - 2 * ncz
    g["nest_y_back"] = g["sensor_y"] + pl / 2
    g["slot_y_front"] = g["sensor_y"] - pl / 2 - ncf
    g["sensor_z"] = g["slot_ceil"] - ncz - pt / 2
    g["wire_z0"] = g["slot_ceil"] - P["HALL_WIRE_H"]
    # backplate catch window (engaged position)
    g["catch_nose_z0"] = P["CATCH_Z0"] + P["CATCH_NOSE_Z"]
    g["win_z0"] = g["catch_nose_z0"] - P["CATCH_WIN_CLR"]
    g["win_z1"] = g["win_z0"] + P["CATCH_WIN"][1]
    return g

def build_hanger_body():
    g = hanger_geom()
    W, H, D, wall, yb = g["W"], g["H"], g["D"], g["wall"], g["y_back"]
    body = rbox_y(0, W, 0, D, 0, H, P["CORNER_R"])
    body = body.cut(rbox_y(wall, W - wall, -1, yb, wall, H - wall, P["CORNER_R"] - wall))
    # bulkhead between the battery bay and the board area
    bz0, bz1 = g["bulk"]
    body = body.union(box(wall - EPS, W - wall + EPS, 0, yb + EPS, bz0, bz1))
    # lead notches at both ends of the bulkhead for the two battery wires. Each is cut only from Y=12 back to the back wall, so
    # the front 12 mm of the bulkhead closes it (a 7.5 mm bridge when printed): it is a CLOSED hole, 7.5 mm wide. The battery
    # cable is one 2-pin plug with two loose ends, so the loose ends are fed DOWN through these notches BEFORE they are
    # soldered to the holder; once both are soldered the cable is a closed loop and cannot be threaded (README, step 4).
    for (nx0, nx1) in ((wall - 1, wall + 7.5), (W - wall - 7.5, W - wall + 1)):
        body = body.cut(box(nx0, nx1, 12.0, yb + 1, bz0 - 1, bz1 + 1))
    # sensor lead goes straight up: a slot through the bulkhead right above the slot in the channel roof
    sx0, sx1, sy0, sy1 = P["BULK_LEAD_SLOT"]
    body = body.cut(box(sx0, sx1, sy0, sy1, bz0 - 1, bz1 + 1))
    # snap-fit lid: spring arms with hook windows and pull lips in the bottom wall, hinge ribs with nose pockets on the top wall
    body = body_snap_features(body, W, H, wall, yb, P["H_ARMS"], P["H_TAB_XS"])
    # keyhole peg pockets in 10 mm bosses on the back wall (pegs live on the backplate)
    stem_pass = P["PEG_STEM_L"] - 0.2
    head_ch = P["PEG_HEAD_L"] + 0.7
    boss_t = stem_pass + head_ch + P["PEG_POCKET_BACK"]
    slot_w = P["PEG_STEM_D"] + 2 * P["PEG_SLOT_CLR"]
    head_w = P["PEG_HEAD_D"] + 2 * P["PEG_HEAD_CLR"]
    drop = P["PEG_DROP"]
    for px in P["PEG_XS"]:
        for pz in P["PEG_ZS"]:
            body = body.union(box(px - 8, px + 8, D - boss_t, yb + EPS, pz - drop - head_w / 2 - 2, pz + 8))
    # board cradle (USB end against the left wall)
    body = body.union(board_cradle(g["x0"], g["zc"], g["pcb_top"], yb, wall, setback=P["USB_SETBACK"]))
    # BH18650-PC2 holder bay: ribs HOLDER_RIB_T (3 mm) thick and HOLDER_RIB_H (12 mm) tall, lead gaps in both end ribs, ends of the top rib open
    hx0 = P["HOLDER_X0"] - P["HOLDER_CLR"]; hx1 = P["HOLDER_X0"] + P["HOLDER_L"] + P["HOLDER_CLR"]
    hz0 = P["HOLDER_Z0"] - P["HOLDER_CLR"]; hz1 = P["HOLDER_Z0"] + P["HOLDER_W"] + P["HOLDER_CLR"]
    rt, rh, gap = P["HOLDER_RIB_T"], P["HOLDER_RIB_H"], P["HOLDER_LEAD_GAP"]
    zm = (hz0 + hz1) / 2
    rib_z0 = (wall - EPS) if not P["H_BASEMENT"] else hz0 - rt       # with a basement the ribs become a shelf off the back wall
    for (xa, xb) in ((hx0 - rt, hx0), (hx1, hx1 + rt)):
        body = body.union(box(xa, xb, yb - rh, yb + EPS, rib_z0, zm - gap / 2))
        body = body.union(box(xa, xb, yb - rh, yb + EPS, zm + gap / 2, hz1 + rt))
    body = body.union(box(hx0 - rt, hx1 + rt, yb - rh, yb + EPS, rib_z0, hz0))
    body = body.union(box(hx0 + 10.0, hx1 - 10.0, yb - rh, yb + EPS, hz1, bz0 + EPS))
    # standoff ribs: the holder's underside (with its two solder pins, one at each end) stands HOLDER_STANDOFF off the back wall on
    # three cross ribs; the pins and the wires soldered to them live in the gap and leave through the end-rib gaps
    for fx in (0.25, 0.5, 0.75):                # clear of the maker's two mounting-hole rings under the base (7 to 15 mm in from each end)
        rx = hx0 + fx * (hx1 - hx0)
        body = body.union(box(rx - 1.5, rx + 1.5, g["holder_back"], yb + EPS, hz0, hz1))
    # snap arms at both ends of the holder: each rises from the back wall beside the holder's end face and hooks 0.8 mm over
    # its front face with a 45 deg barb, so the holder stays in with the lid off. Press the holder straight in to fit it.
    at, aw, az0, ae = P["HOLDER_ARM"]
    holder_front = g["holder_front"]
    ab = ae + P["HOLDER_CLR"]
    ayc = holder_front - 0.05 - ae
    for (xf, sgn) in ((hx0, 1), (hx1, -1)):                    # xf = arm's inner face, sgn = direction the barb points
        # review: the arm stood inside the 3 mm end rib, which made its back 12 mm rigid. Slot it free above and below for
        # the rib's full height and thin the rib behind it, leaving only a short root block at the back wall.
        ra, rb = sorted((xf, xf - sgn * rt))
        body = body.cut(box(ra - EPS, rb + EPS, yb - rh - EPS, yb, az0 - 1.0, az0))
        body = body.cut(box(ra - EPS, rb + EPS, yb - rh - EPS, yb, az0 + aw, az0 + aw + 1.0))
        oa, ob = sorted((xf - sgn * at, xf - sgn * rt))
        body = body.cut(box(oa, ob, yb - rh - EPS, yb - P["HOLDER_ARM_ROOT"], az0 - EPS, az0 + aw + EPS))
        xa, xb = sorted((xf, xf - sgn * at))
        body = body.union(box(xa, xb, ayc - 0.4 - 1.25 * ab - 0.5, yb + EPS, az0, az0 + aw))
        pts = [(xf - sgn * EPS, ayc + ab), (xf + sgn * ab, ayc), (xf + sgn * ab, ayc - 0.4), (xf - sgn * EPS, ayc - 0.4 - 1.25 * ab)]
        body = body.union(cq.Workplane("XY").polyline(pts).close().extrude(aw).translate((0, 0, az0)))
    # antenna inside the box, upright on the right: the SMA jack's neck slides into a slotted shelf from the front (nut and
    # washer off first) and its own nut clamps it (flange under the shelf, washer and nut on top); the antenna body snaps
    # into a C-clip above
    ax, ay, ad = P["ANT_X"], P["ANT_Y"], P["ANT_D"]
    sz, st_ = P["ANT_SHELF_Z"], P["ANT_SHELF_T"]
    shelf = box(ax - 8.0, W - wall + EPS, ay - 9.5, yb + EPS, sz, sz + st_)
    shelf = shelf.cut(box(ax - P["ANT_SLOT_W"] / 2, ax + P["ANT_SLOT_W"] / 2, ay - 11.0, ay, sz - 1, sz + st_ + 1))
    shelf = shelf.cut(cyl_z(ax, ay, P["ANT_SLOT_W"], sz - 1, sz + st_ + 1))
    body = body.union(shelf)
    cz_ = P["ANT_CLIP_Z"]
    clip = box(ax - ad / 2 - 2.5, ax + ad / 2 + 2.5, ay - ad / 2 - 2.0, yb + EPS, cz_ - 3, cz_ + 3)
    clip = clip.cut(cyl_z(ax, ay, ad + 0.6, cz_ - 4, cz_ + 4))
    clip = clip.cut(box(ax - (ad - 0.6) / 2, ax + (ad - 0.6) / 2, ay - ad, ay, cz_ - 4, cz_ + 4))
    body = body.union(clip)
    # cable tie saddle on the back wall for the lead bundle (tie tunnel along X)
    for (sx_, sz_) in P["SADDLES"]:
        body = body.union(tie_saddle(sx_, sz_, yb, along="X"))
    # USB-C opening in the left wall, USB_SLOT_W x USB_SLOT_H (14.0 x 8.0) with rounded corners and a 1 mm stepped lead-in outside
    uy = g["pcb_top"] - P["USB_OPEN_CY"]
    uw, uh = P["USB_SLOT_W"], P["USB_SLOT_H"]
    body = body.cut(box(-1, wall + 1, uy - uh / 2, uy + uh / 2, g["zc"] - uw / 2, g["zc"] + uw / 2).edges("|X").fillet(2.0))
    body = body.cut(box(-1, 1.0, uy - uh / 2 - 1, uy + uh / 2 + 1, g["zc"] - uw / 2 - 1, g["zc"] + uw / 2 + 1).edges("|X").fillet(3.0))
    # window through the back wall for the backplate's spring catch (replaces the security screw)
    ww = P["CATCH_WIN"][0]
    body = body.cut(box(P["CATCH_X"] - ww / 2, P["CATCH_X"] + ww / 2, yb - 1, D + 1, g["win_z0"], g["win_z1"]))
    # optional knock-out: SMA bulkhead in the top wall
    kx, ky = P["SMA_KO"]
    body = knockout_z(body, kx, ky, P["SMA_HOLE_D"], H, H - wall)
    # hanging bar interface: a thickened strip inside the bottom wall carries a dovetail channel that is open at the
    # back (wall side) and closed at the front; the bar's plate slides in from behind and the wall locks it. The Hall
    # lead slot goes up through the channel roof UNDER the holder (slot Y 6.5..10.5, holder front face Y=6.2), so the
    # leads have to be fed up and folded forward before the holder is pressed in.
    sw2 = P["DT_STRIP_W"] / 2
    strip_y0 = P["TONGUE_H"] + P["TONGUE_CLR"] + 0.5
    body = body.union(box(W / 2 - sw2, W / 2 + sw2, strip_y0, yb + EPS, wall - EPS, g["strip_top"]))
    m2, t2, dh = P["DT_MOUTH"] / 2, P["DT_TOP"] / 2, P["DT_H"]
    body = body.cut(prism_xz([(W / 2 - m2, -1.0), (W / 2 + m2, -1.0), (W / 2 + m2, 0.0), (W / 2 + t2, dh), (W / 2 - t2, dh), (W / 2 - m2, 0.0)],
                             P["DT_Y0"], D + 1.0))
    li = P["DT_LEADIN"]
    body = body.cut(prism_xz([(W / 2 - m2 - li, -1.0), (W / 2 + m2 + li, -1.0), (W / 2 + m2 + li, 0.0), (W / 2 + t2 + li, dh + li), (W / 2 - t2 - li, dh + li), (W / 2 - m2 - li, 0.0)],
                             D - li, D + 1.0))
    wy0, wy1 = P["BAR_WIRE_Y"]
    body = body.cut(box(W / 2 - P["BAR_WIRE_W"] / 2, W / 2 + P["BAR_WIRE_W"] / 2, wy0, wy1, -1.0, g["strip_top"] + 1.0))
    # cleaning-mode button: a plain round hole through the bottom wall, behind the right latch arm and clear of the channel
    # strip; the button goes up through it from below and its own nut clamps it from inside
    if P["BTN16_ON"]:
        bx_, by_ = P["BTN16_XY"]
        body = body.cut(cyl_z(bx_, by_, P["BTN16"][0], -1.0, wall + 1.0))
    # peg pockets are cut last so no internal rib can refill a head chamber
    for px in P["PEG_XS"]:
        for pz in P["PEG_ZS"]:
            body = body.cut(keyhole_y(px, pz - drop, head_w, slot_w, drop, D - stem_pass, D + 1))
            body = body.cut(slot_y(px, pz - drop / 2, drop + head_w, head_w, D - stem_pass - head_ch, D - stem_pass + EPS))
    return body

def build_hanger_lid():
    g = hanger_geom()
    W, H, wall, lt = g["W"], g["H"], g["wall"], g["lid_t"]
    lid = rbox_y(0, W, -lt, 0, 0, H, P["CORNER_R"])
    bz0, bz1 = g["bulk"]
    uy = g["pcb_top"] - P["USB_OPEN_CY"]
    uw = P["USB_SLOT_W"] / 2
    cutouts = ((-1, 6, bz0 - 0.5, bz1 + 0.5), (W - 6, W + 1, bz0 - 0.5, bz1 + 0.5),
               (-1, 5.0, g["zc"] - P["BRD_W"] / 2 - 1.3, g["zc"] + P["BRD_W"] / 2 + 1.3),   # lip cut away along the board's end (the PCB reaches into the lip's depth) and the USB-C opening
               (5.0, W - 5.0, H - wall - P["TONGUE_CLR"] - P["TONGUE_T"] - 0.5, H + 1))   # top segment relieved: the tabs locate the top edge and the lid must pivot there
    lid = lid.union(lid_tongue(W, H, wall, (), cutouts))
    # USB-C with the lid on: the plug's overmold runs 0.75 mm into the lid's thickness, so the lid edge is hollowed from
    # behind over the opening, leaving USB_LID_SKIN (1.4 mm) of face skin over the plug
    lid = lid.cut(box(-1, wall + 0.6, -lt + P["USB_LID_SKIN"], 1, g["zc"] - uw, g["zc"] + uw))
    lid = lid_snap_features(lid, W, H, wall, P["H_ARMS"], P["H_TAB_XS"])
    lid = lid.union(lid_header_ribs(g["x0"], g["zc"], g["pcb_top"]))
    lid = lid_board_features(lid, g["x0"], g["zc"], g["pcb_top"], lt, flush=True, vertical=P["H_PAD_V"])
    # battery retention: two posts bear on the holder's end blocks and two ribs sit just in front of the cell, so neither
    # can move toward the lid. The middle (x 40..60) stays clear for the Hall leads rising from the bar channel.
    hx0, hl = P["HOLDER_X0"], P["HOLDER_L"]
    hzc = P["HOLDER_Z0"] + P["HOLDER_W"] / 2
    holder_front = g["holder_front"]
    pt_, pw_, pc_ = P["HOLD_POST"]
    for cx in (hx0 + 1.5, hx0 + hl - 1.5):
        lid = lid.union(box(cx - pt_ / 2, cx + pt_ / 2, -EPS, holder_front - pc_, hzc - pw_ / 2, hzc + pw_ / 2))
    cell_front = g["cell_y"] - P["CELL_D"] / 2
    rl, rw, rc = P["CELL_RIB"]
    for xa in (hx0 + 12.0, hx0 + hl - 12.0 - rl):
        lid = lid.union(box(xa, xa + rl, -EPS, cell_front - rc, hzc - rw / 2, hzc + rw / 2))
    return lid.cut(hanger_marks())

def build_hanger_window_gauge():
    """Small test piece that proves the screen lines up BEFORE a full lid is printed: the part of the hanger lid round the
    display window and the two button pads, plus low fences on its inside that hold the board exactly where the body's
    cradle will hold it. Lay the board in face down, turn it over and look: the whole picture must sit inside the window.
    It also proves the display and coil fit under the lid (the board must lie flat on the two ribs, not rock) and that
    the PRG and RST pads click their switches. Prints face down like the lid, no support. This test print is the proof on
    the real parts: it replaces every request to measure the board."""
    g = hanger_geom()
    x0, zc, pt, lt = g["x0"], g["zc"], g["pcb_top"], g["lid_t"]
    lid = build_hanger_lid()
    keep = box(-1, x0 + P["BRD_L"] + 6.0, -lt - 1, pt + 3.0, zc - 18.5, zc + 18.5).union(
           box(-1, 15.9, -lt - 1, pt + 3.0, zc - 21.5, zc + 21.5))                 # the pad column is taller than the board strip
    piece = lid.intersect(keep)
    piece = cq.Workplane("XY").add(max(piece.solids().vals(), key=lambda sol: sol.Volume()))
    clr, ft = P["BRD_CLR"], 1.6
    top = pt + P["BRD_T"] + 0.6
    hw = P["BRD_W"] / 2 + clr
    fences = []
    for sgn in (-1, 1):
        za, zb = sorted((zc + sgn * hw, zc + sgn * (hw + ft)))
        spans = ((17.0, P["BRD_L"] - 4.5),) if sgn > 0 else ((17.0, P["FLEX_FOLD"][0]), (P["FLEX_FOLD"][1], P["BRD_L"] - 4.5))   # RST side: open where the display's flex folds over the edge
        for (fa, fb) in spans:
            fences.append(box(x0 + fa, x0 + fb, -EPS, top, za, zb))                 # along each long edge, clear of the pad slots and the far corners
        ea, eb = sorted((zc + sgn * 7.5, zc + sgn * 10.4))
        fences.append(box(x0 - clr - ft, x0 - clr, -EPS, top, ea, eb))              # stops for the USB end, either side of the socket
    return piece.union(union_all(fences))

def hanger_marks():
    g = hanger_geom()
    return face_marks(g["W"], g["lid_t"], P["H_LOGO"], P["H_WORDMARK"], g["x0"], g["zc"], vertical=P["H_PAD_V"])

def gateway_marks():
    g = gateway_geom()
    return face_marks(g["W"], g["lid_t"], P["G_LOGO"], P["G_WORDMARK"], g["x0"], g["zc"])

def inlay_of(marks, W, H, lid_t):
    """The second-colour body: the marks, trimmed to the MARK_DEPTH (0.6 mm) they occupy in the face."""
    return marks.intersect(box(-1, W + 1, -lid_t, -lid_t + P["MARK_DEPTH"], -1, H + 1))

def build_hanger_bar():
    """Slide-in hanging bar (no screws), T-shaped: a narrow dovetail plate and web join it to the body, and a WIDE bar
    below (BAR_W 88: it enters every common sign's hand hole, the narrowest being about 105) carries the sign level. Saddle
    (the seat, BAR_SADDLE_W 42 for a folded sign up to 38 thick) along the full width, upturned lip at the front with no
    gussets at its root, and a bare Hall sensor in a snug nest under the middle of the seat (Y = -11), reached
    by a tunnel from the bar's back face and kept there by two filament pins. Prints UPRIGHT on the bar's bottom face
    with NO support at all: every bending load is then in-plane, the 45 deg dovetail flanks and the 45 deg spreaders
    are self-supporting, and a 45 deg gusset off the web carries the front of the dovetail plate. Support must never be
    generated inside the sensor tunnel, the nest or the pin holes: it could not be got out again."""
    g = hanger_geom()
    bx0, bx1, wx0, wx1, W = g["bar_x0"], g["bar_x1"], g["web_x0"], g["web_x1"], g["W"]
    w0, w1 = g["plate_w0"] / 2, g["plate_w1"] / 2
    plate = prism_xz([(W / 2 - w0, g["plate_z0"]), (W / 2 + w0, g["plate_z0"]), (W / 2 + w1, g["plate_z1"]), (W / 2 - w1, g["plate_z1"])],
                     g["plate_y0"], g["plate_y1"])
    web = box(wx0, wx1, g["web_y0"], g["web_y1"], g["bar_top"] - EPS, g["plate_bot"] + EPS)
    bar = box(bx0, bx1, g["lip_front"], g["bar_back"], g["bar_bot"], g["bar_top"])
    lip = box(bx0, bx1, g["lip_front"], g["lip_back"], g["bar_bot"], g["lip_top"])
    part = plate.union(web).union(bar).union(lip)
    # the front of the dovetail plate overhangs the BAR (not the bed) when printed upright, where bed supports cannot reach:
    # a 45 deg gusset off the web carries it, so the part prints with no support at all
    gh = g["web_y0"] - g["plate_y0"]
    part = part.union(prism_yz([(g["web_y0"] + EPS, g["plate_bot"] + EPS), (g["plate_y0"], g["plate_bot"] + EPS), (g["web_y0"] + EPS, g["plate_bot"] - gh)], wx0, wx1))
    # spreaders each side of the web carry the wide bar back into the web
    sp = P["BAR_SPREAD"]
    for sgn, xe in ((-1, wx0), (1, wx1)):
        part = part.union(prism_xz([(xe - sgn * EPS, g["bar_top"] - EPS), (xe + sgn * sp, g["bar_top"] - EPS), (xe - sgn * EPS, g["bar_top"] + sp)],
                                   g["web_y0"], g["web_y1"]))
    # gussets: where the web meets the bar (web edges), and at the lip root (bar ends and either side of the middle)
    gw, gl = P["BAR_GUSSET_W"], P["BAR_GUSSET"]
    for (gx0, gx1) in ((wx0, wx0 + gw), (wx1 - gw, wx1)):
        part = part.union(prism_yz([(g["web_y0"] + EPS, g["bar_top"] - EPS), (g["web_y0"] - gl, g["bar_top"] - EPS), (g["web_y0"] + EPS, g["bar_top"] + gl)], gx0, gx1))
    # (no gussets at the lip root any more: a folded sign is up to 38 mm thick and fills the seat right up to the lip; the
    # lip is 9 mm thick and only has to stop the sign sliding forward)
    # saddle across the bar's full width (the handle settles here by gravity)
    sw, sd = P["BAR_SADDLE_W"], P["BAR_SADDLE_D"]
    part = part.cut(box(bx0 - 1, bx1 + 1, g["saddle_y"] - sw / 2, g["saddle_y"] + sw / 2, g["saddle_floor"], g["bar_top"] + 1))
    # Hall sensor: tunnel from the bar's back face forward to the back of the package, a 45 deg ramp up, then the nest.
    # The ROOF (slot_ceil) is one level from the bar's back face to the front of the nest; only the floors step and ramp.
    # So the easy way in is with the bar held upside down: the sensor slides along the roof, nothing to climb. The only
    # break in the roof is the first stage of the pin holes (further down): a slot one 0.2 mm layer deep, just short of the nest.
    hw, nw = g["slot_hw"], g["nest_hw"]
    step = g["nest_floor"] - g["slot_floor"]
    yb0, yf = g["nest_y_back"], g["nest_y_back"] + P["HALL_FUNNEL_Y"]
    part = part.cut(box(W / 2 - hw, W / 2 + hw, yf, g["bar_back"] + 1, g["slot_floor"], g["slot_ceil"]))
    # last stretch before the nest: floor ramps up 45 deg and the side walls close in from the tunnel width to the nest width
    approach = box(W / 2 - hw, W / 2 + hw, yb0 + step, yf + EPS, g["slot_floor"], g["slot_ceil"]).union(
        prism_yz([(yb0 - EPS, g["nest_floor"]), (yb0 + step + EPS, g["slot_floor"]), (yb0 + step + EPS, g["slot_ceil"]), (yb0 - EPS, g["slot_ceil"])], W / 2 - hw, W / 2 + hw))
    funnel = cq.Workplane("XY").polyline([(W / 2 - nw, yb0 - 2 * EPS), (W / 2 + nw, yb0 - 2 * EPS), (W / 2 + hw, yf + 2 * EPS), (W / 2 - hw, yf + 2 * EPS)]).close() \
        .extrude(g["slot_ceil"] - g["slot_floor"] + 2.0).translate((0, 0, g["slot_floor"] - 1.0))
    part = part.cut(approach.intersect(funnel))
    part = part.cut(box(W / 2 - nw, W / 2 + nw, g["slot_y_front"], yb0 + EPS, g["nest_floor"], g["slot_ceil"]))
    # lead route: tunnel along the bar behind the saddle; then a groove up the BACK of the web that is open so the wires
    # simply lay in (one short closed band keeps them there); then a groove along the top of the plate to the roof slot
    cw2 = P["BAR_WIRE_W"] / 2 - 1
    ty0 = g["saddle_y"] + sw / 2
    tstep = g["slot_floor"] - g["wire_z0"]          # the deeper wire trench ends in a 45 deg ramp too, so nothing pushed along it meets a square step
    part = part.cut(box(W / 2 - cw2, W / 2 + cw2, ty0 + tstep, g["bar_back"] + 1, g["wire_z0"], g["slot_ceil"]))
    part = part.cut(prism_yz([(ty0 - EPS, g["slot_floor"]), (ty0 + tstep + EPS, g["wire_z0"]), (ty0 + tstep + EPS, g["slot_ceil"]), (ty0 - EPS, g["slot_ceil"])], W / 2 - cw2, W / 2 + cw2))
    band0, band1 = P["WEB_BAND"]
    for (za, zb) in ((g["wire_z0"], band0), (band1, g["plate_z1"] + 1)):
        part = part.cut(box(W / 2 - cw2, W / 2 + cw2, g["web_y0"] + 2.5, g["web_y1"] + 1, za, zb))
    part = part.cut(box(W / 2 - cw2, W / 2 + cw2, g["web_y0"] + 2.5, g["web_y1"] - 2.5, band0 - EPS, band1 + EPS))
    wy0, wy1 = P["BAR_WIRE_Y"]
    part = part.cut(box(W / 2 - cw2, W / 2 + cw2, wy0 + 0.5, g["plate_y1"] + 1, g["plate_z1"] - 1.5, g["plate_z1"] + 1))
    # retaining pins: two offcuts of 2.85 mm filament, 6.0 to 6.5 mm long, stand right behind the package, one each side of its
    # legs, so the sensor cannot slide back out of its nest. They drop into holes in the saddle floor (6.6 mm deep, so a pin
    # never stands proud of the saddle) and the sign's handle sits over them.
    # The holes cross the tunnel's bridged roof. So that roof still prints cleanly, the hole opens in stages (the usual FDM
    # trick): first roof layer = one slot right across, so its bridge lines run wall to wall; second = a square, bridged
    # the short way; round from the third layer up. Nothing has to be drilled. A 2 mm hole under each pin, through the
    # bar's underside, lets it be pushed out with a 1.5 mm rod and drains the cavity. That 2 mm hole is also the ledge the
    # pin stands on, and the ledge is thin (bar bottom to pin hole bottom = 1.4 mm). "Stop by feel" is not safe: a 3 mm drill
    # used to ease a tight pin hole gets a flag of tape 6 mm from its tip, is twisted by hand only, and stops when the tape
    # reaches the saddle floor (the README and the bar drawing say so).
    pd, lay = P["HALL_PIN_D"], 0.2
    pins = hall_pin_xys(g)
    sxw = max(hw, P["HALL_PIN_X"] + pd / 2)
    part = part.cut(box(W / 2 - sxw, W / 2 + sxw, pins[0][1] - pd / 2, pins[0][1] + pd / 2, g["slot_ceil"] - EPS, g["slot_ceil"] + lay))
    for (px_, py_) in pins:
        part = part.cut(cyl_z(px_, py_, pd, g["slot_floor"] - 2.0, g["slot_ceil"]))
        part = part.cut(box(px_ - pd / 2, px_ + pd / 2, py_ - pd / 2, py_ + pd / 2, g["slot_ceil"] + lay - EPS, g["slot_ceil"] + 2 * lay))
        part = part.cut(cyl_z(px_, py_, pd, g["slot_ceil"] + 2 * lay - EPS, g["saddle_floor"] + 1.0))
        part = part.cut(cyl_z(px_, py_, P["HALL_PIN_PUSH_D"], g["bar_bot"] - 1.0, g["slot_floor"] - 2.0 + EPS))
    return part

def hall_pin_xys(g):
    """Pin centres: each pin's edge meets the package's rear corner 0.2 mm behind it."""
    pw = P["HALL_PKG"][0]
    r, dx = 2.85 / 2, P["HALL_PIN_X"] - pw / 2          # the PIN's radius (2.85 filament), not the hole's
    py = g["nest_y_back"] + 0.2 + math.sqrt(max(r * r - dx * dx, 0.0))
    return [(g["W"] / 2 + s * P["HALL_PIN_X"], py) for s in (-1, 1)]

def build_hanger_backplate():
    g = hanger_geom()
    W, H, D = g["W"], g["H"], g["D"]
    bw, bh, bt = P["BP_W"], P["BP_H"], P["BP_T"]
    x0, z0 = (W - bw) / 2, (H - bh) / 2
    plate = rbox_y(x0, x0 + bw, D, D + bt, z0, z0 + bh, P["CORNER_R"])
    # four countersunk wall screws (No.8 / 4 mm), heads on the front face under the body
    ins = P["BP_SCREW_INSET"]
    for (sx, sz) in ((x0 + ins, z0 + ins), (x0 + bw - ins, z0 + ins), (x0 + ins, z0 + bh - ins), (x0 + bw - ins, z0 + bh - ins)):
        plate = plate.cut(csk_hole_y(sx, sz, D, D + bt, P["BP_SCREW_D"], P["BP_SCREW_CSK_D"], (P["BP_SCREW_CSK_D"] - P["BP_SCREW_D"]) / 2))
    # spring catch: a tongue in the plate's front skin (root at the bottom, U-slot around it, free space behind) with a
    # nose that springs into the window in the body's back wall once the body has dropped onto the pegs. Push the nose
    # back through the window (lid off) to release.
    cx, z0, cw, ct, cl, gap, sl = P["CATCH_X"], P["CATCH_Z0"], P["CATCH_W"], P["CATCH_T"], P["CATCH_L"], P["CATCH_GAP"], P["CATCH_SLOT"]
    plate = plate.cut(box(cx - cw / 2 - sl, cx + cw / 2 + sl, D + ct, D + bt + 1, z0, z0 + cl + sl))            # free space behind, open to the wall face (support reaches the tongue)
    for (ax, bx) in ((cx - cw / 2 - sl, cx - cw / 2), (cx + cw / 2, cx + cw / 2 + sl)):
        plate = plate.cut(box(ax, bx, D - 1, D + ct + EPS, z0, z0 + cl + sl))                                       # side slots
    plate = plate.cut(box(cx - cw / 2 - sl, cx + cw / 2 + sl, D - 1, D + ct + EPS, z0 + cl, z0 + cl + sl))       # top slot
    nz0 = z0 + P["CATCH_NOSE_Z"]
    nz1 = nz0 + P["CATCH_NOSE_H"]
    nose = prism_yz([(D + EPS, nz0), (D - P["CATCH_NOSE"], nz0), (D - P["CATCH_NOSE"], nz1 - 1.2), (D - 1.1, nz1), (D + EPS, nz1)], cx - cw / 2, cx + cw / 2)
    plate = plate.union(nose)
    # push pad above the nose: a screwdriver on it pushes the tongue back and stays clear of the window edge while lifting
    pp, ph, pz = P["CATCH_PAD"]
    plate = plate.union(box(cx - 3.0, cx + 3.0, D - pp, D + EPS, nz1 + 1.0, nz1 + 1.0 + ph))
    # four mushroom pegs standing off the front face, head underside chamfered for printing
    sl, hl, sd, hd, ch = P["PEG_STEM_L"], P["PEG_HEAD_L"], P["PEG_STEM_D"], P["PEG_HEAD_D"], P["PEG_CHAMFER"]
    for px in P["PEG_XS"]:
        for pz in P["PEG_ZS"]:
            stem = cyl_y(px, pz, sd, D - sl - EPS, D + EPS)
            c_len = (hd - sd) / 2                      # 45 deg cone from the stem out to the head diameter (no 90 deg step)
            cone = cone_y(px, pz, hd, sd, D - sl - c_len, D - sl + EPS)
            head = cyl_y(px, pz, hd, D - sl - hl, D - sl - c_len + EPS)
            plate = plate.union(stem).union(cone).union(head)
    return plate

def hanger_refs():
    """Reference solids for the assembly (not printed)."""
    g = hanger_geom()
    W, yb = g["W"], g["y_back"]
    refs = {}
    refs["heltec"] = (heltec_ref(g["x0"], g["zc"], g["pcb_top"]), (0.10, 0.45, 0.20))
    # holder (box with a trough) and cell
    hx0, hz0 = P["HOLDER_X0"], P["HOLDER_Z0"]
    hl, hwd, hh = P["HOLDER_L"], P["HOLDER_W"], P["HOLDER_H"]
    cz = hz0 + hwd / 2
    cy = g["cell_y"]
    holder = box(hx0, hx0 + hl, g["holder_front"], g["holder_back"], hz0, hz0 + hwd)
    # open-topped trough like the real holder; its sprung contacts take up the end play, so the trough is cell length + 1
    tx0, tx1 = hx0 + hl / 2 - P["CELL_L"] / 2 - 0.5, hx0 + hl / 2 + P["CELL_L"] / 2 + 0.5
    holder = holder.cut(cyl_x(cy, cz, P["CELL_D"] + 0.5, tx0, tx1))
    holder = holder.cut(box(tx0, tx1, g["holder_front"] - 1, cy, cz - (P["CELL_D"] + 0.5) / 2, cz + (P["CELL_D"] + 0.5) / 2))
    pin_in, pin_l, pin_w = P["HOLDER_PIN"]
    for pxh in (hx0 + pin_in, hx0 + hl - pin_in):
        holder = holder.union(box(pxh - pin_w / 2, pxh + pin_w / 2, g["holder_back"] - EPS, g["holder_back"] + pin_l, cz - pin_w / 2, cz + pin_w / 2))
    refs["holder"] = (holder, (0.15, 0.15, 0.15))
    cx = hx0 + hl / 2
    refs["cell"] = (cyl_x(cy, cz, P["CELL_D"], cx - P["CELL_L"] / 2, cx + P["CELL_L"] / 2), (0.20, 0.55, 0.85))
    # cleaning-mode button: head under the bottom wall, threaded metal body up through the hole, nut on the wall's inner
    # face, then the plug-in socket (or the bare pins) standing up into the bay under the battery
    if P["BTN16_ON"]:
        hole, hd, hh, bd, nut, nut_t = P["BTN16"]
        bx_, by_ = P["BTN16_XY"]
        btn = cyl_z(bx_, by_, hd, -hh, 0.0).union(cyl_z(bx_, by_, bd - 0.2, -EPS, P["BTN16_METAL_L"])).union(cyl_z(bx_, by_, nut, g["wall"], g["wall"] + nut_t))
        btn = btn.union(cyl_z(bx_, by_, 17.0 if P["BTN16_USE_SOCKET"] else 12.0, P["BTN16_METAL_L"] - EPS, btn16_len()))     # socket envelope, latch tab included
        refs["clean_button"] = (btn, (0.75, 0.75, 0.78))
    # bare flat Hall sensor (DRV5032FA, TO-92 style) in its nest under the saddle, marked face up toward the magnet, three legs running back
    pw, pl, pt = P["HALL_PKG"]
    lw, lp, ll = P["HALL_LEG"]
    sy, sz = g["sensor_y"], g["sensor_z"]
    carrier = box(W / 2 - pw / 2, W / 2 + pw / 2, sy - pl / 2, sy + pl / 2, sz - pt / 2, sz + pt / 2)
    for k in (-1, 0, 1):
        carrier = carrier.union(box(W / 2 + k * lp - lw / 2, W / 2 + k * lp + lw / 2, sy + pl / 2 - EPS, sy + pl / 2 + ll, sz - lw / 2, sz + lw / 2))
    refs["hall_carrier"] = (carrier, (0.05, 0.05, 0.05))
    refs["hall_pin"] = (union_all([cyl_z(px_, py_, 2.85, g["slot_floor"] - 2.0, g["saddle_floor"]) for (px_, py_) in hall_pin_xys(g)]), (0.9, 0.9, 0.9))
    # top of a folded sign (reference = Rubbermaid FG6112xx, the narrowest common hand hole): a plate with a hand hole whose
    # top edge rests in the saddle. The hole is SIGN_HOLE_CLR wider than the bar. Magnet in the underside of the handle, over the sensor.
    bar_bot = g["saddle_floor"] + P["TAG_CLR"]
    hole_w = P["BAR_W"] + P["SIGN_HOLE_CLR"]
    st = P["SIGN_T"] / 2
    bar = box(W / 2 - hole_w / 2 - 28, W / 2 + hole_w / 2 + 28, sy - st, sy + st, bar_bot - P["SIGN_HOLE_H"] - 14, bar_bot + P["HANDLE_H"])
    bar = bar.cut(box(W / 2 - hole_w / 2, W / 2 + hole_w / 2, sy - st - 1, sy + st + 1, bar_bot - P["SIGN_HOLE_H"], bar_bot))
    bar = bar.cut(cyl_z(W / 2, sy, P["MAGNET_D"] + 0.2, bar_bot - 1, bar_bot + P["TAG_WALL"] + P["MAGNET_T"]))
    refs["sign_handle"] = (bar, (0.95, 0.80, 0.10))
    refs["magnet"] = (cyl_z(W / 2, sy, P["MAGNET_D"], bar_bot + P["TAG_WALL"], bar_bot + P["TAG_WALL"] + P["MAGNET_T"]), (0.6, 0.6, 0.65))
    # SMA jack + stubby antenna, upright in the shelf and clip
    ax, ay, sz, st_ = P["ANT_X"], P["ANT_Y"], P["ANT_SHELF_Z"], P["ANT_SHELF_T"]
    top = sz + st_
    ant = cyl_z(ax, ay, 6.0, sz - 15.0, sz - 2.0)                      # jack rear body and cable boot
    ant = ant.union(cyl_z(ax, ay, 8.6, sz - 2.0, sz))                     # flange under the shelf
    ant = ant.union(cyl_z(ax, ay, 6.3, sz - EPS, top + 9.0))              # thread through the shelf
    ant = ant.union(cyl_z(ax, ay, 9.0, top + 0.05, top + 2.6))            # washer and nut on top of the shelf
    ant = ant.union(cyl_z(ax, ay, 9.2, top + 2.8, top + 12.5))            # the antenna's brass connector
    ant = ant.union(cyl_z(ax, ay, P["ANT_D"], top + 12.5, top + 2.8 + P["ANT_L"]))   # black body
    refs["stub_antenna"] = (ant, (0.2, 0.2, 0.2))
    # USB-C cable plugged in with the lid ON (proves the opening): 12.35 x 6.5 overmold (USB-IF maximum), its face 0.45 mm
    # short of the receptacle, 6.65 mm nose inside the receptacle. No window insert: the display's own glass is behind the bezel.
    uy = g["pcb_top"] - P["USB_OPEN_CY"]
    face = g["x0"] - P["USB_NOSE"] - 0.45
    plug = box(face - 24.0, face, uy - 3.25, uy + 3.25, g["zc"] - 6.175, g["zc"] + 6.175)
    plug = plug.union(box(face - EPS, face + 6.65, uy - 1.2, uy + 1.2, g["zc"] - 4.1, g["zc"] + 4.1))
    refs["usb_plug"] = (plug, (0.5, 0.5, 0.5))
    return refs

# --------------------------------------------------------------------------------------
# GATEWAY
# --------------------------------------------------------------------------------------
def gateway_geom():
    W, H, D, wall, lt = P["G_W"], P["G_H"], P["G_D"], P["WALL"], P["LID_T"]
    g = dict(W=W, H=H, D=D, wall=wall, y_back=D - wall, lid_t=lt,
             x0=P["G_BRD_X0"], zc=P["G_BRD_ZC"], pcb_top=P["G_PCB_TOP_Y"])
    g["cable_y"] = g["pcb_top"] - P["USB_OPEN_CY"]       # plug axis = cable axis
    g["cable_z"] = P["G_CABLE_ZC"]
    return g

def build_gateway_body():
    g = gateway_geom()
    W, H, D, wall, yb = g["W"], g["H"], g["D"], g["wall"], g["y_back"]
    body = rbox_y(0, W, 0, D, 0, H, P["CORNER_R"])
    body = body.cut(rbox_y(wall, W - wall, -1, yb, wall, H - wall, P["CORNER_R"] - wall))
    body = body_snap_features(body, W, H, wall, yb, P["G_ARMS"], P["G_TAB_XS"])
    body = body.union(board_cradle(g["x0"], g["zc"], g["pcb_top"], yb, wall))
    # USB-C cable entry: notch in the left wall open to the front (cable drops in, lid closes it)
    cy, cz, nw = g["cable_y"], g["cable_z"], P["G_CABLE_NOTCH_W"]
    body = body.cut(box(-1, wall + 1, -1, cy + P["G_CABLE_D"], cz - nw / 2, cz + nw / 2))
    # tie saddle right behind the entry: block on the back wall, tie tunnel along Z behind the cable
    sx0, sx1, sy = P["G_SADDLE"]
    sad = box(sx0, sx1, sy, yb + EPS, cz - 7, cz + 7)
    sad = sad.cut(box(sx0 + 2.0, sx1 - 2.0, sy + 1.0, sy + 3.0, cz - 8, cz + 8))
    body = body.union(sad)
    # SMA bulkhead on the top wall: 14 mm pad thickened to 3 mm, 6.5 D-hole with a 6.0 flat
    ax, ay = P["G_SMA"]
    body = body.union(cyl_z(ax, ay, P["SMA_PAD_D"], H - P["SMA_WALL"], H - wall + EPS))
    dh = cyl_z(ax, ay, P["SMA_HOLE_D"], H - P["SMA_WALL"] - 1, H + 1)
    dh = dh.cut(box(ax + (P["SMA_FLAT"] - P["SMA_HOLE_D"] / 2), ax + 6, ay - 6, ay + 6, H - P["SMA_WALL"] - 2, H + 2))
    body = body.cut(dh)
    # pigtail tie saddle near the jack
    body = body.union(tie_saddle(105.0, 62.0, yb, along="X"))
    # ventilation: intake slots in the bottom wall, exhaust slots in the top wall (offset toward the back)
    v = P["G_VENT"]
    for i in range(v["n"]):
        for yv in v["ys"]:
            xb = v["bot_x0"] + i * v["pitch"]
            body = body.cut(box(xb, xb + v["len"], yv - v["w"] / 2, yv + v["w"] / 2, -1, wall + 1))
            xt = v["top_x0"] + i * v["pitch"]
            body = body.cut(box(xt, xt + v["len"], yv - v["w"] / 2 + 2.0, yv + v["w"] / 2 + 2.0, H - wall - 1, H + 1))
    # wall mount: two keyholes through the back wall plus a lower anti-lift screw hole
    for (kx, kz) in P["G_KEYHOLES"]:
        body = body.cut(keyhole_y(kx, kz - P["KEY_SLOT_L"], P["KEY_HEAD_D"], P["KEY_SLOT_W"], P["KEY_SLOT_L"], yb - 1, D + 1))
    lx, lz = P["G_LOWER_SCREW"]
    body = body.cut(cyl_y(lx, lz, P["BP_SCREW_D"], yb - 1, D + 1))
    return body

def build_gateway_lid():
    g = gateway_geom()
    W, H, wall, lt = g["W"], g["H"], g["wall"], g["lid_t"]
    lid = rbox_y(0, W, -lt, 0, 0, H, P["CORNER_R"])
    cz = g["cable_z"]
    cutouts = ((-1, 6, cz - P["G_CABLE_NOTCH_W"] / 2 - 0.5, cz + P["G_CABLE_NOTCH_W"] / 2 + 0.5),
               (5.0, W - 5.0, H - wall - P["TONGUE_CLR"] - P["TONGUE_T"] - 0.5, H + 1))
    lid = lid.union(lid_tongue(W, H, wall, (), cutouts))
    lid = lid_snap_features(lid, W, H, wall, P["G_ARMS"], P["G_TAB_XS"])
    lid = lid.union(lid_header_ribs(g["x0"], g["zc"], g["pcb_top"]))
    lid = lid_board_features(lid, g["x0"], g["zc"], g["pcb_top"], lt)
    # knock-out for a 12 mm panel button on GPIO3 (factory reset), skin left outside
    bx, bz, bd = P["G_BTN_KO"]
    lid = lid.cut(cyl_y(bx, bz, bd, -lt + P["KNOCKOUT_SKIN"], 1))
    return lid.cut(gateway_marks())

def gateway_refs():
    g = gateway_geom()
    W, H, yb = g["W"], g["H"], g["y_back"]
    refs = {}
    refs["heltec"] = (heltec_ref(g["x0"], g["zc"], g["pcb_top"]), (0.10, 0.45, 0.20))
    cy, cz = g["cable_y"], g["cable_z"]
    nose = g["x0"] - P["USB_NOSE"]
    plug = box(nose - 6.5 - 24.0, nose - 6.5, cy - 3.25, cy + 3.25, cz - 6.2, cz + 6.2)   # overmold 24 long (assumed)
    plug = plug.union(box(nose - 6.6, nose + 6.0, cy - 1.2, cy + 1.2, cz - 4.1, cz + 4.1))
    refs["usb_plug"] = (plug, (0.5, 0.5, 0.5))
    refs["usb_cable"] = (cyl_x(cy, cz, P["G_CABLE_D"], -40.0, nose - 6.5 - 24.0 + 1), (0.3, 0.3, 0.3))
    ax, ay = P["G_SMA"]
    refs["sma_jack"] = (cyl_z(ax, ay, 6.3, H - 12.0, H + 8.0).union(cyl_z(ax, ay, 9.2, H, H + 3.0)), (0.8, 0.7, 0.3))
    refs["whip_antenna"] = (cyl_z(ax, ay, P["WHIP_D"], H + 8.0, H + 8.0 + P["WHIP_L"]), (0.15, 0.15, 0.15))
    cxw = g["x0"] + P["OLED_ACT_CX"]; czw = g["zc"] + P["OLED_ACT_CY"]
    refs["window_insert"] = (box(cxw - P["INSERT_W"] / 2 + 0.1, cxw + P["INSERT_W"] / 2 - 0.1, -P["INSERT_POCKET"], -P["INSERT_POCKET"] + P["INSERT_T"],
                                 czw - P["INSERT_H"] / 2 + 0.1, czw + P["INSERT_H"] / 2 - 0.1), (0.7, 0.9, 1.0))
    return refs

# --------------------------------------------------------------------------------------
# 2D drawings (ezdxf): section views with dimension entities
# --------------------------------------------------------------------------------------
import ezdxf

DIM_OVR = {"dimtxt": 2.5, "dimasz": 1.5, "dimexo": 0.8, "dimexe": 1.0, "dimgap": 0.6, "dimdec": 1}

MAPS = {
    "front": lambda v: (v.x, v.z),      # looking at the lid (X right, Z up)
    "top":   lambda v: (v.x, -v.y),     # looking down: wall at the bottom of the view
    "side":  lambda v: (-v.y, v.z),     # looking from the right: lid/hook to the right, wall to the left
}
PLANES = {"front": "XZ", "top": "XY", "side": "YZ"}

def section_edges(solids, view, at):
    """Section edges of one or more solids on the named plane at the given coordinate."""
    origin = {"front": (0, at, 0), "top": (0, 0, at), "side": (at, 0, 0)}[view]
    out = []
    for s in solids:
        try:
            sec = cq.Workplane(PLANES[view], origin=origin).add(s.val()).section()
            out.append(sec.edges().vals())
        except Exception as ex:      # a plane that misses the solid gives an empty section
            out.append([])
    return out

def dxf_new():
    doc = ezdxf.new("R2010", setup=True)
    for name, color in (("OUTLINE", 7), ("REF", 8), ("DIMS", 1), ("TEXT", 3), ("NOTES", 4)):
        doc.layers.add(name, color=color)
    return doc

def dxf_edges(msp, edges, view, off, layer="OUTLINE"):
    m = MAPS[view]; ox, oy = off
    for e in edges:
        if e.geomType() == "LINE":
            a, b = m(e.startPoint()), m(e.endPoint())
            msp.add_line((a[0] + ox, a[1] + oy), (b[0] + ox, b[1] + oy), dxfattribs={"layer": layer})
        else:
            n = 36
            pts = [m(e.positionAt(i / n)) for i in range(n + 1)]
            msp.add_lwpolyline([(p[0] + ox, p[1] + oy) for p in pts], dxfattribs={"layer": layer})

def dxf_dim(msp, kind, p1, p2, line_pos, off, text=None):
    """Linear dimension: kind 'h' (horizontal, line at y=line_pos) or 'v' (vertical, line at x=line_pos)."""
    ox, oy = off
    a = (p1[0] + ox, p1[1] + oy); b = (p2[0] + ox, p2[1] + oy)
    if kind == "h":
        d = msp.add_linear_dim(base=(a[0], line_pos + oy), p1=a, p2=b, angle=0, dimstyle="EZDXF",
                               override=DIM_OVR, text=text if text else "<>", dxfattribs={"layer": "DIMS"})
    else:
        d = msp.add_linear_dim(base=(line_pos + ox, a[1]), p1=a, p2=b, angle=90, dimstyle="EZDXF",
                               override=DIM_OVR, text=text if text else "<>", dxfattribs={"layer": "DIMS"})
    d.render()

def dxf_text(msp, s, pos, off, h=3.0, layer="TEXT"):
    msp.add_text(s, height=h, dxfattribs={"layer": layer}).set_placement((pos[0] + off[0], pos[1] + off[1]))

def write_part_drawing(path, title, solid, views, notes=()):
    """views: list of dicts {view, at, off, label, dims:[(kind,p1,p2,line_pos,text)], refs:[solids]}."""
    doc = dxf_new(); msp = doc.modelspace()
    dxf_text(msp, title, (0, 0), (0, 0), h=5.0)
    for v in views:
        off = v["off"]
        edges = section_edges([solid], v["view"], v["at"])[0]
        dxf_edges(msp, edges, v["view"], off)
        for r in v.get("refs", []):
            dxf_edges(msp, section_edges([r], v["view"], v["at"])[0], v["view"], off, layer="REF")
        dxf_text(msp, v["label"], v.get("label_at", (0, -8)), off, h=2.8)
        for dm in v.get("dims", []):
            dxf_dim(msp, dm[0], dm[1], dm[2], dm[3], off, dm[4] if len(dm) > 4 else None)
    y = -10.0
    for n in notes:
        dxf_text(msp, n, (0, y), (0, 0), h=2.5, layer="NOTES"); y -= 4.0
    doc.saveas(path)

# --------------------------------------------------------------------------------------
# previews (OpenSCAD) and exports
# --------------------------------------------------------------------------------------
OPENSCAD = "/Applications/OpenSCAD-2021.01.app/Contents/MacOS/OpenSCAD"

def render_scad(out_dir, name, body, camera="0,0,0,60,0,25,0", size="1200,900"):
    scad = os.path.join(out_dir, name + ".scad")
    png = os.path.join(out_dir, name + ".png")
    open(scad, "w").write(body)
    if not os.path.exists(OPENSCAD):
        print("  (OpenSCAD not found, skipped", png, ")"); return
    r = subprocess.run([OPENSCAD, "-o", png, "--autocenter", "--viewall", "--projection=o",
                        "--imgsize=" + size, "--colorscheme=Tomorrow", "--camera=" + camera, scad],
                       capture_output=True, text=True, timeout=600)
    if r.returncode != 0:
        print("  OpenSCAD failed for", name, r.stderr[-400:])

def scad_import(rel, color=None, translate=(0, 0, 0)):
    s = 'translate([%g,%g,%g]) ' % translate
    if color:
        s += 'color([%g,%g,%g]) ' % color
    return s + 'import("%s");\n' % rel

def export_part(out_dir, name, wp):
    cq.exporters.export(wp, os.path.join(out_dir, name + ".step"))
    cq.exporters.export(wp, os.path.join(out_dir, name + ".stl"), tolerance=0.01, angularTolerance=0.1)
    print("  %-22s %s" % (name, bbox_str(wp)))

PRINT_ORIENT = {"hanger_body": "back_down", "hanger_lid": "face_down", "hanger_bar": "upright",
                "hanger_backplate": "back_down", "gateway_body": "back_down", "gateway_lid": "face_down"}

def export_print_stl(print_dir, name, wp, orient, companion=None):
    """STL already rotated into its print orientation (build direction = +Z, part resting on z=0). A companion (the
    second-colour inlay) gets exactly the same move, so the two line up when loaded together in the slicer."""
    def turn(shape):
        if orient == "back_down":        # back face (max Y) onto the bed: y -> -z
            return shape.rotate(cq.Vector(0, 0, 0), cq.Vector(1, 0, 0), -90)
        if orient == "face_down":        # outer face (min Y) onto the bed: y -> +z
            return shape.rotate(cq.Vector(0, 0, 0), cq.Vector(1, 0, 0), 90)
        return shape
    solid = turn(wp.val())
    bb = solid.BoundingBox()
    shift = cq.Vector(-bb.xmin, -bb.ymin, -bb.zmin)
    solid = solid.translate(shift)
    if companion is not None:
        cname, cwp = companion
        comp = cq.Compound.makeCompound([turn(sh).translate(shift) for sh in cwp.vals()])
        cq.exporters.export(cq.Workplane("XY").add(comp), os.path.join(print_dir, cname + ".stl"), tolerance=0.01, angularTolerance=0.1)
    cq.exporters.export(cq.Workplane("XY").add(solid), os.path.join(print_dir, name + ".stl"), tolerance=0.01, angularTolerance=0.1)
    bb = solid.BoundingBox()
    return "%-18s %-10s footprint %.0f x %.0f mm, height %.1f mm" % (name, orient, bb.xlen, bb.ylen, bb.zlen)

def export_assembly(path, parts):
    """parts: list of (name, workplane, color, translate)."""
    assy = cq.Assembly(name=os.path.splitext(os.path.basename(path))[0])
    for (name, wp, col, tr) in parts:
        assy.add(wp, name=name, color=cq.Color(*col), loc=cq.Location(cq.Vector(*tr)))
    try:
        assy.export(path)
    except AttributeError:
        assy.save(path)
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
